SleepyUnicon/Overwatch/case/2_bezel_back.png

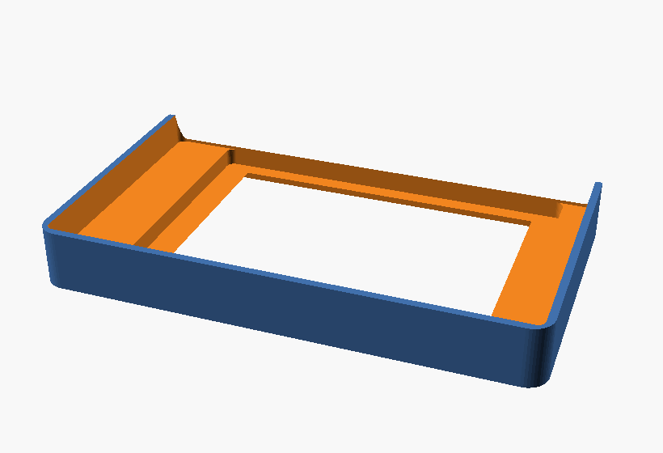
case/2_bezel_back.png
