SleepyUnicon/Overwatch/case/4_tray_vents.png

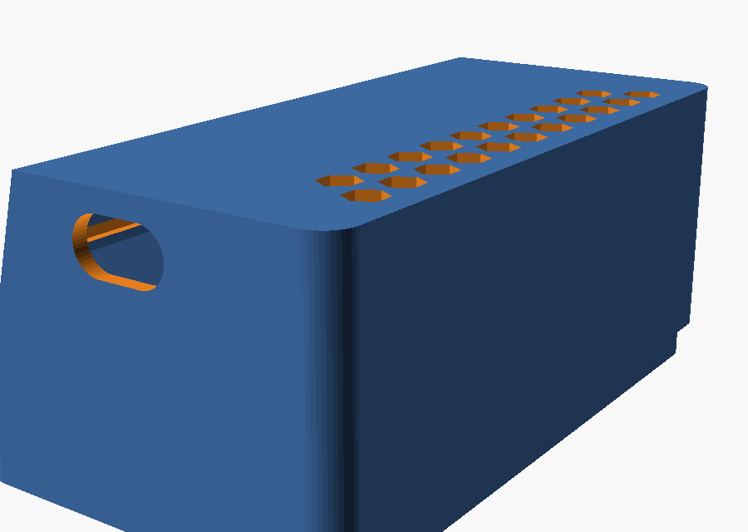
case/4_tray_vents.png
