SleepyUnicon/Overwatch/case/6_tray_right.png

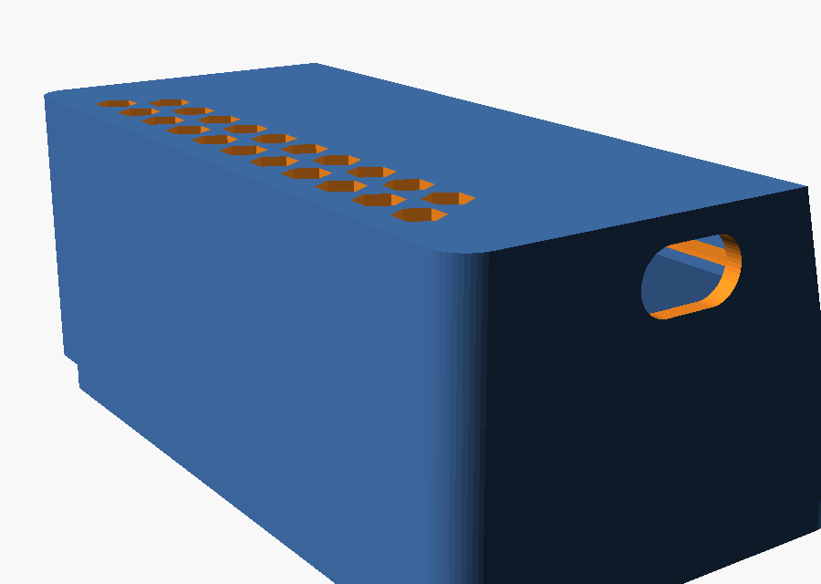
case/6_tray_right.png
