SleepyUnicon/Overwatch/case/7_tray_iso.png

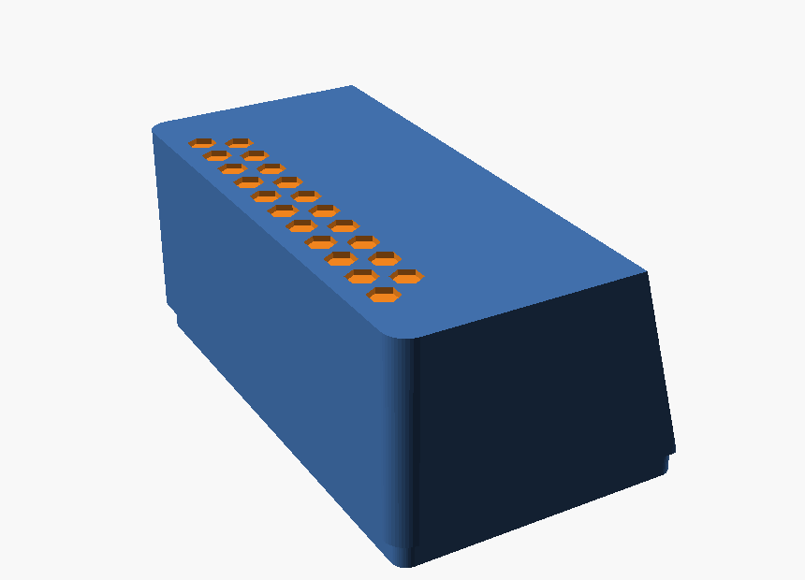
case/7_tray_iso.png
