SleepyUnicon/Overwatch/case/v2/1_face.png

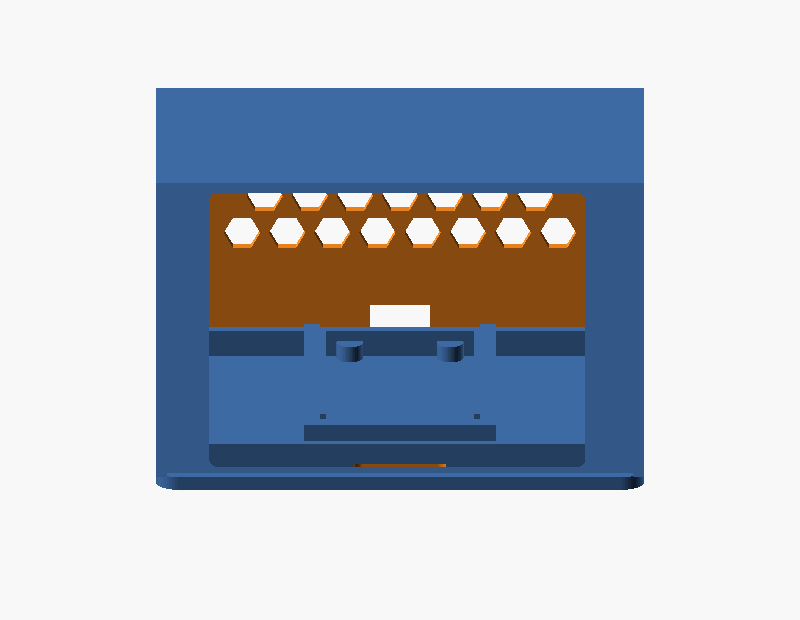
case/v2/1_face.png
