SleepyUnicon/Overwatch/case/v2/2_iso.png

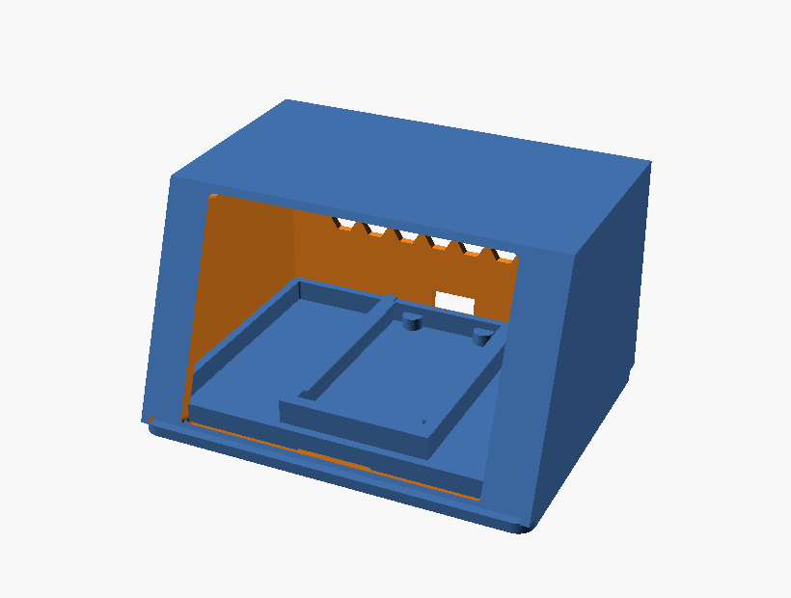
case/v2/2_iso.png
