SleepyUnicon/Overwatch/case/v2/3_back_vent.png

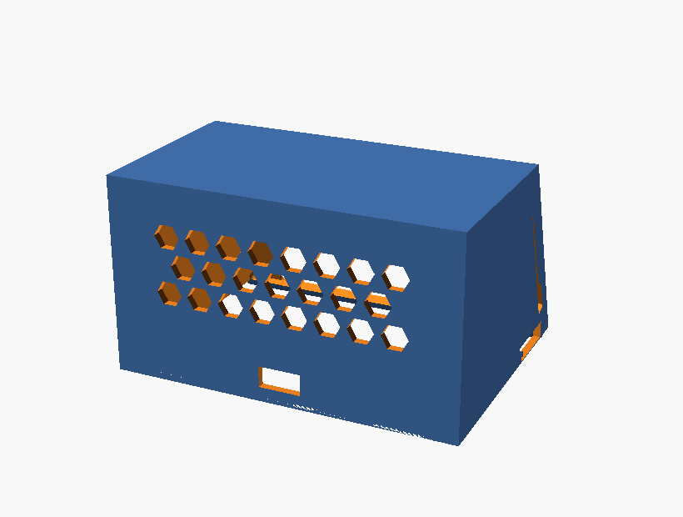
case/v2/3_back_vent.png
