SleepyUnicon/Overwatch/case/v2/4_side.png

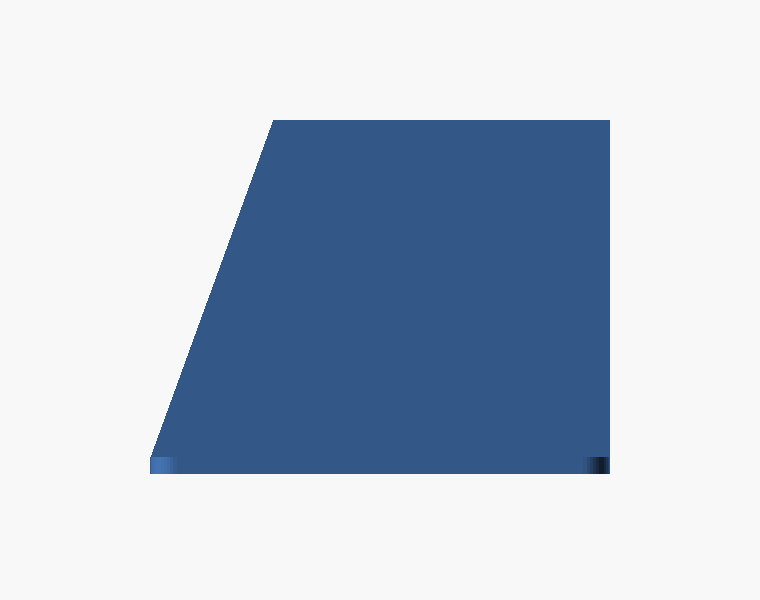
case/v2/4_side.png
