SleepyUnicon/Overwatch/case/v2/5_base.png

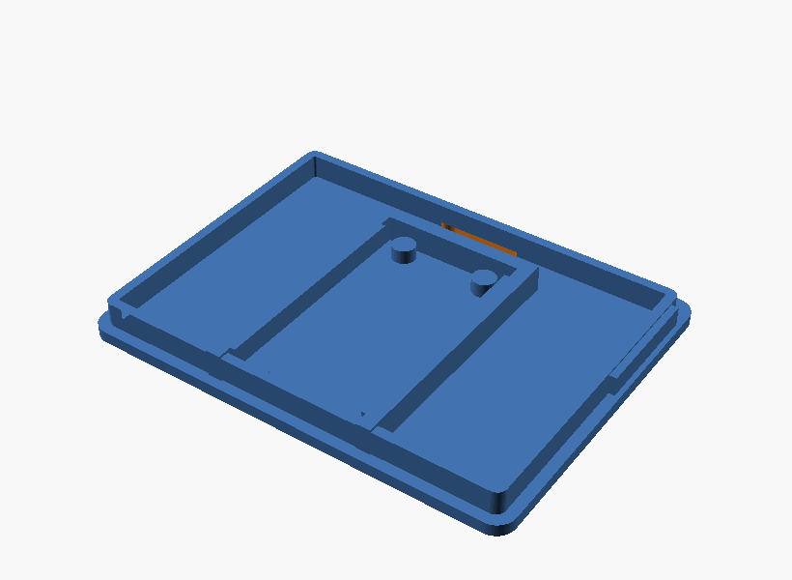
case/v2/5_base.png
