SleepyUnicon/Overwatch/case/v2/6_key.png

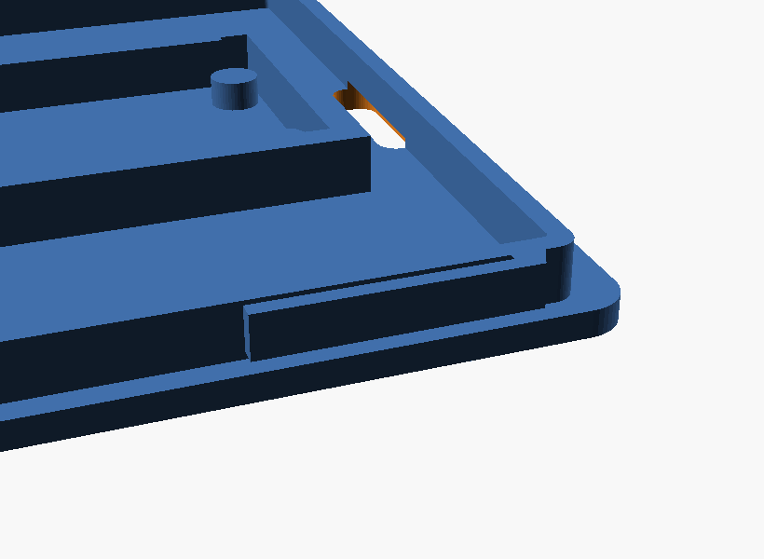
case/v2/6_key.png
