SleepyUnicon/Overwatch/design/car-dial/dial_actual_size.png

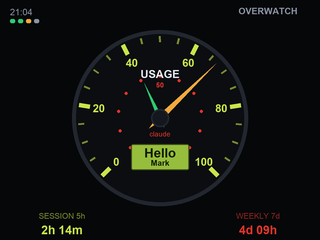
design/car-dial/dial_actual_size.png
