SleepyUnicon/Overwatch/reveal/page_gauges.png

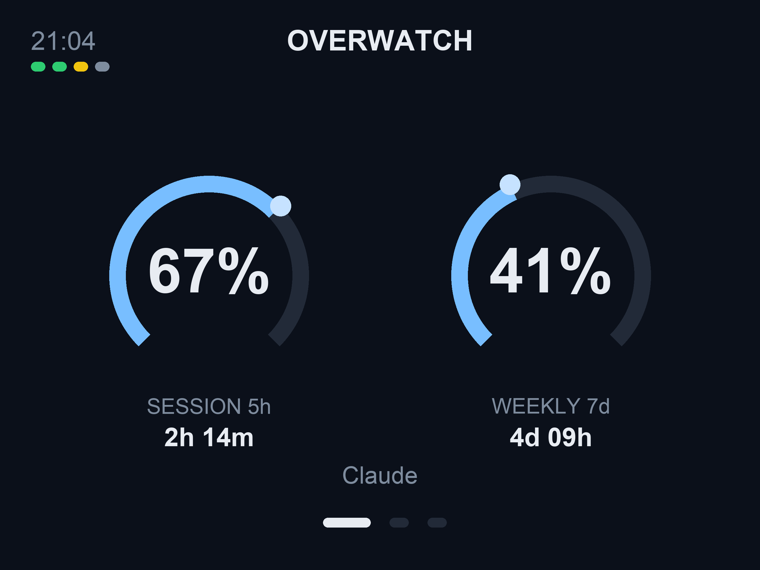
reveal/page_gauges.png
