SleepyUnicon/Overwatch/reveal/page_spotify.png

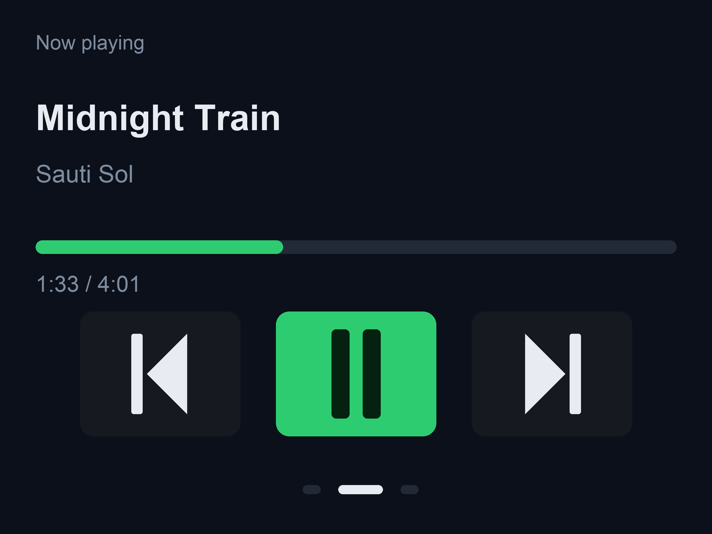
reveal/page_spotify.png
