SleepyUnicon/Overwatch/reveal/screen_strip.png

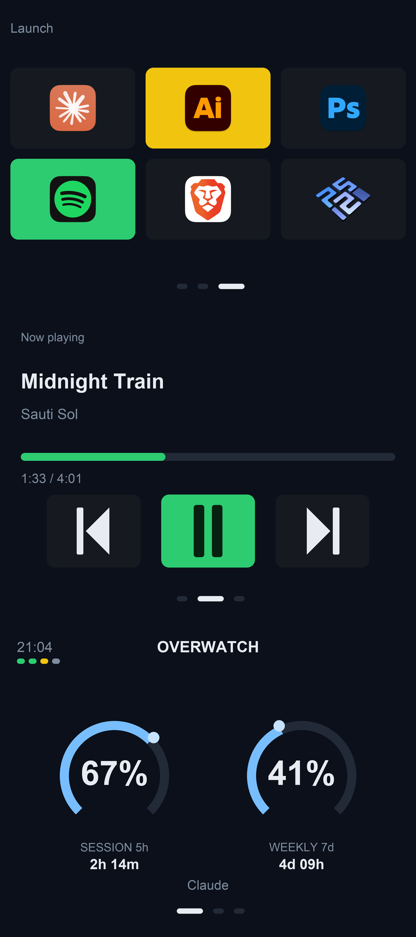
reveal/screen_strip.png
