SleepyUnicon/Overwatch/pc/cli.py

"""One binary: the setup, the status check, and the bridge itself.

A customer downloads a single file and runs it. There is no Python to install,
no virtualenv to build, no repository to clone, and nothing left behind that
they have to keep in place -- `overwatch install` copies the binary into
~/.overwatch/bin and points the login service at that copy, so the download is
disposable the moment it finishes.

This replaces install.sh. The shell version needed Python 3.9+ on the machine,
built a virtualenv, and pulled two packages from PyPI at install time -- three
things that could fail on a customer's machine for reasons they could do
nothing about, and one of them (an unpinned PyPI resolve) meant two people
installing a week apart could get different software.

The status line shim stays a shell script on purpose. It runs on EVERY status
line render, many times a minute, and a frozen binary takes 100-400 ms to start
because it unpacks itself first -- that delay would land in the customer's
prompt. A few lines of sh start in single-digit milliseconds.
"""
import argparse
import glob
import os
import shutil
import subprocess
import sys
import textwrap
import time

from pc import (install_codex_hooks, install_hooks, install_statusline,
                macperm, ota,
                protocol, statusline_source, update, win_driver)
# Eagerly, unlike the other providers, which are imported inside the functions
# that use them to keep the frozen binary's start-up cheap. This one costs
# nothing to import (os, and claude_state, which is json/os/sys/time) and it
# has to be a module attribute rather than a local: `overwatch status` reads it,
# and a test has to be able to replace it without a real slot directory in
# reach -- the scan behind it deletes files.
from pc.providers import codex_state
from pc.version import RELEASE_VERSION

# Resolved per call, not at import. These used to be module constants, which
# meant every path was fixed by whatever HOME happened to be when the module
# loaded -- untestable without a subprocess, and quietly wrong for any caller
# that changes HOME.
LABEL = "com.overwatch.bridge"


def _home():
    return os.path.expanduser("~")


def overwatch_home():
    return os.path.join(_home(), ".overwatch")


def bin_dir():
    return os.path.join(overwatch_home(), "bin")


def installed_bin():
    # .exe on Windows: without the extension the copy is not executable, and
    # the Scheduled Task would register a path Windows refuses to launch.
    name = "overwatch.exe" if sys.platform == "win32" else "overwatch"
    return os.path.join(bin_dir(), name)


def shim_path():
    return os.path.join(overwatch_home(), "overwatch-statusline.sh")


def hook_shim_path():
    return os.path.join(overwatch_home(), "overwatch-hook.sh")


def log_path():
    return os.path.join(overwatch_home(), "bridge.log")


def log_hint():
    """Where to actually READ the log on this platform.

    Not the same as log_path(), and the difference cost a person sixteen
    hours. launchd is told StandardOutPath and writes bridge.log; the systemd
    unit says nothing about output, so on Linux everything goes to the journal
    and bridge.log is never created. `install` printed the path anyway, so a
    Linux user following their own install output finds no such file, and
    concludes the daemon never ran -- while it is running, and has been
    logging the reason it cannot work, somewhere else.

    Windows keeps the file: the Scheduled Task runs the daemon through a shim
    that redirects into it.
    """
    if sys.platform.startswith("linux"):
        return "journalctl --user -u overwatch-bridge"
    return log_path()


def launcher_path():
    """The script the Scheduled Task runs, so the bridge starts with no window.

    A console program started by a Scheduled Task gets a console window, and
    on the first Windows machine it was installed on that window sat on the
    desktop for as long as the service ran (2026-08-29: "it should be some
    service in the background, not a UI app"). wscript.exe can start a
    program with its window hidden; this is the one-line script that asks
    it to. Written in ASCII with the profile taken from the environment,
    because a non-ASCII path inside a .vbs depends on the machine's code
    page, and the machine in question had a Hebrew user name.
    """
    return os.path.join(overwatch_home(), "overwatch-bridge.vbs")


LAUNCHER_VBS = "\n".join((
    "' Starts the OVERWATCH bridge with no window. Written by `overwatch install`;",
    "' the Scheduled Task \"Overwatch bridge\" runs it at every logon.",
    'Set sh = CreateObject("WScript.Shell")',
    'home = sh.ExpandEnvironmentStrings("%USERPROFILE%")',
    # VBScript doubles a quote to embed one: this runs
    #   "<home>\.overwatch\bin\overwatch.exe" run --log "<home>\.overwatch\bridge.log"
    # with window style 0 (hidden) and without waiting for it to finish.
    'sh.Run """" & home & "\\.overwatch\\bin\\overwatch.exe"" run --log """'
    ' & home & "\\.overwatch\\bridge.log""", 0, False',
    "",
))


def pid_path():
    """Where the running daemon records its pid: ~/.overwatch/bridge.pid.

    Derived from the program's own location (its directory's parent), not
    from ~. A login service runs in the user's environment rather than the
    one that registered it, so the two can disagree about what ~ is -- and
    when they do, the pid lands where nothing will look for it.

    Beside the program, not inside its directory: an update rotates
    ~/.overwatch/bin to bin.old with the old daemon still running from it, and a
    pid file that moved with the directory is one restart() can no longer
    find -- leaving the old daemon holding the serial port against the new.
    """
    return os.path.join(overwatch_home(), "bridge.pid")


def pid_paths():
    """Every place a daemon may have left its pid.

    The same set _kill_recorded_daemon sweeps, named once so that "is it
    running?" and "stop it" cannot drift apart -- and with the frozen
    build's own choice added. claude_usage_bridge writes beside its
    directory when frozen, which IS pid_path() once installed but lands in
    the build directory when the binary is run in place.
    """
    paths = [pid_path(),
             os.path.join(bin_dir(), "bridge.pid"),
             os.path.join(bin_dir() + ".old", "bridge.pid")]
    if _frozen():
        paths.append(os.path.join(
            os.path.dirname(os.path.dirname(_self_path())), "bridge.pid"))
    # And beside whatever binary we would START, which is not always one of
    # the above: a frozen build run in place out of dist/ writes its pid
    # there. Without this the page reported "Started (pid N)" and then, one
    # poll later, "Not running" -- both true, neither useful.
    cmd = daemon_start_command()[0]
    if len(cmd) == 2:                     # an overwatch binary, not `python -m`
        paths.append(os.path.join(
            os.path.dirname(os.path.dirname(cmd[0])), "bridge.pid"))
    seen, out = set(), []
    for q in paths:
        if q not in seen:
            seen.add(q)
            out.append(q)
    return tuple(out)


def daemon_holding_lock():
    """Whether a daemon holds ~/.overwatch/bridge.lock. None if it cannot be told.

    Better than the pid file wherever it works, for three reasons: the path
    is fixed however the binary was installed or run, the kernel drops the
    lock when the process dies however it dies, and a recycled pid cannot
    impersonate it. claude_usage_bridge takes this lock for the daemon's
    whole life so that two of them cannot interleave on one cable.

    None means "cannot tell from here" -- Windows has no flock (there the
    exclusive port is the lock), and neither has an unwritable home. The pid
    sweep answers those.

    Opened "a", never "w": the daemon's own open truncates, and a status
    check has no business doing that to a file another process is holding.
    """
    try:
        import fcntl
    except ImportError:
        return None
    path = os.path.join(overwatch_home(), "bridge.lock")
    if not os.path.exists(path):
        return False                  # no daemon has ever run here
    try:
        fh = open(path, "a", encoding="utf-8")
    except OSError:
        return None
    try:
        fcntl.flock(fh.fileno(), fcntl.LOCK_EX | fcntl.LOCK_NB)
    except OSError:
        return True                   # somebody holds it
    else:
        fcntl.flock(fh.fileno(), fcntl.LOCK_UN)
        return False
    finally:
        fh.close()


def daemon_running():
    """Is a bridge daemon running? The lock first, the pid file second.

    Two answers because neither is available everywhere. The lock is the
    better one and is what POSIX gets; Windows has no flock, so there the
    pid sweep -- with its image-name filter against recycled pids -- is the
    whole answer.
    """
    held = daemon_holding_lock()
    if held is not None:
        return held
    return daemon_alive() is not None


def daemon_alive(runner=None):
    """The pid of a running bridge daemon, or None.

    Signal 0 alone is not enough. A pid is recycled after a reboot, and the
    number the daemon wrote can belong to something else entirely by the
    time anyone asks -- which would report a stopped daemon as healthy. So
    the process's NAME is checked too, the same filter the Windows backend
    already applies to tasklist for the same reason.

    Nothing here raises: this answers a status question, and a status
    question that throws is worse than one that says "no".
    """
    run = runner or subprocess.run
    for path in pid_paths():
        try:
            with open(path, encoding="utf-8") as f:
                pid = int(f.read().strip())
        except (OSError, ValueError):
            continue
        if pid == os.getpid():
            continue
        try:
            if sys.platform == "win32":
                out = run(["tasklist", "/fi", "PID eq %d" % pid,
                           "/fi", "IMAGENAME eq "
                           + os.path.basename(installed_bin()),
                           "/nh", "/fo", "csv"],
                          capture_output=True, text=True,
                          **update.ota.NO_WINDOW)
                # tasklist exits ZERO with no match and prints a notice,
                # so the pid has to appear in the output to count.
                if str(pid) in (out.stdout or ""):
                    return pid
                continue
            out = run(["ps", "-p", str(pid), "-o", "comm="],
                      capture_output=True, text=True, timeout=5)
        except (OSError, subprocess.SubprocessError):
            continue
        name = os.path.basename((out.stdout or "").strip()).lower()
        if name and ("overwatch" in name or "python" in name):
            return pid
    return None


def daemon_start_command():
    """How to start the bridge on this machine, as (command, cwd).

    The installed binary first -- that is what the login service runs and
    what a kit user has. Then this program, when it is the frozen build
    being run in place. Only then the checkout, which needs pyserial in the
    interpreter running it: true for a developer, not for anybody else.

    The cwd travels WITH the command because it is not free to choose. A
    binary can be started from anywhere and ~/.overwatch is the tidiest place
    for it; `-m pc.cli` cannot, because Python resolves the package from
    the working directory and started anywhere else it exits on
    "No module named 'pc'".
    """
    inst = installed_bin()
    if os.path.exists(inst):
        return [inst, "run"], overwatch_home()
    if _frozen():
        return [_self_path(), "run"], overwatch_home()
    root = os.path.dirname(os.path.dirname(os.path.abspath(__file__)))
    return [sys.executable, "-m", "pc.cli", "run"], root


def settings_path():
    return os.path.join(_home(), ".claude", "settings.json")


def plist_path():
    return os.path.join(_home(), "Library", "LaunchAgents", LABEL + ".plist")


def unit_path():
    return os.path.join(_home(), ".config", "systemd", "user",
                        "overwatch-bridge.service")


# Windows has no launchd and no systemd. A Scheduled Task with an at-logon
# trigger is the equivalent that needs no admin rights and no service wrapper.
TASK_NAME = "Overwatch bridge"

# The oldest Claude Code that carries usage figures in its status line payload.
# 2.1.0 does not carry rate_limits at all; 2.1.100 does. Below this every step
# of the install succeeds and the panel stays blank forever.
MIN_CLAUDE = (2, 1, 100)

# Set by the tests to skip registering a real login service. The launchd label
# and the systemd unit name are constants while everything else is scoped to
# $HOME, so without this a test under a temporary HOME still boots out the
# real agent of whoever is logged in.
def _skip_service():
    return os.environ.get("OVERWATCH_SKIP_SERVICE") == "1"


def _frozen() -> bool:
    return getattr(sys, "frozen", False)


def _self_path() -> str:
    """The binary to copy into place. sys.executable is the frozen binary."""
    return sys.executable if _frozen() else os.path.abspath(sys.argv[0])


def _shim_source(name: str = "overwatch-statusline.sh") -> str:
    """A shim's text, from the bundle when frozen, the tree when not.

    One source of truth either way -- tools/ is what the build embeds, so the
    shipped shim and the one in the repository cannot drift apart. Any new
    shim added here must also be added to the --add-data list in
    tools/build_binary.sh, or it will work from a checkout and be missing
    from every shipped binary.
    """
    if _frozen():
        base = getattr(sys, "_MEIPASS", os.path.dirname(_self_path()))
        return open(os.path.join(base, name), encoding="utf-8").read()
    here = os.path.dirname(os.path.dirname(os.path.abspath(__file__)))
    return open(os.path.join(here, "tools", name), encoding="utf-8").read()


def _write_shim(path: str, name: str) -> None:
    # newline="\n", or Windows writes the shim with CRLF and Git Bash then
    # fails on `case ... in\r` on every status line render and every tool
    # call. The CI CRLF check only ever looked at the files in the repository,
    # never at the copy this function installs.
    # Temp file plus os.replace, NOT open(path, "w").
    #
    # Truncate-in-place has a window in which this file is empty or half
    # written, and Claude Code runs this exact script on EVERY tool call. A
    # hook that starts inside that window hands `sh` an empty file, or a
    # truncated trailing line -- which exits non-zero and gives the tool a
    # FAILING hook. The shim's own closing `exit 0` exists precisely so that
    # Overwatch having a bad day never becomes the user's bad day, and truncating
    # the script defeats it from outside.
    #
    # The window used to be one write during an explicit install, which is bad
    # but rare and observed. This branch made DriftWatchdog call it from the
    # daemon's poll loop, so the same window now opens on a timer, in the
    # background, on a machine whose owner is working. install_statusline._save
    # already writes this way for the user's settings, and the shim's own slot
    # write already uses a pid-named temp plus mv -f; this was the one write
    # that skipped the idiom, and it is the one that became recurring.
    #
    # The temp file is a sibling so os.replace is atomic, and the mode is set
    # BEFORE the rename so the file is never briefly present and non-executable.
    tmp = "%s.overwatch-tmp.%d" % (path, os.getpid())
    try:
        with open(tmp, "w", encoding="utf-8", newline="\n") as f:
            f.write(_shim_source(name))
        os.chmod(tmp, 0o755)
        os.replace(tmp, path)
    except OSError:
        try:
            os.unlink(tmp)
        except OSError:
            pass
        raise


def shim_is_current(path: str, name: str) -> bool:
    """Is the shim at `path` byte-identical to the one we would install?

    Byte-identical, not "close enough": the one difference that has actually
    bitten was line endings, and a comparison that normalised them would have
    called the broken file healthy. Read in binary and compare exactly.

    False on any failure to read. The caller's response to "stale" and to "I
    cannot tell" is the same -- write it again -- and this runs inside the
    daemon's poll loop, where raising is the one outcome worse than a shim
    that stays stale for another five minutes.
    """
    try:
        with open(path, "rb") as f:
            installed = f.read()
    except OSError:
        return False

    try:
        expected = _shim_source(name).encode("utf-8")
    except (OSError, UnicodeDecodeError):
        # The bundle itself is unreadable -- or, since _shim_source opens
        # with encoding="utf-8", readable but not valid UTF-8, which raises
        # UnicodeDecodeError (a ValueError, not an OSError, so it needs its
        # own arm here). Either way there is nothing to compare against.
        # Claiming the installed shim is stale would start a rewrite that
        # cannot succeed and would log the failure every tick; claiming it
        # is current changes nothing. Say current and let the louder failure
        # surface elsewhere.
        return True

    return installed == expected


# ---------------------------------------------------------------- Claude Code


def claude_version():
    """(text, tuple) for the Claude Code on PATH, or (None, None)."""
    exe = shutil.which("claude")
    if not exe:
        return None, None
    try:
        out = subprocess.run([exe, "--version"], capture_output=True, text=True,
                             timeout=30).stdout.strip()
    except Exception:
        return None, None
    head = out.split()[0] if out else ""
    pieces = head.split(".")[:3]
    # Every component has to be a number, or we did not parse a version.
    # Mapping the odd ones to 0 meant "claude version unknown" came back as
    # (0, 0, 0) -- below every floor, so a perfectly good install was reported
    # as TOO OLD, and callers testing `ver is None` never saw it coming.
    if not pieces or not all(x.isdigit() for x in pieces):
        return (out or None), None
    parts = [int(x) for x in pieces]
    while len(parts) < 3:
        parts.append(0)
    return (out or None), tuple(parts)


def desktop_app_present() -> bool:
    """Has Claude Desktop ever written its usage cache on this machine?

    The file, not the application bundle. An installed app that has never run
    has nothing for us to read, and a machine where the app was removed but
    the cache remains still has a (stale, and reported as stale) reading. The
    file is the thing this product actually depends on, so the file is what
    gets asked about.
    """
    from pc.providers import claude_desktop
    try:
        return os.path.exists(claude_desktop.cache_path())
    except Exception:
        return False


def desktop_staleness_note(age_s):
    """Why a Claude Desktop reading is old -- or nothing, when it is not.

    Claude Desktop does not write its usage cache on a clock. It writes after
    a usage fetch, and it only fetches while somebody is actually at the
    machine: step away, lock the screen or let the machine sleep and the file
    simply stops growing. The app is still running and still right, it is
    just not asking. A reading hours old is therefore the ordinary shape of
    "nobody was here", not a fault, and a panel showing one is not stuck.

    Measured from Claude.app 1.40609.0 on 2026-08-31, by reading its own
    bundle and then watching it run: the poll is 15 minutes by default and
    5 only for the half hour after the menubar panel has been opened, it
    skips the fetch entirely once the system has been idle ten minutes or
    the screen is locked, and it fetches at launch and again every time the
    menubar icon is opened. Opening that icon is the one action that
    refreshes on demand: focusing the app window fetches nothing, because
    the chat runs in a web view that never touches this file.

    None of those intervals is quoted below on purpose. They belong to an
    application we do not control, they have already changed twice (a flat
    5 minutes when pc/providers/claude_desktop.py was written, then the
    tray-gated 5/15 split around 2026-08-21 -- arriving without an app
    update, so the cadence is server-controlled and can move again), and a
    number that goes quietly wrong is worse here than no
    number: the reader needs the shape, which does not change, and the one
    action that works.
    """
    from pc.providers import claude_desktop
    if age_s is None or age_s < claude_desktop.STALE_AFTER_S:
        return []
    return [
        "Claude Desktop refreshes this only while you are at the machine,",
        "and stops once it has been idle a while -- so a reading this old",
        "usually means nobody was here, not that anything is broken.",
        "Click the Claude icon in your menu bar to refresh it now.",
    ]


def codex_present() -> bool:
    """Has Codex CLI written a rollout log on this machine?

    The logs, not the binary, for the reason desktop_app_present() gives: the
    file the daemon reads is the thing that matters.
    """
    from pc.providers import codex_cli
    try:
        return bool(codex_cli.recent_rollouts(limit=1))
    except Exception:
        return False


def _announce_codex_hooks() -> None:
    """Say what is about to happen in Codex, before it happens.

    Install is deliberately unattended, so disclosure is the only thing
    standing between us and configuring a SECOND vendor's tool without saying
    so -- and this one is not the tool the customer came here for. The trust
    prompt is the part that has to be said out loud: Codex asks once, in its
    own interface, minutes or days later, and an unexplained dialog from a
    tool the person did not think they were configuring is a support incident
    rather than a feature.

    Wrapped continuation lines start lower case on purpose. The house rule is
    that every sentence starts with a capital; a line that continues one is
    not a new sentence, and capitalising it would read as a stutter.
    """
    print("Overwatch is about to add a hook to Codex as well.")
    print()
    print(f"  File     {install_codex_hooks.hooks_file()}")
    print("  Why      Codex does not record permission prompts in its session")
    print("           log, so without this a Codex session waiting on you")
    print("           looks idle on the panel.")
    print("  Note     The first time the hook runs, Codex asks you once")
    print("           whether to trust it. That prompt is expected, and Overwatch")
    print("           cannot answer it for you. Say yes and the panel can show")
    print("           a Codex session waiting on you; say no and everything")
    print("           else still works.")
    print()


def _install_codex_hooks() -> str:
    """Register the shim with Codex, if there is a Codex here to register with.

    Detected rather than asked about, the same way the Claude Code steps are:
    the product is meant to be plug-and-play. Absent Codex, nothing is written
    at all -- creating a hooks file for a tool that is not installed would
    leave a stranger's configuration on the machine.

    No pointer is written into Codex's config.toml, and none is needed:
    hooks.json is discovered by location alone, verified by firing a real hook
    against a config that mentioned hooks nowhere
    (docs/research/codex-hook-contract.md, F3).
    """
    if not codex_present():
        return "no Codex on this machine, nothing to do"
    # Private to the user, for the same reason ~/.overwatch/state is: these files
    # name the projects someone has open, and the default umask would leave
    # them readable by every account on the machine. Created here rather than
    # left to the shim so the mode is right from the first hook onward.
    state_dir = os.path.join(overwatch_home(), "state-codex")
    os.makedirs(state_dir, exist_ok=True)
    try:
        os.chmod(state_dir, 0o700)
    except OSError:
        pass                 # Windows, where the mode does not apply
    try:
        return install_codex_hooks.install(install_codex_hooks.hooks_file(),
                                           hook_shim_path())
    except install_statusline.SettingsUnreadable as e:
        # Same judgement as the Claude hooks step: the status line is the
        # product and the activity light is a nicety. A hooks file we cannot
        # safely edit costs the user a pip, and is not worth failing an
        # install that has otherwise worked -- still less worth "repairing"
        # another vendor's config by writing our idea of it over theirs.
        return f"skipped ({e})"


def _note_if_no_claude_code():
    """Say what this machine will and will not show, when Claude Code is absent.

    Steps 2 and 3 of the install write a status line and a set of hooks into
    ~/.claude/settings.json. With no Claude Code on the machine nothing ever
    reads that file, so both steps report success and produce nothing -- and
    the customer is left with a device that half works and no way to find out
    why. That is the worst shape a first run can have, and it cost nothing to
    keep quiet about, which is why it stayed quiet.

    A note, not a refusal, and not a failed step. The edits are correct and
    stay correct: install Claude Code tomorrow and it all starts working with
    nothing to redo. Same reasoning as _warn_if_claude_too_old below.
    """
    text, _ = claude_version()
    if text is not None:
        return

    print()
    if codex_present() and not desktop_app_present():
        # A Codex machine. The daemon has known about Codex for a while; this
        # message did not, and told a Codex-edition customer that nothing on
        # the machine reports usage and to install Claude Code.
        print("  !  Claude Code is not installed, so the panel runs on Codex")
        print("     alone: both Codex limits and their countdowns, from the")
        print("     session log Codex already writes. The Claude page stays")
        print("     empty, and there is no activity light -- that needs")
        print("     Claude Code's hooks. The status line and hooks just")
        print("     installed start working by themselves if you add it later.")
        return
    if not desktop_app_present():
        # No source exists. This is not a reduced panel, it is an empty
        # one, and saying anything softer would be misleading.
        print("  !! Nothing on this machine reports usage yet.")
        print("     Overwatch reads figures that Claude Code, Claude Desktop or")
        print("     Codex have already worked out. With none of them installed")
        print("     the panel will connect and then sit blank.")
        print()
        print("       npm install -g @anthropic-ai/claude-code@latest")
        print()
        print("     Nothing here needs redoing afterwards -- it starts on its own.")
        return

    print("  !  Claude Code is not installed, so the panel runs on")
    print("     Claude Desktop alone. That works, with less on it:")
    print()
    print("       Shown    both usage percentages, and how fast the")
    print("                five-hour window is filling")
    print("       Missing  the reset countdowns, and the activity light")
    print()
    # Why, not just what. The countdowns are the part people ask about, and
    # "it is not implemented yet" would be the wrong answer -- there is
    # nothing to implement. Verified across every file, LevelDB store and
    # cache the desktop app writes, 2026-08-28.
    print("     Claude Desktop does not record when either window resets --")
    print("     anywhere, in any file -- so there is no countdown to show and")
    print("     the panel shows a rate instead. The activity light needs")
    print("     Claude Code's hooks.")
    print()
    print("     The status line and hooks just installed are correct and will")
    print("     start working by themselves if you add Claude Code later:")
    print()
    print("       npm install -g @anthropic-ai/claude-code@latest")


def _warn_if_claude_too_old():
    text, ver = claude_version()
    if ver is None or ver >= MIN_CLAUDE:
        return
    # A warning, not a refusal. Everything installed is correct and stays
    # correct, so the moment they update it starts working with nothing to
    # redo; refusing would make them run this again for no reason.
    m = ".".join(str(n) for n in MIN_CLAUDE)
    print()
    print(f"  !! Your Claude Code is {text}, and Overwatch needs {m} or newer.")
    print("     Older versions do not put the usage figures in the status line")
    print("     at all, so the panel will sit blank until you update:")
    print()
    print("       npm install -g @anthropic-ai/claude-code@latest")
    print()
    print("     Nothing else needs redoing -- it starts working on its own.")


# -------------------------------------------------------------------- service


_PLIST_TEMPLATE = """<?xml version="1.0" encoding="UTF-8"?>
<!DOCTYPE plist PUBLIC "-//Apple//DTD plist_path() 1.0//EN" "http://www.apple.com/DTDs/PropertyList-1.0.dtd">
<plist version="1.0">
<dict>
  <key>Label</key><string>{label}</string>
  <key>ProgramArguments</key>
  <array>
{args}  </array>
  <!-- Frozen Python buffers stdout when it is a file, so without this the
       log lags minutes behind the daemon and reads as a hang. -->
  <key>EnvironmentVariables</key>
  <dict><key>PYTHONUNBUFFERED</key><string>1</string></dict>
  <key>RunAtLoad</key><true/>
  <!-- The bridge waits for a board rather than exiting, so KeepAlive is a
       backstop for a crash, not the normal path. ThrottleInterval keeps a
       repeatable crash from becoming a spin. -->
  <key>KeepAlive</key><true/>
  <key>ThrottleInterval</key><integer>10</integer>
  <key>StandardOutPath</key><string>{log}</string>
  <key>StandardErrorPath</key><string>{log}</string>
</dict>
</plist>
"""

def _systemd_exec() -> str:
    """ExecStart, with every argument quoted.

    systemd splits ExecStart on whitespace, so a bare " ".join() broke on any
    space in the interpreter path, the checkout path or $HOME: with a spaced
    home the unit resolved the executable as the first fragment and failed
    with "Failed to locate executable", while `overwatch install` still printed
    "running (systemd)". The launchd and schtasks backends already quote
    per-argument; systemd was the only one that did not, and the CI scenario
    that uses a spaced home asserts only that the unit FILE exists.

    systemd's own quoting: double quotes, with \\ and \" escaped inside.
    """
    out = []
    for a in _service_command():
        out.append('"%s"' % a.replace("\\", "\\\\").replace('"', '\\"'))
    return " ".join(out)


_UNIT_TEMPLATE = """[Unit]
Description=Overwatch USB bridge

[Service]
ExecStart={command}
Environment=PYTHONUNBUFFERED=1
Restart=always
RestartSec=10

[Install]
WantedBy=default.target
"""


def _xml_escape(s: str) -> str:
    return s.replace("&", "&amp;").replace("<", "&lt;").replace(">", "&gt;")


def _service_command():
    """What the login service should run.

    Frozen, that is the copy in ~/.overwatch/bin. From a checkout it is this
    interpreter and the repo's entry SCRIPT -- not `-m pc.cli`.

    `-m` was wrong and silently so. A login service starts with no working
    directory of ours (launchd uses /), so `python -m pc.cli` could not import
    `pc` at all: the agent crash-looped on ModuleNotFoundError every
    ThrottleInterval, forever, writing the same line to bridge.log -- while
    `overwatch status` reported "registered with launchd", because registration
    is not health. Found on the author's own machine 2026-08-28, where it had
    been failing unnoticed.

    Running the script BY PATH fixes it without a WorkingDirectory or a
    PYTHONPATH: Python puts a script's own directory on sys.path, and
    overwatch_main.py sits at the repo root next to `pc/`.
    """
    if _frozen():
        return [installed_bin(), "run"]
    repo = os.path.dirname(os.path.dirname(os.path.abspath(__file__)))
    return [sys.executable, os.path.join(repo, "overwatch_main.py"), "run"]


# How long to keep asking a service manager before believing the answer.
#
# MEASURED, 2026-09-30, on the owner's Mac running `overwatch update` 2.3.0 ->
# 2.3.1. The kickstart went out at 10:21:57, this gave up at 10:22:02, and the
# new daemon's first log line is 10:22:08 -- so the service came up ELEVEN
# seconds after the bounce and the old five-second budget missed it by more
# than half. The message it printed ("launchd reports it is not running -- see
# the log") was true at the instant it was checked, useless six seconds later,
# and sent the reader to run `overwatch install` for nothing. It did that on
# two consecutive updates.
#
# Eleven seconds because `update` has just replaced a 12.8 MB PyInstaller
# bundle: macOS has to assess the signature of a freshly written binary and its
# fifty-one inner Mach-O files before it will exec any of them. A normal
# kickstart, with the binary already assessed, answers in 0.02 s -- measured
# three times running -- so a generous budget costs nothing whenever anything
# is working. It is only spent on the path that is already in trouble, and
# waiting there is better than being wrong quickly.
#
# Thirty, not eleven: that measurement is one machine, warm, with the page
# cache full of the bundle it had just written.
CONFIRM_BUDGET_S = 30.0


def _confirm_delays(budget_s=CONFIRM_BUDGET_S):
    """Escalating waits that add up to about `budget_s`.

    A LIST of sleeps rather than a wall-clock deadline, which is not a style
    choice: the tests for the failure path patch time.sleep to a no-op, and a
    deadline read off time.monotonic() would busy-spin against a clock that
    still moves -- thirty real seconds per test. Counting ticks keeps the loop
    bounded however sleep behaves.

    Short waits first so the ordinary case (0.02 s) still returns at once, then
    longer ones so a slow start is not paid for in a hundred probes.
    """
    delays, total, d = [], 0.0, 0.25
    while total < budget_s:
        delays.append(d)
        total += d
        d = min(d * 1.5, 3.0)
    return delays


def _confirm_running(probe, budget_s=CONFIRM_BUDGET_S) -> bool:
    """Keep asking a service manager whether something is REALLY running.

    All three backends had the same hole and only one of them had learned:
    they read the exit code of the command that started the service and
    called that health. An exit code says a request was accepted. Whether a
    process exists is a different question, and only the supervisor can
    answer it -- which is the lesson recorded above _service_command() and
    measured again on 2026-09-04, when five bootstraps out of five returned
    zero with nothing running.

    So this is the part that is the same everywhere -- ask, and if the answer
    is no, ask again for a few seconds -- and `probe` is the part that is not.
    It is a callable rather than an argv because the QUESTION differs per
    platform and, on Windows, so does its subject: the pid file has to be
    re-read on every attempt, because a daemon that has not started yet has
    not written one.

    See CONFIRM_BUDGET_S for how long, and for the measurement that set it.
    The old budget was five seconds and the thing it was watching took eleven.

    Returns False on anything it cannot recognise. That lean is deliberate
    and it is the whole point -- the one thing this must never do again is
    print a claim it cannot see. Which cuts both ways, and did: "I cannot see
    it" is only honest while it is still true, and saying it after five
    seconds of a start that takes eleven is its own kind of wrong answer.
    """
    said = False
    waited = 0.0
    for d in _confirm_delays(budget_s):
        if probe():
            return True
        # Something on the screen after a few seconds, or a wait this long
        # reads as a hang -- which is what the five-second budget was
        # protecting against, and worth keeping while fixing what it broke.
        if not said and waited >= 4.0:
            said = True
            print("    (still waiting for the service to come up)",
                  file=sys.stderr)
        time.sleep(d)
        waited += d
    # One last look: the final wait is the longest, and giving up without
    # spending it would make the budget shorter than it says it is.
    return bool(probe())


class _Backend:
    """One platform's answer to "start this at login, and keep it running".

    There used to be five sys.platform ladders: one each for install,
    restart, remove, the line the installer prints about what it creates,
    and status. Nothing held them together, so a case could be handled in
    four of them and forgotten in the fifth -- which is not hypothetical. A
    Linux box with no systemd got a considered answer from remove ("no
    systemd here; stop it yourself if you started it") and a shrug from
    status ("unknown on linux"), for the same machine in the same state.

    One object per platform now, chosen once by backend(). That also makes
    this code reachable from a unit test for the first time: a backend can
    be built on any machine and asked what it would run, where before the
    argv handed to launchctl, schtasks and systemctl could only be observed
    by installing for real on that platform. Three Windows defects in this
    file were found by CI rather than by a test for exactly that reason.

    The base class is not abstract -- it IS the behaviour for a platform
    with no supervisor we know how to drive, and every subclass overrides
    only the parts it can do better.
    """

    def creates(self):
        """What installing will put on disk, for the disclosure block.

        None when there is nothing to name.
        """
        return None

    def install(self) -> str:
        return (f"not supported on {sys.platform}; run it yourself: "
                f"{installed_bin()} run")

    def restart(self) -> str:
        return "not running under a supervisor; restart it yourself"

    def halt(self) -> None:
        """Stop the running daemon, leaving the service registered.

        Only Windows needs this, and only right before the update swap: it is
        the one platform that refuses to rename <bin> while the daemon holds
        bin\\overwatch.exe open. Elsewhere a rename does not care what is open, and
        stopping a daemon that launchd or systemd would restart a second later
        buys a gap on the board and nothing else. So: a no-op by default, on
        purpose.

        Not stop() below, which is deliberately a different thing: stop() is
        half of a pair a test run must be able to undo on every platform, and
        it reports what happened. This is best effort, silent, and only where
        an open file handle would otherwise fail a rename.
        """
        return None

    def stop(self, runner=None) -> str:
        """Stop the installed service, without uninstalling it.

        Restart() is what `overwatch update` needs; this pair is what a test run
        needs. The fleet suite drives the real daemon against a real board, so
        it has to take the serial port off the service that owns it and hand
        it back afterwards -- on a machine the user works on, where anything
        that touched the plist, the unit file or the Scheduled Task itself
        would rewrite their own installation on the way past. So: stop and
        start only, and a service that is not installed is an answer rather
        than an error, because start() is called from a finally block where
        an exception would replace the failure the run was there to find.

        runner is subprocess.run unless a caller substitutes one. Resolved at
        call time rather than bound as a default argument, so a test that
        stubs subprocess.run is still in charge of what this can execute.
        """
        return "not running under a supervisor; stop it yourself"

    def start(self, runner=None) -> str:
        """Start the installed service again. See stop() for the pair.

        Not a restart: this assumes stop() ran, and does not go looking for
        anything else to kill. A caller that wants both is asking for
        restart().
        """
        return "not running under a supervisor; start it yourself"

    def remove(self) -> str:
        return "nothing to remove"

    def status(self) -> str:
        return f"unknown on {sys.platform}"


# launchctl exits with an errno. ESRCH is what booting out a job launchd is
# not running gives back ("Boot-out failed: 3: No such process"), which is an
# answer rather than a failure -- see _LaunchdBackend.stop.
_ESRCH = 3


class _LaunchdBackend(_Backend):
    def creates(self):
        return plist_path()

    def install(self) -> str:
        os.makedirs(os.path.dirname(plist_path()), exist_ok=True)
        with open(plist_path(), "w", encoding="utf-8") as f:
            args = "".join(f"    <string>{_xml_escape(a)}</string>\n"
                           for a in _service_command())
            f.write(_PLIST_TEMPLATE.format(label=LABEL, args=args,
                                           log=_xml_escape(log_path())))
        uid = os.getuid()
        # bootout first so a rerun replaces the running agent rather than
        # failing with "service already loaded".
        subprocess.run(["launchctl", "bootout", f"gui/{uid}/{LABEL}"],
                       capture_output=True, **update.ota.NO_WINDOW)
        # ...and then retry, because bootout is asynchronous. The bootstrap
        # immediately after it can fail while launchd is still tearing the old
        # job down, which left a reinstall with no service running at all --
        # observed on the second install of the day, silently.
        #
        # That retry is still worth having, but it was only ever half of this
        # story: it guards a bootstrap that FAILS. A bootstrap that succeeds
        # also starts nothing. Measured on a live machine, with this very
        # plist (RunAtLoad is set in _PLIST_TEMPLATE):
        #
        #   launchctl bootout   gui/501/com.overwatch.bridge   -> rc 0
        #   launchctl bootstrap gui/501 <plist>            -> rc 0
        #   launchctl print     gui/501/com.overwatch.bridge   -> "not running",
        #                                                     runs = 0
        #                          (still not running six seconds later)
        #   launchctl kickstart gui/501/com.overwatch.bridge   -> running, runs = 1
        #
        # So bootstrap registers the job and kickstart is what runs it. Until
        # this line existed the customer was told "running (launchd)" about a
        # job that was registered and idle, and that would not have actually
        # started before their next login.
        for attempt in range(4):
            r = subprocess.run(["launchctl", "bootstrap", f"gui/{uid}", plist_path()],
                               capture_output=True, **update.ota.NO_WINDOW)
            if r.returncode == 0:
                break
            time.sleep(0.5 * (attempt + 1))
        if r.returncode != 0:
            return ("installed, but could not be started: "
                    f"launchctl bootstrap gui/{uid} {plist_path()}")

        # BOOTSTRAP REGISTERS; IT DOES NOT START. A successful bootstrap means
        # launchd has accepted the job, not that anything is running.
        #
        # And this is not a race that sometimes loses. Measured 2026-09-04 by
        # running the old sequence -- bootout, bootstrap, no kickstart -- five
        # times in a row against this very plist: `bootstrap` returned 0 every
        # time and launchd reported "not running" every time. FIVE OUT OF FIVE.
        # RunAtLoad is honoured at LOGIN, not on a bootstrap, so an install left
        # the daemon dead until the user next logged in -- while the installer
        # said it was running. That is why it stayed hidden: anyone who rebooted
        # between installing and looking saw a working service.
        #
        # The observation that started it, straight after an install that had
        # just printed "running (launchd)":
        #
        #     active count = 0
        #     state = not running
        #     last exit code = (never exited)
        #
        # The board went quiet and dozed while the installer said it was fine.
        # This is the same defect tools/burn.sh has in its restore path, and
        # the same lesson _service_command() already records one screen up:
        # registration is not health.
        subprocess.run(["launchctl", "kickstart", "-k", f"gui/{uid}/{LABEL}"],
                       capture_output=True, **update.ota.NO_WINDOW)

        # And then ASK, rather than assume. Everything above is a command that
        # returned zero; none of it is evidence that a process exists. launchd
        # is the only thing that knows, so the claim we print is its answer and
        # not our hope.
        if _confirm_running(lambda: self._is_running(uid)):
            return "running (launchd)"
        return ("registered with launchd, but it is not running -- "
                f"start it with: launchctl kickstart -k gui/{uid}/{LABEL}")

    def _is_running(self, uid) -> bool:
        """Does launchd say a process actually exists? Its answer, not ours.

        Asked by install() and restart() because they were making the same
        claim from different evidence, and only one of them had learned. An
        exit code says a command was accepted; `launchctl print` is the only
        thing that says a process is running, so both ask it.

        One ask. The retrying belongs to _confirm_running(), which the other
        two backends need for the same reason: a kickstart hands the job to
        launchd and returns, so the exec can still be in flight when the first
        print lands.

        Parsed the same defensive way status() is -- launchctl print is a
        human-readable dump, not a contract.
        """
        pr = subprocess.run(["launchctl", "print", f"gui/{uid}/{LABEL}"],
                            capture_output=True, text=True,
                            **update.ota.NO_WINDOW)
        return pr.returncode == 0 and "state = running" in (pr.stdout or "")

    def restart(self) -> str:
        """Bounce the agent, then check that it came back.

        The old body returned "restarted" whenever kickstart exited zero,
        which is the exact defect install() was measured making on 2026-09-04:
        five bootstraps out of five returned zero with nothing running. A
        kickstart is a request to launchd, and a request that was accepted is
        not a process that exists.

        It matters most on the path that calls this. `overwatch update` swaps the
        binary underneath the agent and then bounces it; if the new binary
        cannot start -- a bad download, a missing dylib -- kickstart still
        succeeds and launchd's respawns still fail. Saying "restarted" there
        would send the user away from the one file that explains it.
        """
        uid = os.getuid()
        r = subprocess.run(["launchctl", "kickstart", "-k",
                            f"gui/{uid}/{LABEL}"], capture_output=True, **update.ota.NO_WINDOW)
        if r.returncode != 0:
            return "could not restart it"
        if _confirm_running(lambda: self._is_running(uid)):
            return "restarted"
        # Not a command to paste this time: the command that would have been
        # printed is the one that just ran and left nothing running. What is
        # left to do is read why it died.
        return ("restarted, but launchd reports it is not running -- "
                f"see {log_path()}")

    def stop(self, runner=None) -> str:
        """bootout, not `launchctl stop`.

        The plist sets KeepAlive, so a stopped job is one launchd starts
        straight back up -- the process would be gone for about a second and
        the serial port would be held again before anything else could take
        it. bootout unloads the job; the plist stays exactly where it is, and
        start() below bootstraps that same file back in.

        A job that is not loaded is stopped, not a failure. launchctl exits
        with an errno, and booting out something launchd has never heard of
        gives ESRCH -- "Boot-out failed: 3: No such process". That is an
        ordinary state: a plist on disk whose agent was already booted out,
        by a previous run or by hand. Reported as a failure it aborts the
        fleet agent with "the serial port is probably still held", about a
        port that is in fact free.
        """
        if not os.path.exists(plist_path()):
            return "not installed"
        uid = os.getuid()
        r = (runner or subprocess.run)(
            ["launchctl", "bootout", f"gui/{uid}/{LABEL}"],
            capture_output=True, **update.ota.NO_WINDOW)
        if r.returncode == 0:
            return "stopped"
        if r.returncode == _ESRCH:
            return "stopped (it was not loaded)"
        return f"could not stop it: launchctl bootout gui/{uid}/{LABEL}"

    def start(self, runner=None) -> str:
        """bootstrap, and then kickstart, because bootstrap starts nothing.

        `launchctl bootstrap` registers the job with launchd and exits 0
        without running it, RunAtLoad in the plist notwithstanding. Measured
        on a live machine -- see the block in install(), which had the same
        gap -- a bootstrapped job sits at "not running / runs = 0" for as
        long as you care to watch it, and one kickstart turns it into
        "running / runs = 1" with a pid.

        This is the fleet suite's restore path, called from a finally block
        on a machine someone works at. Answering "started" for a registered
        but idle job is the worst answer available here: the run reports
        success, the daemon never retakes the serial port, and the desk goes
        dark with nothing pointing at the cause. So a kickstart that fails
        is a failed start, even though the job is registered -- what the
        caller asked for is a process holding the port again.
        """
        if not os.path.exists(plist_path()):
            return "not installed"
        uid = os.getuid()
        run = runner or subprocess.run
        r = run(["launchctl", "bootstrap", f"gui/{uid}", plist_path()],
                capture_output=True, **update.ota.NO_WINDOW)
        if r.returncode != 0:
            # No job to kick, and a second failing command would only bury the
            # one line the operator needs to paste.
            return f"could not start it: launchctl bootstrap gui/{uid} {plist_path()}"
        k = run(["launchctl", "kickstart", f"gui/{uid}/{LABEL}"],
                capture_output=True, **update.ota.NO_WINDOW)
        if k.returncode == 0:
            return "started"
        return f"could not start it: launchctl kickstart gui/{uid}/{LABEL}"

    def remove(self) -> str:
        subprocess.run(["launchctl", "bootout", f"gui/{os.getuid()}/{LABEL}"],
                       capture_output=True, **update.ota.NO_WINDOW)
        _rm(plist_path())
        return "removed"

    def status(self) -> str:
        """Registered is not the same as working, and the difference is the
        whole point of this line.

        This used to answer "registered with launchd" for a job that had
        crash-looped 59 times, which is how a dead daemon went unnoticed on
        the author's own machine while every other line of `overwatch status`
        looked healthy. launchctl already knows -- it reports the run count
        and the last exit code -- so ask it.

        Parsed defensively: launchctl print is a human-readable dump and not a
        contract, so anything unrecognised falls back to the old answer rather
        than claiming a fault that may not exist.
        """
        r = subprocess.run(["launchctl", "print", f"gui/{os.getuid()}/{LABEL}"],
                           capture_output=True, text=True, **update.ota.NO_WINDOW)
        if r.returncode != 0:
            # launchctl has never heard of this label, and that is TWO states
            # sharing one sentence. A plist on disk that is merely not loaded
            # is an install that exists and needs starting; no plist at all is
            # an install that never happened. Answering "not installed" to
            # both sends someone to reinstall a service that is already there.
            #
            # It also hides the ordinary aftermath of a burn or a fleet run.
            # Both boot the agent out and are expected to put it back, and if
            # one does not, this line is where a person looks first -- so the
            # state it must name most clearly is exactly the one it was
            # collapsing away.
            #
            # stop() and start() have always checked for the plist before
            # answering. status() did not, which is why status() is the one
            # that lied. Found 2026-09-09 by booting the agent out by hand,
            # burning a board, and then asking.
            if os.path.exists(plist_path()):
                return ("installed but not loaded -- run "
                        f"`{installed_bin()} install` to start it")
            return "not installed"

        fields = {}
        for line in (r.stdout or "").splitlines():
            if "=" not in line:
                continue
            k, _, v = line.partition("=")
            k, v = k.strip(), v.strip()
            if k in ("pid", "last exit code", "runs") and k not in fields:
                fields[k] = v

        if fields.get("pid", "").isdigit():
            return f"running (launchd, pid {fields['pid']})"

        exit_code = fields.get("last exit code")
        if exit_code and exit_code.isdigit() and int(exit_code) != 0:
            runs = fields.get("runs", "?")
            return (f"registered but FAILING -- exits with code {exit_code},"
                    f" {runs} attempts so far. See {log_path()}")
        return "registered with launchd"


# The autostart Windows never refuses: the user's own Run key.
#
# HKCU is the account's own hive, so writing here needs no administrator by
# definition. That is the whole reason it is the fallback -- see
# _SchtasksBackend._install_without_a_task for what it is a fallback FROM.
RUN_KEY = r"Software\Microsoft\Windows\CurrentVersion\Run"
RUN_VALUE = TASK_NAME


def _winreg():
    """The winreg module, or None where there is no registry.

    None rather than an ImportError because the backends are selected by
    platform at run time but exercised on every platform by the tests: a bare
    `import winreg` at the top of a Windows-only helper takes the whole suite
    down on macOS.
    """
    try:
        import winreg
        return winreg
    except ImportError:
        return None


def _autostart_command() -> str:
    """The same hidden-window launcher the Scheduled Task would have run."""
    return f'wscript.exe //B //Nologo "{launcher_path()}"'


def _autostart_set() -> str:
    """Start the bridge at logon from the user's Run key. "" when it worked."""
    winreg = _winreg()
    if winreg is None:
        return "no registry on this system"
    try:
        with winreg.CreateKeyEx(winreg.HKEY_CURRENT_USER, RUN_KEY, 0,
                                winreg.KEY_SET_VALUE) as key:
            winreg.SetValueEx(key, RUN_VALUE, 0, winreg.REG_SZ,
                              _autostart_command())
        return ""
    except OSError as e:
        return str(e)[:120]


def _autostart_clear() -> None:
    """Remove it. Absent is the ordinary case -- most installs use the task."""
    winreg = _winreg()
    if winreg is None:
        return
    try:
        with winreg.OpenKey(winreg.HKEY_CURRENT_USER, RUN_KEY, 0,
                            winreg.KEY_SET_VALUE) as key:
            winreg.DeleteValue(key, RUN_VALUE)
    except OSError:
        pass


def _autostart_present() -> bool:
    winreg = _winreg()
    if winreg is None:
        return False
    try:
        with winreg.OpenKey(winreg.HKEY_CURRENT_USER, RUN_KEY) as key:
            value, _ = winreg.QueryValueEx(key, RUN_VALUE)
        return bool(value)
    except OSError:
        return False


def _start_launcher() -> None:
    """Start the bridge now, with no Scheduled Task to trigger.

    Detached and window-less, the same way _schedule_windows_cleanup starts
    its own child: this must outlive the installer that spawned it, and it
    must not put a console window on the customer's desktop.
    """
    DETACHED_NO_WINDOW = 0x00000008 | 0x08000000
    try:
        subprocess.Popen(["wscript.exe", "//B", "//Nologo", launcher_path()],
                         creationflags=DETACHED_NO_WINDOW, close_fds=True)
    except OSError:
        pass


class _SchtasksBackend(_Backend):
    def creates(self):
        return (f'a Scheduled Task named "{TASK_NAME}", and {launcher_path()}\n'
                "             the one-line script it runs, so the bridge starts\n"
                "             with no window. If Windows will not register the\n"
                "             task without administrator, an entry named\n"
                f'             "{RUN_VALUE}" under your own account\'s Run key\n'
                "             is used instead, which starts it the same way")

    def install(self) -> str:
        # The task runs the launcher, not the program: see launcher_path().
        # The bridge's output goes to bridge.log by its own hand (--log),
        # since a hidden window is nowhere for it to go.
        try:
            os.makedirs(overwatch_home(), exist_ok=True)
            with open(launcher_path(), "w", encoding="ascii", newline="\r\n") as f:
                f.write(LAUNCHER_VBS)
        except OSError as e:
            return f"could not write {launcher_path()}: {e}"
        # /f overwrites a task from an earlier install rather than failing.
        #
        # This is tried FIRST because a Scheduled Task is the better of the
        # two: it can be ended and re-run by name, which is what `overwatch
        # update` restarts through. But it is not always allowed -- see
        # _install_without_a_task, which is where a refusal goes.
        r = subprocess.run(
            ["schtasks", "/create", "/f", "/tn", TASK_NAME, "/sc", "onlogon",
             "/tr", f'wscript.exe //B //Nologo "{launcher_path()}"'],
            capture_output=True, text=True, **update.ota.NO_WINDOW)
        if r.returncode != 0:
            return self._install_without_a_task(r)
        # A daemon from an earlier install is still running, holding the
        # serial port and the single-instance lock, and /create does nothing
        # to it: on the first reinstall over a live 1.0.2 the new task's
        # daemon started, found the lock held, and left -- the old one, with
        # its window, carried on (2026-08-29). Stop it the way restart() does.
        subprocess.run(["schtasks", "/end", "/tn", TASK_NAME], capture_output=True, **update.ota.NO_WINDOW)
        _kill_recorded_daemon()
        # /sc onlogon does not start it now, only at the next logon.
        subprocess.run(["schtasks", "/run", "/tn", TASK_NAME], capture_output=True, **update.ota.NO_WINDOW)
        # And then ASK Windows, rather than assume. /run returning zero means
        # the task was triggered, not that a daemon exists -- the same claim
        # from the same kind of evidence that left a Mac with no bridge and
        # an installer saying "running (launchd)" on 2026-09-04.
        #
        # Six tries, not four: this is the first run of a freshly copied .exe,
        # and Windows may hold it while a virus scanner reads all of it.
        if _confirm_running(self._is_running):
            return "running (Scheduled Task)"
        return ("registered as a Scheduled Task, but it is not running -- "
                f'start it with: schtasks /run /tn "{TASK_NAME}"')

    def _install_without_a_task(self, refused) -> str:
        """Windows would not register the task. Start at logon the other way.

        A logon TRIGGER needs administrator. Measured on the Windows 10
        release desk (19045), 2026-09-06, from a genuinely non-elevated
        process, on a machine with stock Task Scheduler ACLs
        (`Authenticated Users:(CI)(W,Rc)`) and no policy set:

            schtasks /create /sc once     ... SUCCESS
            schtasks /create /sc onlogon  ... ERROR: Access is denied.
            schtasks /create /sc onlogon /ru <user> ... Access is denied.

        The comment that used to sit above the /create call said "/sc onlogon
        needs no admin rights; a Windows service would". The first half was
        wrong, and believing it was expensive because the failure was silent
        and complete: install printed one line about a task it had not
        registered, `overwatch status` said "Bridge not installed", no daemon
        ever ran, and the panel sat on its standalone setup screen -- with
        the board plugged in, driver installed and working. A customer
        reported exactly that.

        HKCU\\...\\Run is the account's own key, so no administrator is
        involved, and it is what user-level programs have always started
        from. It is the poorer mechanism -- there is no name to /end or /run,
        so restart() has to start the launcher itself -- which is why it is
        second rather than first.
        """
        _autostart_clear()
        err = _autostart_set()
        if err:
            why = (refused.stderr or "").strip()[:60]
            return (f"could not register a Scheduled Task ({why}), and could"
                    f" not set it to start at logon either: {err}")
        # Same reasoning as the task path: a daemon from an earlier install
        # still holds the serial port and the single-instance lock, and
        # nothing above has stopped it.
        _kill_recorded_daemon()
        _start_launcher()
        if _confirm_running(self._is_running):
            return "running (starts when you log in)"
        return ("set to start when you log in, but it is not running yet -- "
                f"see {log_path()}")

    def _is_running(self) -> bool:
        """Is the bridge daemon alive? Asked of Windows, by pid.

        NOT `schtasks /query`. The task's status answers a different question:
        its action is wscript running LAUNCHER_VBS, which starts the bridge
        with `, 0, False` -- do not wait -- and exits at once. A perfectly
        healthy Overwatch therefore shows the task as Ready within a second of
        /run, so a check on the task's state would have called every working
        install dead. Registration is not health, and neither is the
        launcher's own exit.

        Nor could it be read from the word schtasks prints: that word is
        translated on a localised Windows, and the owner's PC is one.

        So the question is the one _kill_recorded_daemon already asks -- the
        pid the daemon wrote for itself -- with the image name as a filter so
        a recycled pid belonging to something else cannot answer for it. Only
        ~/.overwatch/bridge.pid is read, not the pre-1.1.0 copies that function
        also sweeps: a daemon still running out of bin.old is the thing an
        install was trying to replace, and counting it as health would report
        exactly the failure of 2026-08-29 as a success.
        """
        try:
            with open(pid_path(), encoding="utf-8") as f:
                pid = int(f.read().strip())
        except (OSError, ValueError):
            return False
        r = subprocess.run(
            ["tasklist", "/fi", f"PID eq {pid}",
             "/fi", "IMAGENAME eq " + os.path.basename(installed_bin()),
             "/nh", "/fo", "csv"],
            capture_output=True, text=True, **update.ota.NO_WINDOW)
        # tasklist exits ZERO whether or not anything matched; with no match
        # it prints "INFO: No tasks are running which match ...". The pid
        # appearing in a row it printed is the only answer that means
        # anything -- and that row is digits either way, in any language.
        return str(pid) in (r.stdout or "")

    def restart(self) -> str:
        subprocess.run(["schtasks", "/end", "/tn", TASK_NAME],
                       capture_output=True, **update.ota.NO_WINDOW)
        # /end only reaches the instance the TASK launched. A daemon that
        # replaced itself started its successor detached (see
        # update.restart_from_daemon), and that one is not the task's -- so
        # without this, /run below would add a second daemon competing for the
        # same serial port.
        _kill_recorded_daemon()
        r = subprocess.run(["schtasks", "/run", "/tn", TASK_NAME],
                           capture_output=True, **update.ota.NO_WINDOW)
        if r.returncode != 0:
            # No task to trigger. If this install starts from the Run key
            # instead, there is nothing wrong -- start the launcher directly,
            # which is what that key would have done at the next logon.
            # Without this, `overwatch update` on such an install replaces the
            # binary and then leaves nothing running.
            if not _autostart_present():
                return "could not restart it"
            _start_launcher()
        if _confirm_running(self._is_running):
            return "restarted"
        # This is the `overwatch update` path: the .exe under the task was just
        # replaced. If the new one cannot start, /run still succeeds and the
        # log is the only thing that says why -- and unlike install() there is
        # no command worth pasting, because the command that would be printed
        # is the one that just ran and left nothing running.
        return ("restarted, but it is not running -- "
                f"see {log_path()}")

    def halt(self) -> None:
        """Let go of bin\\overwatch.exe so the update swap can rename the directory.

        Windows is the one platform where halting is not the same as stopping
        a supervised service: it is the one that refuses to rename a directory
        while a process holds a file open inside it. stop() already frees
        exactly what needs freeing here -- /end for the instance the task
        launched, and the recorded pid for a daemon that started its own
        successor detached -- and leaves the task and the Run key alone, which
        is the property that matters: a halt that unregistered the service
        would turn a failed update into a machine that never starts Overwatch
        again.

        The answer is discarded on purpose. There is nothing a caller in the
        middle of an update can do with "not installed", and update._replace()
        waits for the handle regardless of whether this took.
        """
        self.stop()

    def _registered(self, runner=None) -> bool:
        r = (runner or subprocess.run)(["schtasks", "/query", "/tn", TASK_NAME],
                                       capture_output=True, **update.ota.NO_WINDOW)
        return r.returncode == 0

    def stop(self, runner=None) -> str:
        """/end, and then the daemon /end cannot reach.

        Same trap as restart(): /end stops the instance the TASK launched,
        while a daemon that replaced itself started its successor detached
        (see update.restart_from_daemon). That successor keeps the serial
        port, and a second process asking for the same COM port is refused
        with "Access is denied" -- which looks exactly like a board fault. So
        the kill happens even when there is no task registered at all: the
        port is the thing being freed here, not the task, and an unregistered
        task with a live detached daemon says so rather than reporting the
        bare "not installed" that would deny the port was ever held.
        """
        run = runner or subprocess.run
        registered = self._registered(run)
        r = None
        if registered:
            r = run(["schtasks", "/end", "/tn", TASK_NAME],
                    capture_output=True, **update.ota.NO_WINDOW)
        killed = _kill_recorded_daemon(runner=run)
        if not registered:
            return ("not installed; killed a detached daemon" if killed
                    else "not installed")
        if r.returncode == 0:
            return "stopped"
        return f'could not stop it: schtasks /end /tn "{TASK_NAME}"'

    def start(self, runner=None) -> str:
        run = runner or subprocess.run
        if not self._registered(run):
            return "not installed"
        r = run(["schtasks", "/run", "/tn", TASK_NAME],
                capture_output=True, **update.ota.NO_WINDOW)
        if r.returncode == 0:
            return "started"
        return f'could not start it: schtasks /run /tn "{TASK_NAME}"'

    def remove(self) -> str:
        subprocess.run(["schtasks", "/end", "/tn", TASK_NAME], capture_output=True, **update.ota.NO_WINDOW)
        subprocess.run(["schtasks", "/delete", "/f", "/tn", TASK_NAME],
                       capture_output=True, **update.ota.NO_WINDOW)
        # Unconditionally, and without asking first: an install may have used
        # either mechanism, uninstall does not know which, and a leftover Run
        # entry would try to start a program that is about to be deleted on
        # every logon for the rest of the machine's life.
        _autostart_clear()
        _kill_recorded_daemon()
        _kill_by_path()
        return "removed"

    def status(self) -> str:
        r = subprocess.run(["schtasks", "/query", "/tn", TASK_NAME],
                           capture_output=True, **update.ota.NO_WINDOW)
        if r.returncode == 0:
            return "registered as a Scheduled Task"
        # Not "not installed" until BOTH have been asked. Reporting the
        # absence of the task as the absence of the bridge is what made this
        # failure look like a missing install rather than a working one.
        if _autostart_present():
            return "registered to start when you log in"
        return "not installed"


class _SystemdBackend(_Backend):
    """Linux, where the supervisor may simply not be there.

    systemd is overwhelmingly the default but it is not guaranteed, and a
    machine without it is not a broken machine -- so every method below has
    a real answer for that case rather than an error.
    """

    @staticmethod
    def _has_systemctl() -> bool:
        return bool(shutil.which("systemctl"))

    def creates(self):
        return unit_path()

    def install(self) -> str:
        # The unit file is written either way. It costs nothing, and it means
        # a machine that gains systemd later already has the right file.
        os.makedirs(os.path.dirname(unit_path()), exist_ok=True)
        with open(unit_path(), "w", encoding="utf-8") as f:
            f.write(_UNIT_TEMPLATE.format(command=_systemd_exec()))
        if not self._has_systemctl():
            return f"no systemd here; run it yourself: {installed_bin()} run"
        subprocess.run(["systemctl", "--user", "daemon-reload"], capture_output=True, **update.ota.NO_WINDOW)
        r = subprocess.run(["systemctl", "--user", "enable", "--now",
                            "overwatch-bridge.service"], capture_output=True, **update.ota.NO_WINDOW)
        if r.returncode != 0:
            return "installed, but could not be started: systemctl --user enable --now overwatch-bridge"
        # `enable --now` RETURNED ZERO. That is systemctl accepting the
        # request; it is not a running unit, and this line has already been
        # wrong once in a way nobody caught: see _systemd_exec(), where an
        # unquoted ExecStart with a space in it failed to locate the
        # executable "while `overwatch install` still printed running (systemd)".
        # Ask systemd instead.
        if _confirm_running(self._is_running):
            return "running (systemd)"
        return ("enabled with systemd, but it is not running -- "
                "see: systemctl --user status overwatch-bridge.service")

    def _is_running(self) -> bool:
        """Does systemd say the unit is active? Its word, not an exit code.

        `is-active` WITHOUT --quiet prints the state -- active, activating,
        inactive, failed -- and that word is the answer. status() may use the
        exit code because there the command asked and the fact reported are
        the same thing; here the temptation is to reuse the exit code of
        `enable --now`, which is a different command reporting a different
        fact, and that is precisely the defect.

        Anything unrecognised reads as not running: an empty dump means we
        could not see it, and not-seen must never print as healthy.

        Worth the retry even though Restart=always makes systemd patient: a
        unit that has been asked to start reads "activating" until its exec
        is up, and answering the first ask would call that dead.
        """
        r = subprocess.run(["systemctl", "--user", "is-active",
                            "overwatch-bridge.service"],
                           capture_output=True, text=True,
                           **update.ota.NO_WINDOW)
        lines = (r.stdout or "").split()
        return bool(lines) and lines[0] == "active"

    def restart(self) -> str:
        if not self._has_systemctl():
            return super().restart()
        r = subprocess.run(["systemctl", "--user", "restart",
                            "overwatch-bridge.service"], capture_output=True, **update.ota.NO_WINDOW)
        if r.returncode != 0:
            return "could not restart it"
        if _confirm_running(self._is_running):
            return "restarted"
        return ("restarted, but systemd reports it is not running -- "
                "see: systemctl --user status overwatch-bridge.service")

    def stop(self, runner=None) -> str:
        if not self._has_systemctl():
            return super().stop(runner)
        if not os.path.exists(unit_path()):
            return "not installed"
        r = (runner or subprocess.run)(
            ["systemctl", "--user", "stop", "overwatch-bridge.service"],
            capture_output=True, **update.ota.NO_WINDOW)
        # An explicit stop is not undone by Restart=always, so unlike launchd
        # this needs nothing stronger than the obvious command.
        if r.returncode == 0:
            return "stopped"
        return "could not stop it: systemctl --user stop overwatch-bridge.service"

    def start(self, runner=None) -> str:
        if not self._has_systemctl():
            return super().start(runner)
        if not os.path.exists(unit_path()):
            return "not installed"
        r = (runner or subprocess.run)(
            ["systemctl", "--user", "start", "overwatch-bridge.service"],
            capture_output=True, **update.ota.NO_WINDOW)
        if r.returncode == 0:
            return "started"
        return "could not start it: systemctl --user start overwatch-bridge.service"

    def remove(self) -> str:
        if not self._has_systemctl():
            # Install said "no systemd here; run it yourself", so whatever is
            # running was started by hand and nothing here can stop it. Saying
            # "removed" would be followed a line later by "Nothing of Overwatch's
            # is left running", which would not be true.
            _rm(unit_path())
            return "no systemd here; stop it yourself if you started it"
        subprocess.run(["systemctl", "--user", "disable", "--now",
                        "overwatch-bridge.service"], capture_output=True, **update.ota.NO_WINDOW)
        _rm(unit_path())
        subprocess.run(["systemctl", "--user", "daemon-reload"],
                       capture_output=True, **update.ota.NO_WINDOW)
        return "removed"

    def status(self) -> str:
        if not self._has_systemctl():
            # Was "unknown on linux", which is the drift described on
            # _Backend: remove() knew exactly what this machine's situation
            # was and status() claimed not to.
            return "no systemd here; not something this can check"
        r = subprocess.run(["systemctl", "--user", "is-active", "--quiet",
                            "overwatch-bridge.service"], capture_output=True, **update.ota.NO_WINDOW)
        return "running" if r.returncode == 0 else "not running"


def backend() -> _Backend:
    """The login-service backend for this machine.

    Built fresh each call rather than cached at import: every path it uses is
    resolved from HOME at call time (see the note above overwatch_home), and the
    tests move HOME between calls.
    """
    if sys.platform == "darwin":
        return _LaunchdBackend()
    if sys.platform == "win32":
        return _SchtasksBackend()
    if sys.platform.startswith("linux"):
        return _SystemdBackend()
    return _Backend()


def _install_service() -> str:
    if _skip_service():
        return "skipped (OVERWATCH_SKIP_SERVICE=1)"
    return backend().install()


def restart_service() -> str:
    """Bounce the login service so it comes up on a freshly replaced binary.

    Not the same as exiting and letting the supervisor notice: this is called
    from `overwatch update`, which is a separate process from the daemon. The
    daemon's own path is simpler -- on macOS and Linux it exits and KeepAlive /
    Restart=always bring it back. Windows has neither: a Scheduled Task with an
    onlogon trigger does not restart anything, so it is told explicitly.
    """
    if _skip_service():
        return "skipped (OVERWATCH_SKIP_SERVICE=1)"
    return backend().restart()


# The exact word every backend returns when the service is back up, and
# nothing else. Compared with == and not with startswith(), which is not
# fussiness: three of the four backends report failure as "restarted, but
# launchd reports it is not running -- see ...", and a prefix test reads that
# as success. `4ba9c7d fix: Linux and Windows claimed a running service from
# an exit code` was this same mistake one layer down.
_RESTART_OK = "restarted"

# Nothing was attempted, so there is nothing here to call broken: a test
# harness with OVERWATCH_SKIP_SERVICE=1, and a platform with no supervisor to
# bounce (a developer running out of a checkout).
_RESTART_NOT_ATTEMPTED = ("skipped (", "not running under a supervisor")


def restart_left_it_down(detail: str) -> bool:
    """Did the bounce end with no daemon running?

    `overwatch update` printed the backend's answer and returned 0 regardless, so
    a service that did not come back was one line in the middle of a
    successful-looking update. The board then sits on "Link the PC daemon"
    forever with nothing on the computer saying why -- which is exactly what
    a customer hit upgrading 1.2.5 -> 1.3.2 on 2026-09-09. Their 1.2.5
    updater could not tell (every check in restart() landed in 1.3.0 and
    1.3.2, after the version doing the upgrading); this one can, and the
    point of saying so is that `overwatch install` fixes it in one command.
    """
    if detail == _RESTART_OK:
        return False
    return not detail.startswith(_RESTART_NOT_ATTEMPTED)


def _refresh_shims() -> None:
    """Put THIS version's shims on disk, as part of an update.

    `overwatch update` replaces the program and nothing else, and both shims ship
    inside it: after a swap, ~/.overwatch/overwatch-hook.sh is still the copy the
    previous release wrote out. The daemon's DriftWatchdog repairs that
    within five minutes -- but only while a daemon is running, and a daemon
    that did not come back is precisely the case this matters in. Two file
    writes here remove the dependency instead of relying on the half that may
    be down to fix the other half.

    Only shims that are ALREADY there are rewritten. A path that does not
    exist belongs to an install that never happened or was undone, and
    `update` is not the command that sets one up.

    Best effort: an update whose program swap has already succeeded must not
    report failure because a shim could not be rewritten. The watchdog still
    sits behind this.
    """
    for path, name in ((shim_path(), "overwatch-statusline.sh"),
                       (hook_shim_path(), "overwatch-hook.sh")):
        if not os.path.exists(path):
            continue
        try:
            _write_shim(path, name)
        except OSError as e:
            print(f"  could not refresh {os.path.basename(path)}: {e}")


def halt_service() -> None:
    """Stop the daemon before replacing the program underneath it.

    Best effort and silent: on the platforms where it does nothing this is
    correct, and on the one where it matters the retry in update._replace()
    still covers a stop that did not take. Nothing here is worth a line of
    output in the middle of an update.
    """
    if _skip_service():
        return
    try:
        backend().halt()
    except Exception:
        pass


def _say_bye():
    """Tell the board the app is leaving for good, so it shows \"connecting\"
    rather than dozing off (firmware 1.2.0 and later). Best effort: the port
    the daemon last used, opened plainly (no DTR/RTS preset -- that would
    reset the board), one line, gone. Any failure is silent; the board falls
    back to what it always did."""
    try:
        import json
        import serial
        from pc import protocol
        with open(os.path.join(overwatch_home(), "board.json"), encoding="utf-8") as f:
            port = json.load(f).get("port")
        if not port:
            return
        with serial.Serial(port, 115200, timeout=0.2, write_timeout=1) as s:
            s.write((json.dumps(protocol.bye(), separators=(",", ":")) + "\n").encode())
            s.flush()
    except Exception:
        pass


def _remove_service() -> str:
    if _skip_service():
        return "skipped (OVERWATCH_SKIP_SERVICE=1)"
    return backend().remove()


# One definition, in pc/update.py. This module already imports it.
_rm = update._rm


def _kill_recorded_daemon(runner=None) -> int:
    """Stop the bridge by the pid it wrote for itself, not by its name.

    Returns how many pids it signalled, which stop() reports: on a machine
    with no Scheduled Task registered, a daemon killed here is the difference
    between a freed serial port and one still held.

    Ending the Scheduled Task ends the process the task launched. PyInstaller's
    onefile bootloader re-executes the same .exe as a child, and that child
    keeps running the bridge loop and keeps overwatch.exe open, which is enough for
    Windows to refuse every attempt to delete it -- including the detached
    rmdir scheduled for after we exit.

    By pid, with the image name only as a FILTER: `taskkill /im overwatch.exe`
    matches the uninstaller too, and killing ourselves mid-uninstall is exactly
    what the previous attempt did. /t takes the bootloader's child with it.
    """
    if sys.platform != "win32":
        return 0
    killed = 0
    # Every place a daemon may have left its pid: ~/.overwatch since 1.1.0, and
    # beside the program before that -- which, after 1.1.0's install has
    # rotated the directory, means bin.old. The first 1.0.4 -> 1.1.0
    # install on a real PC left the old daemon running with the serial port
    # because only the new location was read (2026-08-29).
    for path in (pid_path(),
                 os.path.join(bin_dir(), "bridge.pid"),
                 os.path.join(bin_dir() + ".old", "bridge.pid")):
        try:
            with open(path, encoding="utf-8") as f:
                pid = int(f.read().strip())
        except (OSError, ValueError):
            continue
        if pid == os.getpid():
            continue              # somehow ours; nothing to stop
        # runner, so _Backend.stop() can be handed one and have every command
        # it causes go the same way. None is subprocess.run, resolved here
        # rather than as a default argument so the existing callers -- and the
        # tests that stub subprocess.run for them -- are unaffected.
        (runner or subprocess.run)(
            ["taskkill", "/f", "/t", "/pid", str(pid),
             "/fi", "IMAGENAME eq " + os.path.basename(installed_bin())],
            capture_output=True, **update.ota.NO_WINDOW)
        killed += 1
    return killed


def _kill_by_path():
    """Last resort: anything running the exact binary we are deleting.

    The pid file is the good path and this is what happens when it is missing
    -- an install from before it existed, a daemon killed before it could write
    one, a profile that moved. Matched on the full executable PATH and not on
    the image name, so the uninstaller (same name, different file, or the very
    same file) is never in scope, and our own pid is excluded outright.
    """
    if sys.platform != "win32":
        return
    target = installed_bin().replace("'", "''")     # PowerShell string escape
    script = (
        "Get-CimInstance Win32_Process | "
        f"Where-Object {{ $_.ExecutablePath -eq '{target}' "
        f"-and $_.ProcessId -ne {os.getpid()} }} | "
        "ForEach-Object { Stop-Process -Id $_.ProcessId -Force }"
    )
    subprocess.run(["powershell", "-NoProfile", "-NonInteractive",
                    "-Command", script], capture_output=True, **update.ota.NO_WINDOW)


def _remove_bin_dir(attempts=6):
    """Delete ~/.overwatch/bin. Returns (done, message).

    Straightforward everywhere but Windows, which will not delete a running
    executable -- and here the executable is usually this one. The undo hint we
    print says `~/.overwatch/bin/overwatch.exe uninstall`, so a customer following it
    is asking a program to delete the file it is running from. The daemon can
    be holding the same file too: `schtasks /end` returns before the process
    has actually exited.

    So: try, wait, try again, and if Windows still says no, hand the job to
    something that will outlive us.

    This used to end with `taskkill /f /im overwatch.exe`, which is worse than the
    problem it was for -- the uninstaller has that image name, so it killed
    itself, mid-uninstall, having already removed the Scheduled Task and the
    status line. Every Windows scenario in CI exited non-zero with no output at
    all, which is exactly what being terminated looks like.
    """
    for attempt in range(attempts):
        for d in (bin_dir(), bin_dir() + ".old", bin_dir() + ".new"):
            shutil.rmtree(d, ignore_errors=True)
        if not any(os.path.exists(d) for d in
                   (bin_dir(), bin_dir() + ".old", bin_dir() + ".new")):
            return True, "removed"
        time.sleep(0.4 * (attempt + 1))
    if sys.platform == "win32":
        return _schedule_windows_cleanup()
    return False, "could not be removed -- something is still running from it"


def _schedule_windows_cleanup():
    """Let Windows delete the directory once nothing is running inside it.

    A detached cmd that waits a few seconds and then removes the tree. By the
    time it fires, this process has exited and released its own hold, and the
    service stopped a moment ago has finished going away.

    `ping -n 4 127.0.0.1` rather than `timeout /t`, which wants a console and
    fails outright in a detached process that has no window.
    """
    script = "ping -n 4 127.0.0.1 >nul" + "".join(
        f' & rmdir /s /q "{d}"' for d in (bin_dir(), bin_dir() + ".old",
                                          bin_dir() + ".new"))
    DETACHED_NO_WINDOW = 0x00000008 | 0x08000000
    try:
        subprocess.Popen(["cmd", "/c", script],
                         creationflags=DETACHED_NO_WINDOW, close_fds=True)
    except Exception as e:
        return False, f"could not be removed ({e})"
    return True, "will be gone a moment after this window closes"


# -------------------------------------------------------------------- install


def _announce():
    """Say what is about to change, before changing it.

    Install is deliberately unattended -- it asks nothing, because plugging the
    board in is meant to be the whole setup. That makes disclosure the only
    thing standing between us and silently editing a file the customer owns,
    so it is not optional and it runs before the first write.
    """
    print("Overwatch setup. Here is everything it is about to do, before it does any of it.")
    print()
    print(f"  Creates    {installed_bin()}")
    print("             a copy of this program and its support files, so the")
    print("             folder you downloaded can be deleted when this finishes.")
    print(f"  Creates    {shim_path()}")
    print("             the small script Claude Code runs to hand over the")
    print("             usage figures. It keeps the last status line payload")
    print("             Claude Code sent, which also names the session, the")
    print("             working directory and the transcript file. Only the")
    print("             usage figures are read out of it, and nothing in it")
    print("             leaves this machine. It is readable by you alone.")
    print(f"  Creates    {hook_shim_path()}")
    print("             a second small script, run when Claude Code starts and")
    print("             finishes work, so the panel can show whether it is busy.")
    print("             It records the event name, the time, and the session and")
    print("             agent ids Claude Code generates -- used to tell concurrent")
    print("             sessions apart, and for nothing else. No prompt, no tool")
    print("             arguments, no file paths, no message text.")
    print(f"  Creates    {os.path.join(overwatch_home(), 'state')}")
    print("             one small file per open session, deleted when it ends.")
    print(f"  Changes    {settings_path()}")
    # This list has to stay exactly true. Install asks nothing, so the
    # disclosure is the only thing standing between us and silently editing a
    # file the customer owns -- and it said "statusLine.command, and nothing
    # else in the file" for one release after the hooks key started being
    # written too. A disclosure that is merely mostly right is worse than none,
    # because it is the thing people rely on instead of reading the diff.
    # Counted, not spelled. This said "six" while the code wrote ten: the
    # number drifted when StopFailure, SubagentStart and SubagentStop were
    # added, and nothing failed. The comment above says this list has to stay
    # exactly true because it is the thing people rely on instead of reading
    # the diff -- so it now reads itself off the list it describes, and a test
    # pins the two together.
    print("             two keys: statusLine.command, and an entry under hooks")
    print(f"             for each of {len(install_hooks.HOOK_EVENTS)} Claude Code"
          " events. Nothing else in")
    print("             the file is touched, and your own hooks are left in place.")
    prev_cmd = install_statusline._current_command(
        install_statusline._load(settings_path()))
    if prev_cmd:
        print(f"             Your current status line is kept and still runs:")
        print(f"               {prev_cmd}")
    created = backend().creates()
    if created:
        print(f"  Creates    {created}")
        print("             so the bridge starts when you log in.")
    print()
    print("  It reads no credential and no token, and sends nothing anywhere.")
    print("  The usage figures come from Claude Code, Claude Desktop's usage")
    print("  cache, or the Codex session log -- each of which has already")
    print("  worked them out. From the Codex log it keeps only the rate-limit")
    print("  line, never the conversation.")
    print()
    print(f"  To undo all of it:  {installed_bin()} uninstall")
    print()


def _install_steps() -> int:
    """How many numbered steps `overwatch install` prints on this platform.

    Five everywhere, plus one platform extra: Windows needs the USB driver,
    macOS needs the Automation grant. Both are 6 and they are NOT the same
    step, which is why callers ask sys.platform rather than comparing this
    number -- that shortcut worked only while Windows was the sole platform
    with an extra, and would have run the driver step on Macs.
    """
    return 5 + (1 if sys.platform in ("win32", "darwin") else 0)


def _stepper(total):
    """A closure that prints "[n/total] Label ... " and counts for you.

    The count used to be written into each string by hand, which was fine
    while every platform had the same five. It stopped being fine the moment
    Windows earned a sixth: five literals would each have needed a
    conditional, and the failure mode of getting one wrong is an installer
    that counts to 5 and then prints step 6 of 5.
    """
    state = {"n": 0}

    def step(label):
        state["n"] += 1
        print(f"[{state['n']}/{total}] {label} ... ", end="", flush=True)

    return step


def _install_driver_step() -> str:
    """The USB-driver line of `overwatch install`. Windows only.

    Staging the driver here, rather than waiting for a customer to plug the
    board in and hit the yellow triangle, is the whole point: `pnputil
    /add-driver /install` puts it in Windows' driver store, and a board
    plugged in afterwards binds to it silently. Plug and play, once.

    It is also the one step that can raise a Windows permission prompt, and
    it only does so when there is genuinely something to install -- see
    win_driver.ensure_driver. Under OVERWATCH_SKIP_SERVICE this is skipped
    entirely, for the same reason the login service is: the fleet test suite
    runs `install` for real on the Windows desk, and a modal permission
    prompt on a machine nobody is sitting at hangs the run until it times out.
    """
    if _skip_service():
        return "not checked (OVERWATCH_SKIP_SERVICE=1)"
    try:
        _, line = win_driver.ensure_driver()
        return line
    except Exception as e:
        # The board is the product, but a driver that would not install is
        # not a reason to abandon an install that has otherwise worked --
        # the customer can still run `overwatch driver` afterwards.
        return f"skipped ({e})"


def cmd_driver(_args) -> int:
    """`overwatch driver` -- install the USB driver, and say what happened.

    Exists as its own command for two audiences: a customer being walked
    through a support conversation ("run overwatch driver"), and anyone whose
    install ran before this version, or who declined the permission prompt
    the first time.
    """
    if sys.platform != "win32":
        print("The board's USB-serial chip needs no driver on this system --")
        print("macOS and Linux both carry one in the kernel.")
        return 0

    undriven = win_driver.undriven_boards()
    if undriven:
        print(win_driver.as_sentence(win_driver.summary(undriven)) + ".")
    print("USB driver ... ", end="", flush=True)
    # Forced only when a board is sitting there undriven. Being told "already
    # installed" is the correct answer on a healthy machine, and the wrong
    # one for somebody looking at a yellow triangle: whatever the store
    # holds, it is evidently not reaching their board, so install it again.
    status, line = win_driver.ensure_driver(force=bool(undriven))
    print(line)

    still = win_driver.undriven_boards()
    if not still:
        if undriven:
            print()
            print("The board is set up. Check it with:")
            print(f"  {installed_bin()} status")
        return 0

    # Installed, or claimed to be, and Windows still will not use the device.
    # Repeating "run overwatch driver" here would be a loop, so this is where the
    # advice stops being something this program can do for them.
    print()
    print(f"Windows still cannot use the board: {win_driver.summary(still)}.")
    if status in ("installed", "ok"):
        print("  Unplug the board, plug it back in, and run this again.")
        print("  If it stays, the machine may need a restart.")
    else:
        print(f"  Install the driver by hand from {win_driver.DRIVER_PAGE}")
    return 1


def cmd_install(_args) -> int:
    # Before anything is written, and before the disclosure: if the file we are
    # about to edit does not parse, the honest move is to change nothing at all
    # and say why. The alternative -- treating it as empty -- writes a fresh
    # settings.json over whatever the customer was halfway through editing.
    try:
        install_statusline._load(settings_path())
    except install_statusline.SettingsUnreadable as e:
        print(f"Overwatch setup stopped. {e}")
        print()
        print("Nothing was changed. Fix the file, or move it aside, and run")
        print("this again.")
        return 1

    _announce()

    # Windows gets one extra step -- the USB driver -- and the numbering has
    # to agree with it, so it is counted rather than written out. macOS and
    # Linux drive the CH340 out of the kernel and would only be reading a
    # line that said "not needed on this system".
    steps = _install_steps()
    step = _stepper(steps)

    step("Program")
    os.makedirs(bin_dir(), exist_ok=True)
    if _frozen():
        # The program is a directory -- the executable and its _internal/
        # support files -- so it is staged whole and rotated in with the
        # same swap the updater uses: <bin>.new is copied, self-tested, and
        # then renamed over <bin> while the previous one goes to <bin>.old.
        # That is what makes re-running the installer over a live install
        # work on every platform: a running program can be renamed but not
        # overwritten, and its directory likewise. Not when it IS the
        # installed copy: a re-run from ~/.overwatch/bin has nothing to copy.
        src = os.path.dirname(_self_path())
        if os.path.abspath(src) != os.path.abspath(bin_dir()):
            staged = bin_dir() + ".new"
            shutil.rmtree(staged, ignore_errors=True)
            shutil.copytree(src, staged, symlinks=True)
            # Re-running the installer over a live install hits the same
            # Windows rename refusal that `overwatch update` did; the service is
            # (re)installed and started further down either way.
            halt_service()
            ok, message = update.swap_in(staged, installed_bin(),
                                         RELEASE_VERSION)
            if not ok:
                print(message)
                print()
                print("Nothing else was changed.")
                return 1
        print(installed_bin())
    else:
        # From a checkout there is nothing to copy; the service points at this
        # interpreter instead. Customers never take this path.
        print("running from a checkout, nothing to copy")

    step("Status line")
    os.makedirs(overwatch_home(), exist_ok=True)
    # Private to the user. The shims write the status line payload -- which
    # names the working directory and the session -- and the per-session
    # state files in here. Both shims create with umask 077, but a directory
    # from an earlier install was made at the default umask, so this
    # tightens it once rather than leaving it to the next mkdir.
    for d in (overwatch_home(), os.path.join(overwatch_home(), "state")):
        try:
            os.chmod(d, 0o700)
        except OSError:
            pass          # absent (state/ appears on the first hook), or Windows
    _write_shim(shim_path(), "overwatch-statusline.sh")
    install_statusline._announce(settings_path(), shim_path(),
                                 undo_hint=f"{installed_bin()} uninstall")
    print("      " + install_statusline.install(settings_path(), shim_path()))

    step("Activity hooks")
    _write_shim(hook_shim_path(), "overwatch-hook.sh")
    try:
        print(install_hooks.install(settings_path(), hook_shim_path()))
    except install_statusline.SettingsUnreadable as e:
        # The status line is the product; the activity light is a nicety. A
        # hooks section we cannot safely edit costs the user a pulsing dot,
        # and is not worth failing an install that has otherwise worked.
        print(f"skipped ({e})")

    # The disclosure for this step is here rather than up in _announce(),
    # because it is the only step that is conditional on what is already on
    # the machine: on a Codex-free machine there is nothing to disclose, and a
    # paragraph about another vendor's config file would be noise at best and
    # alarming at worst.
    step("Codex hooks")
    if codex_present():
        print()
        _announce_codex_hooks()
        print("      " + _install_codex_hooks())
    else:
        print(_install_codex_hooks())

    if sys.platform == "win32":
        step("USB driver")
        print(_install_driver_step())

    if sys.platform == "darwin":
        # Before the service, deliberately. From here on the daemon runs at
        # login with nobody watching, and macOS shows the Automation prompt
        # once to whoever is there. Asking now is the difference between one
        # click and a launcher that is quietly half-broken forever.
        step("Automation")
        print()
        macperm.preflight()

    step("Background service")
    print(_install_service())

    print()
    print("Done. Plug the board in over USB -- it picks it up on its own.")
    print()
    # The page FIRST, and by URL rather than by subcommand.
    #
    # This block used to offer three terminal commands and nothing else, to a
    # person whose next move is to plug in a board and set up six launcher
    # tiles. Somebody who was handed a kit has no reason to want a fourth
    # terminal command; they want a window. The page is served for as long as
    # the daemon runs -- see the note at its start in claude_usage_bridge --
    # so this link works from here on, board or no board.
    from pc import webconfig
    print(f"  Set it up:  {webconfig.URL}")
    print("              the launcher's tiles, and whether the board is seen")
    print()
    print(f"  Log:     {log_hint()}")
    print(f"  Check:   {installed_bin()} status")
    print(f"  Undo:    {installed_bin()} uninstall")
    print()
    print("  You can delete the folder you downloaded.")
    # Absent first: it is a bigger fact than out-of-date, and the two are
    # mutually exclusive (claude_version() gives no version for an absent
    # install, which is exactly what _warn_if_claude_too_old returns on).
    _note_if_no_claude_code()
    _warn_if_claude_too_old()
    return 0


def cmd_uninstall(_args) -> int:
    print("Overwatch uninstall.")
    print()
    print("[1/5] Background service ... ", end="", flush=True)
    print(_remove_service())
    _say_bye()

    print("[2/5] Claude Code setting:")
    try:
        print("      " + install_statusline.uninstall(settings_path(), shim_path()))
    except install_statusline.SettingsUnreadable as e:
        # Keep going. The login service is already gone by this point, so
        # stopping here would leave the machine half-undone -- and the one
        # thing we must not do is "repair" the file by writing a fresh one
        # over whatever the customer was in the middle of editing.
        print(f"      Left alone: {e}")
        print("      Remove the statusLine.command line by hand once it parses.")

    print("[3/5] Activity hooks:")
    try:
        print("      " + install_hooks.uninstall(settings_path(),
                                                 hook_shim_path()))
    except install_statusline.SettingsUnreadable as e:
        # Same reasoning as the step above: keep going, and never "repair" a
        # file we cannot parse by writing a fresh one over it.
        print(f"      Left alone: {e}")

    print("[4/5] Codex hooks:")
    _uninstall_codex_hooks()

    print("[5/5] Files ... ", end="", flush=True)
    # Only what install created. NOT ~/.overwatch itself: it also holds the two
    # signing keys, which cannot be regenerated -- every board flashed with the
    # first one's public half, and every app carrying the second one's, would
    # stop accepting updates.
    for p in (shim_path(), hook_shim_path(), launcher_path(),
              os.path.join(overwatch_home(), "statusline.json"),
              os.path.join(overwatch_home(), "statusline.json.tmp"),
              # Pid-scoped temp names, from a render interrupted mid-write.
              *glob.glob(os.path.join(overwatch_home(), "statusline.json.*.tmp")),
              os.path.join(overwatch_home(), "state.json"),
              os.path.join(overwatch_home(), "state.json.tmp"),
              os.path.join(overwatch_home(), "pending_fw.json")):
        _rm(p)
    # The per-session state directory, and everything under it. state.json
    # above is the single-slot file this replaced; it is still on the list so
    # an install that predates the directory leaves nothing behind.
    _rm_state_dir()
    done, message = _remove_bin_dir()
    print(message)
    print()
    if done:
        print("Done. Nothing of Overwatch's is left running.")
        return 0
    print("Everything else is undone, but that file is still there. Log out and")
    print("back in, then delete it by hand:")
    print(f"  {bin_dir()}")
    return 1


def _uninstall_codex_hooks() -> None:
    """Take the Codex registration back out, and say what is deliberately kept.

    Prints rather than returning, because it has two things to say, and never
    stops on a bad file: the caller has already removed the login service by
    the time this runs, so stopping here would leave the machine half-undone.
    The one thing we must not do is "repair" a file we cannot parse by writing
    a fresh one over it.

    The trust record in Codex's own config.toml is left alone, and the second
    half of this function exists to say so out loud. Removing it is the
    tidier-looking choice and it is the wrong one: under `codex exec` a
    distrusted hook is skipped silently, with no prompt and no output, so a
    reinstall on a headless machine would produce a hook that is installed,
    correct, registered and permanently invisible. Working software that
    cannot be seen to be broken is the worst failure shape this product has.
    The full argument is in docs/research/codex-hook-contract.md under "RULING:
    uninstall leaves the trust record alone"; silence about it here would be
    the same defect one level up -- a decision the user cannot see.
    """
    # No try around this, unlike the status line and activity hook steps of
    # cmd_install (numbered there, so not named by number here at all --
    # Windows has a sixth step and the numbering moves). install_codex_hooks
    # .uninstall() catches its own SettingsUnreadable at all three points that
    # can raise one -- the read, the shape check, and now the write -- and
    # returns a "left it alone" sentence with the marker kept, so every failure
    # already arrives here as a line of report rather than an exception. A
    # handler for an exception that cannot arrive is a guard nobody can
    # falsify, and this file has been carrying several.
    print("      " + install_codex_hooks.uninstall(
        install_codex_hooks.hooks_file(), hook_shim_path()))

    config = os.path.join(install_codex_hooks.codex_home(), "config.toml")
    # Only when the file is really there. On the many machines with no Codex
    # at all, a paragraph about a config file that does not exist is noise
    # about a record that was never written.
    if os.path.exists(config):
        print(f"      Left in place: your Codex trust records in {config}.")
        print("      If you approved this hook in Codex, that approval stays")
        print("      on file, so installing Overwatch again works without asking")
        print("      you a second time. Remove its [hooks.state] entry by hand")
        print("      if you would rather Codex asked you afresh.")


def _live_sessions() -> int:
    """How many sessions the hooks are currently tracking.

    The most useful support answer after "are the hooks installed": whether
    they are actually firing. A count of zero on a machine where Claude Code
    is open says the hooks are configured and not running, which is a
    different problem from not being configured at all.
    """
    from pc.providers import claude_state
    try:
        counts, _, _ = claude_state.ClaudeStateProvider(
            path=os.path.join(overwatch_home(), "state"), sweep=False
        ).scan(time.time())
    except Exception:
        return 0
    return sum(counts.values())


def _rm_tree(root):
    """Remove a flat directory of per-session files."""
    try:
        for name in os.listdir(root):
            _rm(os.path.join(root, name))
        os.rmdir(root)
    except OSError:
        pass


def _rm_state_dir():
    """Remove ~/.overwatch/state and ~/.overwatch/state-codex, and their subdirectories.

    Both directories, because the Codex slots deliberately live apart from the
    Claude ones (pc/providers/codex_state explains why) -- and a slot
    directory left behind by an uninstall is not litter, it is a lie: the
    daemon would go on counting sessions of a tool it no longer hooks.

    Two levels deep and no deeper, by construction: the shim only ever creates
    <session>.state files and <session>/<agent> files, in whichever of the two
    directories its second argument chose. Walking rather than shutil.rmtree
    because this runs against a path under the customer's home and a bounded
    loop cannot be talked into deleting more than it was told.
    """
    for sub in ("state", "state-codex"):
        root = os.path.join(overwatch_home(), sub)
        try:
            names = os.listdir(root)
        except OSError:
            # Absent, which is the normal case for state-codex on a machine
            # that never ran Codex. `continue`, not `return`: the old single
            # directory could give up here, but giving up on the first of two
            # would leave the second untouched on exactly those machines.
            continue
        for name in names:
            p = os.path.join(root, name)
            if os.path.isdir(p):
                for inner in (os.listdir(p) if os.path.isdir(p) else []):
                    _rm(os.path.join(p, inner))
                try:
                    os.rmdir(p)
                except OSError:
                    pass
            else:
                _rm(p)
        try:
            os.rmdir(root)
        except OSError:
            pass


def hook_shim_status_note():
    """A one-line warning when the installed hook shim cannot do its job.

    `overwatch status` reports the activity hooks by comparing settings.json's
    command strings against the shim path. That check passed throughout the
    period when the feature was dead: the path existed, the hook ran, and the
    file it ran was simply older than the daemon reading its output. The
    daemon can repair this within five minutes of starting -- whether it
    actually will is a separate question the caller answers with
    `_shim_repair_is_live`, because this function only knows the file is
    wrong, not whether anything is left to fix it.

    Two faults, two sentences, because a reader does two different things
    about them. A shim that is ABSENT is not a shim that is stale: the hooks
    in settings.json are still wired to that path, so Claude Code runs a file
    that is not there, silently, on every event -- the pip never lights at
    all, where a stale shim lights it with the wrong field. Saying "out of
    date" about a missing file sends someone looking for a version mismatch
    in a file they will not find.

    This asks about existence FIRST because shim_is_current answers False for
    a file it cannot open, which is how the two faults came to share a
    sentence: absent and stale are the same value to it, and only one of them
    is what it means.
    """
    if not os.path.exists(hook_shim_path()):
        return "the activity hook shim is missing, so the hooks run nothing"
    if shim_is_current(hook_shim_path(), "overwatch-hook.sh"):
        return None
    return "the activity hook shim is out of date"


def statusline_shim_status_note():
    """The same check as `hook_shim_status_note`, for the other shim.

    `overwatch status` has reported "Status line installed at ..." from the
    file's mere presence since before DriftWatchdog existed -- the identical
    blind spot the Activity row had until shim_content_check was added to
    repair this shim too. Silent when the shim was never installed: a
    missing file already prints "not installed" two lines up, and asking
    whether a nonexistent file's contents are current is not a question
    worth another line.
    """
    if not os.path.exists(shim_path()):
        return None
    if shim_is_current(shim_path(), "overwatch-statusline.sh"):
        return None
    return "the status line shim is out of date"


def _shim_repair_is_live(bridge_running: bool) -> bool:
    """Will DriftWatchdog's next tick actually rewrite a stale shim?

    Three ways "the daemon replaces it within five minutes" can be false even
    though the shim really is stale: OVERWATCH_NO_WATCHDOG turns self-healing off
    entirely (install_statusline.drift_check and shim_content_check both
    check it first); shim_content_check no-ops with no install marker, the
    same "never installed, or deliberately uninstalled" rule drift_check
    documents; and with no bridge running there is no poll loop to tick at
    all -- `cmd_status` already knows that from the Bridge row two lines
    above and passes it in here rather than this function re-deriving it.
    Printing the promise when none of these hold is the same species of
    confidently-wrong copy this whole fix exists to end.
    """
    if os.environ.get(install_statusline.WATCHDOG_DISABLE_ENV):
        return False
    if not install_statusline._read_marker():
        return False
    return bridge_running


def _shim_repair_line(note: str, bridge_running: bool) -> str:
    """Format a stale-shim note, promising repair only when it will happen."""
    if _shim_repair_is_live(bridge_running):
        return f"{note} -- the daemon replaces it within five minutes of starting"
    return f"{note} -- run `{installed_bin()} install` to fix it"
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
