SleepyUnicon/Overwatch/firmware/src/usage_layout.h

#ifndef USAGE_LAYOUT_H
#define USAGE_LAYOUT_H

/*
 * Every coordinate on the gauge screen, in one place.
 *
 * These were inline magic numbers until a third row of widgets went in below
 * the gauges and the clearances stopped being obvious by eye. Two of them are
 * 2 px and 0 px, which is fine and also exactly the kind of thing that breaks
 * silently: bump the default font one size and the context readout lands on
 * top of the hint line. tests/usage_layout/host_test.c asserts the whole
 * arrangement from THIS header, so the check cannot drift from the code.
 *
 * Coordinates follow LVGL's alignment convention: X is an offset from the
 * named anchor (TOP_MID unless stated), Y is an offset from the top edge.
 */

/*
 * Every Y below sits on a 4 px rhythm, and the gaps between rows are 4 or 8.
 *
 * They were arbitrary -- 34, 84, 112, 170, 190 -- chosen one at a time to make
 * whatever had just been added fit. Individually reasonable, collectively the
 * reason a screen reads as assembled rather than designed: nothing lines up
 * with anything, and the eye notices even when it cannot say why.
 */

/* The CYD panel, landscape. */
#define SCR_W			320
#define SCR_H			240
#define SCR_MID_X		(SCR_W / 2)

/*
 * Line height of LV_FONT_DEFAULT. Pinned to CONFIG_LV_FONT_DEFAULT_MONTSERRAT_14
 * -- lv_font_montserrat_14.c declares .line_height = 16. Every unlabelled
 * label on this screen is this tall, and the clearances below are only true
 * for this value.
 */
#define FONT_LINE_H		16

/*
 * Line height of lv_font_montserrat_20, the percentage label's own font --
 * NOT FONT_LINE_H, which is the DEFAULT font's height and belongs to every
 * other label on this screen. lv_font_montserrat_20.c declares
 * .line_height = 22. Needed to centre GAUGE_PCT_Y inside the ring rather than
 * offsetting it from a moving edge.
 */
#define GAUGE_PCT_FONT_H	22

/* Header: brand to the RIGHT, quiet data left, the settings gear dead centre.
 * The brand had the middle until a top affordance needed it. */
#define TITLE_Y			6
#define HDR_ROW_Y		8
#define DOT_SZ			12
#define BRAND_TEXT		"OVERWATCH"
/*
 * How wide BRAND_TEXT actually draws, because the pip row shares its rows and
 * is positioned against it -- a guess is not good enough.
 *
 * 110 is measured off a render, not summed from the font's advance table.
 * "OVERWATCH" is nine glyphs and the hand arithmetic that used to live here
 * added up the five of "BLINK" (44 px plus letter_space), which stopped being
 * true at the rebrand and was not noticed because nothing derived from it
 * failed. Conservative on purpose: too wide only makes the layout test
 * stricter about the pip row's clearance.
 */
#define BRAND_W			110
/*
 * How far in from the right bezel the wordmark sits.
 *
 * A constant rather than the bare -30 usage_view.c used to pass to
 * lv_obj_align, because the pip row's clearance is measured against it and the
 * layout test has to see the same number the screen is built from. While it was
 * a literal in one file and "centred on SCR_MID_X" in the comment beside
 * BRAND_W, the test modelled a CENTRED wordmark: it computed a left edge of
 * 105, compared it against a hardcoded 134 left over from "BLINK", and failed
 * on both counts while the screen itself was correct (2026-09-26).
 *
 * 30 rather than 12: the status dot sits 12 px in and is 12 wide, so this
 * clears it by 6. usage_view.c drops the label's letter_space from 2 to 1 to
 * buy that back and keep the word clear of PIP_WALL_X.
 */
#define BRAND_RIGHT_OFF		30

/*
 * The clock sits under the brand, and it does NOT own a row of its own.
 *
 * It shares STATUS_Y with the hint line, and one of them is visible at a
 * time: the clock by default, a sentence only while something wants a person
 * -- see usage_activity_needs_row(). That is what pays for the arrangement.
 * An earlier version gave the clock its own row, and the whole cost came out
 * of the rings (120 down to 100) because everything below the arcs is pinned;
 * sharing costs nothing, because "Working" was only ever repeating what a
 * green pip already said.
 */

/*
 * The pip row: one mark per live session, from the left bezel to the brand.
 *
 * The clock used to sit in this corner and the row had to start clear of it,
 * at x=56, with 75 px to work in. The clock moved under the brand, so the row
 * begins at the bezel inset instead and has 120 px -- which is what lets
 * counts mode hold FOUR groups, and is why `finished` is no longer dropped on
 * an ordinary desk.
 *
 * Only the right bound is still a measurement, and BRAND_W above carries it
 * with its derivation. The left bound is just the bezel.
 *
 * PIP_MAX is geometry, not policy: eleven fit. The display switches to counts
 * at SIX, which is a claim about reading and not about width -- six pips were
 * checked against a rendered panel and read as six; nobody has checked eight.
 * The extra room went to making counts mode roomier rather than to cramming
 * more pips into a row nobody can count.
 *
 * Headroom that is really allocated, and that is the point. fmt_pips() never
 * returns more than six, so usage_view.c builds five pips and numerals that
 * can never be shown -- LVGL objects kept deliberately, because every bound in
 * that file derives from THIS constant and an array sized to the six that are
 * reachable would be a second number free to drift away from the geometry it
 * is supposed to match. The unused pairs are the cheaper of the two prices.
 */
#define PIP_SZ			8
#define PIP_PITCH		11
#define PIP_X0			10
#define PIP_WALL_X		130
#define PIP_MAX			11

/*
 * An 8 px pip on the 12 px health dot's centre line, written as the
 * difference rather than as the 2 it evaluates to: the header carries marks of
 * two sizes, and what makes it read as ONE row is that their centres agree.
 * Spelling it this way means it still agrees if either size changes.
 */
#define PIP_Y			(HDR_ROW_Y + (DOT_SZ - PIP_SZ) / 2)

/*
 * The tally's LINE BOX, centred on that same line -- not pinned to the row's
 * top like every other header label.
 *
 * A label is FONT_LINE_H tall whatever is written in it, so pinning it to
 * HDR_ROW_Y ran it 8..24 and put its bottom edge exactly on STATUS_Y, with
 * nothing between the numeral and the hint line. Aligning it to PIP_Y instead
 * -- to match its own pip -- is worse, not better: 10..26 overlaps the hint by
 * 2 px. What the numeral has to agree with is the pip's CENTRE, not its top,
 * so it is the box that gets centred: 14 - 16/2 = 6, running 6..22 and
 * clearing STATUS_Y by 2.
 *
 * That it lands on TITLE_Y is not a coincidence worth relying on, but it is
 * worth knowing: the numerals and the wordmark share a cap-line.
 */
#define PIP_NUM_Y		(PIP_Y + PIP_SZ / 2 - FONT_LINE_H / 2)

/*
 * Counts mode's metrics: pip, gap, numeral, then the gap to the next group.
 *
 * PIP_NUM_ADV is a MEASUREMENT of the widest digit, like the two bounds above
 * is a measurement of the brand. lv_font_montserrat_14 -- the
 * font this build links, pinned by CONFIG_LV_FONT_DEFAULT_MONTSERRAT_14 --
 * gives '4' an adv_w of 150 in 1/16 px, which is 9.375 px, in a 10 px ink box.
 * 9 truncates both, and a two-digit tally drawn 9 px per digit creeps right
 * with every digit until it reaches the brand. 10 covers every digit with the
 * ink box to spare.
 *
 * The pixel comes back out of PIP_GROUP_GAP, so the BUDGET for one group is
 * 26 px: FOUR of them from PIP_X0 would start at x = 10 / 36 / 62 / 88 and end
 * at 108, well inside PIP_WALL_X. That is how the wall was checked, and it is
 * what the layout test asserts. It is not where the pips land -- a row of
 * "1"-shaped tallies really starts nearer 10 / 31 / 52, because '1' is not as
 * wide as the budget assumes.
 *
 * PIP_NUM_ADV is that budget, not what the drawing uses. refresh_dots() measures
 * the string it actually wrote (lv_text_get_size) and stops at the wall,
 * because billing every digit the widest one's advance drops groups that had
 * room -- '1' advances 5.2 px, not 10. What this constant is for is choosing
 * the constants around it, and asserting in the layout test that the
 * single-digit case those constants promise still fits.
 */
#define PIP_NUM_GAP		2
#define PIP_NUM_ADV		10
#define PIP_GROUP_GAP		6

/*
 * Whose numbers these are, directly under the brand.
 *
 * ONE label for the whole screen, not a name beside each countdown. With one
 * provider per page there is exactly one answer, and writing it twice under
 * two gauges spent a line each time to repeat the same word -- which is also
 * what pushed those countdowns to a width that had to carry "claude  6d 22h"
 * instead of just a duration.
 *
 * It belongs under OVERWATCH because that is the header's job: what you are
 * looking at. The gauges then say only how much and how long.
 *
 * BOUNDED, not auto-sized. A label left to size itself grows with its text,
 * and the daemon's tag cap is 11 characters; fixing the width means an
 * unexpected tag ellipsizes instead of reaching into the corners where the
 * clock and the status dot live.
 */
/*
 * The line under the brand carries the STATUS now, not the provider's name.
 *
 * The name moved to the bottom, where it became the control that changes it
 * (see the pill in usage_view and mk_page_zone in ui_settings). Having it
 * here as well was the same fact twice on one screen -- the header said
 * "Codex" while the pill said "Claude", which is two names and one page and
 * the reader has to work out which is which.
 *
 * The status took the freed line rather than the layout keeping a hole. It is
 * the better home for it: a warning belongs where the eye lands first, and it
 * had been sharing the bottom line with whatever else wanted it. Full width
 * here, because "Reading is old - showing last known" is 35 characters, and
 * full width is safe because the row above carries only the clock and the
 * dot, each confined to its own corner.
 */
#define STATUS_Y		24
#define STATUS_MAX_W		300


/*
 * An execution-state indicator is BACK, and this is not a revert of the
 * decision that removed it.
 *
 * Commit 6540287 ("colour meant three different things, and two dots said
 * the same one") pulled a top-left activity pip and a top-right status dot
 * into one indicator, for two reasons: the top-left corner was occupied by
 * the clock, and two unlabelled circles in the same green/amber/red
 * vocabulary said unrelated things with no way to tell which.
 *
 * Both reasons are answered now, not ignored. What came back is a ROW, at
 * PIP_X0 above, and the corner IS part of the answer this time -- the clock
 * left it for the row under the brand, which it shares with the hint. And that
 * hint names whichever condition fired, so the marks up there are no longer
 * unlabelled: colour gets you "something is wrong", the sentence gets you
 * which. That is the arrangement commit 6540287 could not have had, because
 * the label did not exist yet.
 *
 * The sentence is not always there, and that is the trade. It appears only
 * while something wants a person -- see usage_activity_needs_row() -- because
 * a line reading "Working" over a row of working pips was the panel spending
 * its only sentence to repeat itself. The rest of the time the clock has it,
 * and the colour is on its own again. That is acceptable HERE and was not in
 * 6540287: back then colour was the only channel and there were two circles
 * competing in it; now there is one row, and a sentence that arrives exactly
 * when colour alone would not be enough.
 *
 * The row also answers something that commit did not raise and the single pip
 * it removed could not have fixed: one mark cannot speak for several
 * sessions. One per session can.
 *
 * See refresh_dots() in usage_view.c -- with the s, one call refreshing both
 * the health dot and the row.
 */

/* The two arcs. */
/*
 * Pulled in from 80 so the side arrows have room to exist.
 *
 * At 80 with a 120 px arc the two dials spanned x=20..140 and 180..300, which
 * left 20 px of margin either side -- and the left and right hit strips are
 * 44 wide (ui_settings.c mk_edge_zone). The arrows were drawn ON the dials.
 * 64 with a 100 px arc spans 46..146 and 174..274, so each edge keeps 46 px
 * clear: the strip fits with 2 px to spare.
 */
/*
 * The bottom edge's face cue: two eyes and a mouth in a box.
 *
 * Here rather than as literals in build_face_cue() because the gauges are
 * positioned against its top edge. While the size lived only in that function
 * and "210" lived only in a comment, the cue was redrawn from 40x26 to 28x18
 * and the comment kept claiming 210 -- so the one number the ring's placement
 * depended on was prose that had been wrong for a release.
 */
#define FACE_CUE_W		28
#define FACE_CUE_H		18
#define FACE_CUE_BOTTOM_OFF	2
#define FACE_CUE_TOP_Y		(SCR_H - FACE_CUE_BOTTOM_OFF - FACE_CUE_H)

/* Where the header stops and the gauges' band begins: STATUS_Y plus its line. */
#define HDR_BOTTOM_Y		(STATUS_Y + FONT_LINE_H)

#define GAUGE_CX		64
/*
 * Centred in the band that is actually free, not in the screen.
 *
 * At 44 the arcs ran 44..144 and left 66 px of nothing between them and the
 * face cue -- the dials read as pinned to the top, which is what was
 * reported. The header ends at HDR_BOTTOM_Y (40) and the face cue begins at
 * FACE_CUE_TOP_Y, so the arc is centred in the band between them.
 *
 * 75 was worked out when the cue was 40x26 and began at 212; it has since been
 * drawn at 28x18 and begins at 220, which leaves 35 px above the ring and 45
 * below rather than the same gap top and bottom. Ten pixels on a 240 px panel
 * is well under what anyone reads as lopsided, so the ring has not been moved
 * for it -- but the two numbers are constants now and the layout test bounds
 * the asymmetry, so the next change to either end cannot quietly widen it.
 *
 * It also lands the arc's middle within 5 px of the side cues, which sit at
 * LV_ALIGN_*_MID and so at y=120. Those read as a row with the dials now
 * rather than floating below them.
 */
#define GAUGE_ARC_Y		75
#define GAUGE_ARC_SZ		100
/*
 * Centred on the ring, not offset from its top.
 *
 * The ring has changed size and position several times. An earlier version of
 * this preserved "46 px from the arc's top", which preserved an offset from an
 * edge that had moved rather than where the number actually sits inside the
 * ring, and a reader saw a percentage sitting low in its ring by about 20 px.
 * Centring on the ring is the invariant a reader can actually see, and writing
 * it as an expression in GAUGE_ARC_Y and GAUGE_ARC_SZ means the pair follows
 * automatically the next time the ring moves.
 *
 * What is centred is the PAIR -- the unit line and the percentage under it --
 * not the percentage alone. The block below does that arithmetic.
 */
/*
 * Unit over percentage, both INSIDE the ring.
 *
 * The caption used to sit below the arc ("SESSION 5h") with the countdown
 * under that, which spent two lines of screen on saying what the ring already
 * implied and left the ring itself empty apart from a number with no unit.
 * Stacking them puts the whole fact in one place: 5h, then 2%.
 *
 * The arc runs GAUGE_ARC_Y..+GAUGE_ARC_SZ, so 75..175 and its middle is 125.
 * The unit is a 16 px line at 107 and the percentage a 22 px one at 123, so
 * the pair occupies 107..145 and centres on 126 -- one pixel low, which is
 * the right way to miss: the ring's gap is at the bottom.
 */
#define GAUGE_UNIT_Y		(GAUGE_ARC_Y + 32)
#define GAUGE_PCT_Y		(GAUGE_ARC_Y + 48)
/*
 * The ring's own hollow (GAUGE_ARC_SZ minus the stroke on both sides), not a
 * guess -- this used to just equal that by coincidence (96 = 120 - 2*12
 * before the ring shrank) until the ring did and the width didn't follow. A
 * label wider than the hollow paints over the coloured track it sits on.
 */
#define GAUGE_PCT_MAX_W		(GAUGE_ARC_SZ - 2 * GAUGE_ARC_W)

/*
 * The countdown moved INSIDE the ring, under the percentage.
 *
 * An arc's hollow centre was carrying one number and about sixty percent
 * nothing, while the row below the gauges was trying to fit a caption, a
 * countdown, a context meter and a hint into the last thirty pixels of the
 * panel. Putting the countdown where its own percentage already is costs no
 * new space, pairs the two numbers that belong together -- how much is gone,
 * how long until it comes back -- and frees a whole row underneath.
 */
/*
 * There is no caption row under the gauge any more, so there is no
 * GAUGE_NAME_Y. The caption is a line INSIDE the ring at GAUGE_UNIT_Y, above
 * the percentage -- see the block above those two.
 *
 * It was still defined as 168 long after nothing read it, which is how the
 * layout test came to assert that the ring's bottom (175) sat above a caption
 * that was not there, and to fail for it.
 */
/*
 * The countdowns STACK, one per provider, rather than sitting side by side.
 *
 * Side by side, each got 72 px and could hold a duration and nothing else --
 * so which provider a countdown belonged to had to be inferred from its
 * colour, and the provider names ended up exiled to a line at the bottom of
 * the panel that said "inner ring: codex" and helped nobody.
 *
 * Stacked, each line has the full width of its gauge, which is enough to write
 * the provider's name next to its own number. The label is the thing that was
 * missing; the stack is what made room for it.
 */
#define GAUGE_CD_Y		186	/* first line: the primary provider */
#define GAUGE_CD_MAX_W		96	/* "00m 00s" -- named once, up top */

/* The ring itself. */
#define GAUGE_ARC_W		12

#define GAUGE_BALL_PAD		2
/* A ring of panel ground around each ball, so it separates from the arc it
 * rides regardless of that arc's colour. */
#define GAUGE_BALL_RING		2

/* Context row, in the band between the countdowns and the hint. */
/*
 * No context row.
 *
 * It showed one context window, and with several agents running there are
 * several -- at different levels, refilling at different times, belonging to
 * conversations the panel cannot name. "88% of 4" was an attempt to qualify
 * one number into honesty and it did not earn its line: knowing that the
 * fullest of four contexts is at 88% does not tell you which one, and there is
 * nothing to do about it from across the room.
 *
 * The two things a desk gauge can answer -- how much quota is left, and how
 * long until it refills -- get the space instead.
 */

/* Session and agent counts, in the bottom line the hint also uses. */
#define SESS_BOTTOM_OFF		20
#define SESS_MAX_W		200	/* "9 sessions  9 agents" */

/*
 * The provider pill, bottom-centred above the rail: whose numbers these are,
 * and the control that changes it.
 *
 * State and control as one object, which is the idiom the settings panel's
 * old "Main source" row used before one provider per page replaced it. It
 * always shows, because it is the only thing on the screen that names the
 * page -- unlike the hint it used to share this line with, which is why the
 * hint moved up to STATUS_Y.
 */
/*
 * 16 px up, and the height is 20: the line plus 2 px of padding each side.
 *
 * The band it has to live in is exactly 24 px -- the countdowns end at 202
 * (GAUGE_CD_Y + FONT_LINE_H) and the rail begins at 226 -- so the padding is
 * what it can afford rather than what would look most generous. It lands at
 * 204..224, clear of both by 2. The first attempt used 3 px of padding and a
 * 20 px offset, which put it through the countdowns; the layout test caught
 * it before the board did.
 */
#define PILL_BOTTOM_OFF		16
#define PILL_PAD_V		2
#define PILL_H			(FONT_LINE_H + 2 * PILL_PAD_V)
#define PILL_MAX_W		140

/*
 * Clearances the layout must keep. Named so a failure says which rule broke
 * rather than printing two numbers.
 */
/*
 * The page rail: one mark per provider, along the bottom edge.
 *
 * BOTTOM rather than a side edge because both sides are already spoken for --
 * the chevrons there mean settings and the boot clip, and a dot column beside
 * them would be a third meaning on an edge that already carries one.
 *
 * Each mark is coloured by ITS OWN page's severity, which is what buys back
 * the only thing splitting the providers costs: with both on one gauge you
 * could see the second one going red without looking for it. Now the rail
 * says that instead, and says it from whichever page you happen to be on.
 *
 * Position is carried by WIDTH, never by colour, so the two channels never
 * compete for the same pixels.
 */
#define RAIL_PAGES_MAX		2
#define RAIL_H			6
#define RAIL_DOT_W		6
#define RAIL_ACT_W		16
#define RAIL_PITCH		14
#define RAIL_BOTTOM_OFF		8

#define SCR_RIGHT_MARGIN_MIN	4	/* nothing flush against the bezel */

/*
 * The status-change popup: one sentence, five seconds, over the bottom band.
 *
 * The owner asked for it as a popup -- "session x is finished, session y is
 * waiting for you" -- and the panel has no free space, so a popup here is
 * always a card ON TOP of something. What it may cover is therefore the whole
 * design question, and the answer is: not the two things a glance is for.
 *
 * NOT THE PIP ROW and NOT THE PERCENTAGE. Those are what someone crossing the
 * room reads without stopping, and a card over either of them makes the panel
 * worse for five seconds in exchange for a sentence they did not ask to read
 * right then. The band below the arcs is the opposite kind of information --
 * a countdown, a caption, the provider's name -- none of it changing in five
 * seconds and none of it what the eye goes to first.
 *
 * So the card takes the strip from just above the countdowns to just above
 * the page rail: 184..224 on a 240 px panel, clearing the arcs (which end at
 * 164) by twenty pixels and the rail by two. The rail stays visible on
 * purpose -- it is the only thing that says which page you are on, and a
 * popup that hid it would leave the reader unsure whose session the sentence
 * is even about.
 *
 * Written as expressions against the constants it has to clear, so it follows
 * if the rail moves or the countdowns do; tests/usage_layout asserts every one
 * of those clearances.
 */
#define TOAST_TOP_Y		(GAUGE_CD_Y - 2)
#define TOAST_BOTTOM_OFF	(RAIL_BOTTOM_OFF + RAIL_H + 2)
#define TOAST_H			(SCR_H - TOAST_BOTTOM_OFF - TOAST_TOP_Y)
#define TOAST_PAD_V		((TOAST_H - FONT_LINE_H) / 2)
/*
 * 288 px: "A session is waiting for you" whole, with both bezels clear.
 *
 * It is a budget for the sentences that carry no project name, because those
 * are the ones that MUST fit -- there is no shorter thing for them to fall
 * back to. A named one ("LiveClaudeUi is waiting for you") also fits, and a
 * pathological 27-character label does not and ellipsizes, which is the same
 * bargain the hint line already makes.
 */
#define TOAST_MAX_W		288

/*
 * Five seconds, from the owner, and counted in whole seconds off the same
 * usage_view_tick_1s() the countdowns use rather than an LVGL timer -- one
 * clock for everything on this screen that expires, and the peek card's
 * auto-hide already works this way.
 */
#define TOAST_TTL_S		5

#endif /* USAGE_LAYOUT_H */
