SleepyUnicon/Overwatch/firmware/src/usage_view.c

/*
 * The gauge screen: Session (5h) and Weekly (7d) as arcs, with live countdowns.
 *
 * This is the one sink both data sources feed -- the USB bridge today, direct
 * WiFi fetching later -- so both modes render through identical code.
 */
#include <zephyr/kernel.h>
#include <lvgl.h>
#include <stdio.h>
#include <string.h>

#include "usage_view.h"
#include "usage_layout.h"
#include "fmt.h"
#include "usage_state.h"
#include "cfg_store.h"
#include "ui_theme.h"

/* Severity colours: green under 60%, amber approaching, red near the limit. */
#define COL_BG	lv_color_hex(ui_theme()->bg)	/* plain white ground */
#define COL_PANEL	lv_color_hex(ui_theme()->panel)	/* cards, barely off the ground */
#define COL_TRACK	lv_color_hex(ui_theme()->track)	/* the unfilled arc */
#define COL_TEXT	lv_color_hex(ui_theme()->text)	/* near-black ink, 18.5:1 on white */
#define COL_DIM	lv_color_hex(ui_theme()->dim)	/* secondary ink, 5.98:1 */
/*
 * The severity ramp: green, amber, red -- and all three sit inside a 1.16x
 * luminance band on purpose.
 *
 * They used to span 2.30x, INVERTED: amber at 11.39:1 was the brightest thing
 * on the panel and red at 4.95:1 was the dimmest, so the merely-getting-close
 * colour shouted over the critical one. Brightness is attention on a dark
 * panel, so that was the hierarchy the eye actually applied, whatever the code
 * intended.
 *
 * The fix is not a brighter red -- a red bright enough to outshine a yellow is
 * a pale salmon and stops reading as red at all; that is the physics of
 * luminance, not a palette choice. So luminance is held flat and urgency is
 * carried by hue and by the arc's own area. A 95% arc is a nearly-complete
 * ring; it does not need to shout as well.
 *
 * WHAT CHANGED, 2026-08-27, and it is the part worth reading. Holding
 * luminance flat was right; paying for it with SATURATION was not. The first
 * version of this ramp ran 0.58 -> 0.66 -> 0.72 and called that gradient the
 * urgency signal. On the actual panel the user's verdict was "the green looks
 * like gray", and they were right twice over:
 *
 *   - 0.58 saturation is 42% of the way to grey before the panel touches it,
 *     and the old green sat at hue 150 with MORE BLUE THAN RED (#4AB07D:
 *     R=74, B=125). That is a sea green, and a sea green on a cheap ILI9341
 *     is a grey.
 *   - a saturation ramp of 0.58 -> 0.72 is not a signal anyone can read at
 *     60 cm. Hue is what carries green/amber/red, instantly, for everyone who
 *     can resolve it; the arc's area carries it for everyone else. The ramp
 *     was spending real colour to encode something nothing else needed.
 *
 * So saturation is now near the top of the range at every step (0.92, 0.96,
 * 1.00) and the flat band is unchanged. All three were re-derived against the
 * background AND re-checked after quantisation to RGB565, which is what the
 * panel actually shows -- see tests/usage_contrast, where computing contrast
 * for a colour the hardware cannot display was the gap that let this ship.
 */
#define COL_GREEN	lv_color_hex(ui_theme()->green)	/* 5.46:1 - white gives the severity ramp room the orange never could */
#define COL_GREEN_INK	lv_color_hex(ui_theme()->green_ink)
#define COL_AMBER	lv_color_hex(ui_theme()->amber)	/* 5.93:1 */
#define COL_RED	lv_color_hex(ui_theme()->red)	/* 6.15:1 */
/* 3.91:1 against the background. Was #555B63 at 2.76:1, which is under the
 * 3:1 minimum for a graphic element -- and these are the swipe chevrons, which
 * exist only because nobody discovered the gestures without them. An
 * affordance too dim to notice is not an affordance. */
#define COL_GREY	lv_color_hex(ui_theme()->grey)	/* 3.99:1 */

/*
 * Provider identity colours.
 *
 * Colour now says WHICH TOOL a ring belongs to, which means it is no longer
 * saying how close that tool is to its limit. Severity moved to the numerals
 * instead -- the percentage in the middle of each gauge still runs
 * green/amber/red -- so the warning is still there, just carried by the text
 * rather than the ring. Worth knowing when reading this file: the ring tells
 * you whose, the number tells you how bad.
 */
/*
 * Identity colours, and they sit BELOW the severity ramp deliberately.
 *
 * The teal used to measure 10.16:1 -- brighter than every severity colour, so
 * a codex ball at 5% pulled more attention than a Claude arc at 95%. Identity
 * outranking urgency is exactly backwards. Both now sit inside the severity
 * band, still 1.56:1 apart from each other so the pair survives for anyone who
 * cannot resolve the hue difference.
 */
#define COL_OTHER	lv_color_hex(ui_theme()->other)	/* anything else: a cool blue */

struct gauge {
	lv_obj_t *arc;
	lv_obj_t *pct;
	lv_obj_t *name;
	lv_obj_t *countdown;	/* primary provider's time left */
	int32_t resets_in_s;	/* -1 = unknown; ticked down locally */
	int32_t resets2_in_s;	/* ...and the second provider's */
	/*
	 * How fast this window is filling, %/hour, or 0 for "no answer".
	 *
	 * Drawn in the countdown's place, and ONLY when there is no countdown.
	 * The daemon guarantees the two are mutually exclusive (pc/normalizer
	 * drops the rate the moment any source supplies a reset time), so this
	 * never has to arbitrate between them -- it just prefers the real
	 * countdown and falls back.
	 */
	double burn;
};

static struct gauge session, weekly;
/*
 * Two attention indicators -- but not the two 6540287 removed.
 *
 * There was a status dot top-right (is the data trustworthy) and an activity
 * pip top-left (what is Claude Code doing). 6540287 collapsed them into one
 * dot coloured by the WORSE of the two, and gave two reasons: two unlabelled
 * circles in the two most prominent corners, in the same green/amber/red
 * vocabulary, saying unrelated things -- a red dot could mean "you are rate
 * limited", "a tool is wedged" or "the cable fell out", and the panel gave no
 * way to tell -- and the top-left corner belonged to the clock anyway.
 *
 * Both reasons are answered now, and neither by taking the corner back. The
 * execution axis is not a circle in a corner at all: it is a ROW across the
 * empty gap between the clock and the brand, so the clock keeps the corner it
 * always had. And the hint line below NAMES whichever condition fired, so
 * neither indicator is unlabelled any more. What "worse wins" cost was real:
 * a stale reading painted over a failed session and the panel showed only the
 * milder of the two facts. So each axis gets its own place -- data health in
 * the right corner, execution state across the header -- and neither hides
 * the other.
 *
 * ONE MARK PER SESSION, which is the fact a single dot could never carry. Four
 * sessions with one of them holding a permission prompt drew exactly the same
 * amber circle as one session doing the same thing, so the indicator answered
 * "something wants you" and never "how much of this is waiting". fmt_pips()
 * owns what the row says -- mode, order, overflow -- and everything here only
 * positions and colours its answer.
 */
static lv_obj_t *dot;		/* data health, top-right */
static lv_obj_t *pip[PIP_MAX];		/* execution state, one per session */
static lv_obj_t *pip_num[PIP_MAX];	/* its tally, in counts mode only */
/*
 * The last counts the daemon sent, kept because refresh_dots() is reached from
 * several causes that carry no counts of their own -- a status change, a page
 * change -- and each of those must redraw the same row rather than blank it.
 */
static int pip_n_sess, pip_n_run, pip_n_wait, pip_n_stuck;
static enum usage_status data_health = USAGE_STATUS_DISCONNECTED;
static lv_obj_t *hint;
static lv_obj_t *age_lbl;
static lv_obj_t *clock_lbl;
static enum usage_activity activity = USAGE_ACTIVITY_NONE;
/*
 * The status-change popup: a card over the bottom band, five seconds, gone.
 *
 * WHAT IS HERE IS ONLY POSITION AND TIMING. Whether a change is worth
 * announcing is usage_toast_change(); what the sentence says is fmt_toast().
 * Both of those are decisions and this file has no automated coverage -- it
 * needs LVGL and Zephyr and cannot be compiled on a laptop -- so a decision
 * left in here is a decision nothing checks. That is why usage_state.c and
 * fmt.c exist at all.
 *
 * `toast_prev` is the counts the next message will be compared against, and
 * it is updated on EVERY message, including the ones whose popup is
 * suppressed. A suppressed change is consumed, not queued: a board waking
 * from a night's sleep should show what is true now, not replay eight hours
 * of transitions at somebody standing over it.
 */
static lv_obj_t *toast;
static lv_obj_t *toast_lbl;
static int toast_ttl;			/* seconds left; 0 = not showing */
static struct usage_counts toast_prev;
static bool toast_have_prev;
static bool sleeping;
/* Filled by usage_view_set_session() from the daemon; see proto.c. */
static char session_label[28] = "";
static char provider1_tag[12];	/* whichever provider the daemon made primary */
static lv_obj_t *provider_lbl;	/* the tag, spelled out under the brand */
static char provider2_tag[12];	/* "" when there is only one provider */

/*
 * PAGES. One provider per screen, reached by swiping vertically.
 *
 * There is only ONE set of gauge widgets. The pages are identical in shape --
 * a session arc, a weekly arc, two countdowns -- so a second tree would be the
 * same objects twice over on a board with 96 KB of DRAM to spare. What changes
 * between pages is which provider's numbers are pushed into them, so the page
 * is a data selection, not a screen.
 *
 * Both pages' countdowns tick regardless of which one is showing: a window
 * does not stop closing because you are not looking at it, and a page that
 * caught up only when you arrived would show a stale figure for the moment
 * that matters most.
 */
struct page_data {
	/*
	 * This page's own age. See usage_view_set_provider2 -- the panel used
	 * to carry one flag for both providers, and showed it whichever page
	 * was in front of you.
	 */
	bool stale;
	double s_pct, w_pct;
	int32_t s_in_s, w_in_s;
	/* Per page, like everything else here: the rate describes THIS
	 * provider's session window, and page 1 has its own reset times and so
	 * never carries one. */
	double burn;
	/*
	 * How old THIS page's reading is, in seconds, or -1 when the daemon
	 * did not say. Per page for the same reason `stale` is: the two
	 * readings come from different files, refreshed at different times,
	 * and only one page is in front of you.
	 */
	int32_t age;
	bool have;
};
static struct page_data pg[RAIL_PAGES_MAX];
static int cur_page;
static lv_obj_t *rail_dot[RAIL_PAGES_MAX];

static const char *page_tag(int i)
{
	return i == 0 ? provider1_tag : provider2_tag;
}

/*
 * A provider tag as a NAME: "codex" -> "Codex".
 *
 * The tags arrive lowercase from the daemon, which is right for a wire
 * protocol and wrong for a panel -- OVERWATCH is the only all-caps thing in the
 * header, and everything beneath it is sentence case. Two places need this
 * now, the name under the brand and the line that says where the other page
 * is, and they were drifting apart the moment there were two of them.
 */
static void tag_cased(char *dst, size_t n, const char *tag)
{
	snprintf(dst, n, "%s", tag);
	if (dst[0] >= 'a' && dst[0] <= 'z') {
		dst[0] = (char)(dst[0] - 'a' + 'A');
	}
}

static int page_count(void)
{
	return provider2_tag[0] ? 2 : 1;
}
/* Defined below; set_provider2 has to call it, because whether a second
 * provider exists is what decides if the FIRST one is coloured at all. */
static void refresh_provider1(void);
static void refresh_rail(void);
static void render_gauges(void);
static lv_obj_t *overlay;	/* full-screen "no data" takeover */
static lv_obj_t *wait_big;	/* the takeover's CONNECTING title */
static bool built;
static bool have_data;		/* distinguishes "no host yet" from "host lost" */
static int32_t age_s = -1;	/* seconds since the last usage message */
static double last_s_pct = -1;	/* latest numbers, for the near-limit hint */
static double last_w_pct = -1;
static enum usage_status last_status = USAGE_STATUS_DISCONNECTED;

/*
 * Per-model weekly windows -- and the long-press card that picks between
 * them -- exist only in standalone WiFi mode. That mode reads Claude's usage
 * endpoint directly and gets a per-model breakdown with it. The USB path
 * gets its numbers from Claude Code's status line, and that payload carries
 * the two overall windows and nothing else; pc/statusline_source.py sends an
 * empty models list because there is nothing to put in one.
 *
 * So on a USB unit the card offered a choice between a real number and a
 * permanent "--%" -- and because the choice is kept in NVS, choosing the
 * empty one stuck across reboots, leaving a gauge reading "--%" for good
 * with no route back that anyone would find. Compiled out rather than
 * disabled: a control that cannot do anything is worse than no control.
 */
#if IS_ENABLED(CONFIG_OVERWATCH_WIFI_MODE)
#define HAVE_PER_MODEL 1

/* Long-press peek: a card of per-model weekly numbers that STAYS up -- tap
 * a row to point the weekly gauge at that model, tap anywhere else (or wait
 * out the timer) to dismiss. v1 hid it on finger-up, which on this jittery
 * panel meant it vanished before it could be read, let alone used
 * (hardware 2026-07-17). */
#define PEEK_ROWS 2			/* Claude's windows today: all + fable */
static lv_obj_t *peek;
static lv_obj_t *peek_row[PEEK_ROWS];
static lv_obj_t *peek_row_lbl[PEEK_ROWS];
static int weekly_sel;			/* 0 all models, 1 fable */
static int peek_ttl;			/* auto-hide countdown, 0 = idle */
static int64_t peek_shown_ms;
static double model_fable = -1;
#else
#define HAVE_PER_MODEL 0
#endif

static void render_weekly(void);
static void render_age(void);
/* Defined beside pip_colour(), which it borrows; called from the 1 s tick,
 * which runs earlier in this file. */
static void toast_hide(void);
#if HAVE_PER_MODEL
static void peek_fill(void);
#endif

void usage_view_set_models(double fable_pct)
{
#if !HAVE_PER_MODEL
	/* Nothing on this build produces a per-model number: the daemon sends
	 * no such key and proto.c passes its -1 default straight through.
	 * Kept as a symbol so both data paths still share one header. */
	ARG_UNUSED(fable_pct);
}
#else
	/* Per-model windows reset with the overall weekly, so a zero weekly
	 * means the fable number is stale too. Derive that from the weekly
	 * state itself (last_w_pct) rather than a flag set by an earlier call,
	 * so BOTH ways the weekly can empty are covered: an update reporting
	 * the reset, AND the local countdown ticking to zero via
	 * expire_weekly(). fable is a component of the weekly, so weekly 0%
	 * always implies fable 0%. */
	if (last_w_pct == 0 && fable_pct >= 0) {
		fable_pct = 0;
	}
	model_fable = fable_pct;
	if (built) {
		render_weekly();
		if (peek && !lv_obj_has_flag(peek, LV_OBJ_FLAG_HIDDEN)) {
			peek_fill();
		}
		/* The near-limit hint is computed in set_status from model_fable,
		 * but the models event usually lands right AFTER the usage update
		 * that ran it -- so re-run it here or the Fable warning lags a
		 * whole poll and is missing on the first frames after a reboot
		 * (user-reported 2026-07-20). */
		if (last_status == USAGE_STATUS_OK) {
			usage_view_set_status(USAGE_STATUS_OK);
		}
	}
}
#endif /* HAVE_PER_MODEL */

/* One CONNECTING screen for every boot, USB and standalone alike: a segmented
 * bar that fills green as the worker gets through it, current step named
 * below (option D of the mockups, user-picked 2026-07-15; unified across
 * modes per user request 2026-07-16). The mode passes its own step list to
 * usage_view_boot_begin(). */
#define BOOT_STEPS_MAX 3
static lv_obj_t *boot_seg[BOOT_STEPS_MAX];
static lv_obj_t *boot_cnt;	/* "1 / 3" over the bar */
static lv_obj_t *boot_step;	/* current step name under the bar */
static int boot_active = -1;	/* segment currently pulsing, -1 = none */
static lv_obj_t *boot_hint;	/* the cable hint, after a while on step 1 */
static int boot_hint_s;		/* seconds spent on the current step */
#define BOOT_HINT_AFTER_S 20
static const char *const *boot_txt;
static int boot_n;

/*
 * Bound before the cast, never after. usage_view_update has a second caller
 * besides the serial path: main.c's on-device OAuth client, whose figures come
 * from a bare strtod in usage_parse.c with no range check at all, so nan, inf
 * and 1e300 all arrive here. Converting an out-of-range double to int32_t is
 * undefined behaviour -- the very defect proto.c's num() exists to avoid --
 * and `pct < 0` does not catch nan, because nothing compares true to nan.
 */
#define PCT_DISPLAY_MAX 1000

/*
 * Extra usage puts a real reading above 100, and the ring has nowhere left to
 * go -- so it saturates while the label keeps the true figure. Letting LVGL
 * clamp it internally would look the same today and is not a promise it
 * makes, and "at the limit" and "past it" must not draw identically.
 */
static int32_t pct_int(double pct)
{
	if (!(pct > 0.0)) {	/* nan fails this too, and lands on 0 */
		return 0;
	}
	if (pct > (double)PCT_DISPLAY_MAX) {
		return PCT_DISPLAY_MAX;
	}
	return (int32_t)(pct + 0.5);
}

static int32_t arc_value(double pct)
{
	int32_t v = pct_int(pct);

	return v > 100 ? 100 : v;
}

static lv_color_t severity(double pct)
{
	if (pct >= 90.0) {
		return COL_RED;
	}
	if (pct >= 60.0) {
		return COL_AMBER;
	}
	return COL_GREEN;
}

static void build_gauge(struct gauge *g, lv_obj_t *parent, lv_coord_t cx,
			const char *title)
{
	g->resets_in_s = -1;

	g->arc = lv_arc_create(parent);
	lv_obj_set_size(g->arc, GAUGE_ARC_SZ, GAUGE_ARC_SZ);
	lv_obj_align(g->arc, LV_ALIGN_TOP_MID, cx, GAUGE_ARC_Y);
	lv_arc_set_rotation(g->arc, 135);
	lv_arc_set_bg_angles(g->arc, 0, 270);
	lv_arc_set_range(g->arc, 0, 100);
	lv_arc_set_value(g->arc, 0);
	/* The knob is kept, not deleted: it is the only part that tracks the
	 * end of the indicator, and that is where the provider ball goes. The
	 * arc stays unclickable -- this is still a readout. */
	lv_obj_clear_flag(g->arc, LV_OBJ_FLAG_CLICKABLE);
	lv_obj_set_style_pad_all(g->arc, GAUGE_BALL_PAD, LV_PART_KNOB);
	lv_obj_set_style_bg_color(g->arc, COL_TEXT, LV_PART_KNOB);
	lv_obj_set_style_bg_opa(g->arc, LV_OPA_COVER, LV_PART_KNOB);
	/*
	 * A ring of the panel's own ground, so the ball separates from the arc
	 * it sits on whatever colour that arc happens to be. Without it the
	 * ball measured 1.24:1 against a red arc and 1.07:1 against a green one
	 * -- it vanished into the track at exactly the moments the track was
	 * saying something.
	 */
	lv_obj_set_style_border_color(g->arc, COL_BG, LV_PART_KNOB);
	lv_obj_set_style_border_width(g->arc, GAUGE_BALL_RING, LV_PART_KNOB);
	lv_obj_set_style_border_opa(g->arc, LV_OPA_COVER, LV_PART_KNOB);
	lv_obj_set_style_arc_width(g->arc, GAUGE_ARC_W, LV_PART_MAIN);
	lv_obj_set_style_arc_width(g->arc, GAUGE_ARC_W, LV_PART_INDICATOR);
	lv_obj_set_style_arc_color(g->arc, COL_TRACK, LV_PART_MAIN);
	lv_obj_set_style_arc_color(g->arc, COL_GREEN, LV_PART_INDICATOR);

	/* The second provider's ring, hidden until one exists. Created before
	 * the labels so the text draws over it, not under. */
	/*
	 * Fixed width, centred text.
	 *
	 * Montserrat's digits are PROPORTIONAL -- measured from the font data,
	 * '1' is 5.19 px at size 14 against 9.38 px for '4', and 7.38 vs 13.38
	 * at size 20. An auto-sized label therefore changes width as the digits
	 * change, and a countdown ticking once a second re-lays-out its whole
	 * row. Pinning the box stops that reaching anything else on the panel.
	 * The text still re-centres inside it, which is what a clock does.
	 */
	g->pct = lv_label_create(parent);
	lv_label_set_text(g->pct, "--%");
	lv_obj_set_style_text_color(g->pct, COL_TEXT, 0);
	lv_obj_set_style_text_font(g->pct, &lv_font_montserrat_20, 0);
	lv_obj_set_width(g->pct, GAUGE_PCT_MAX_W);
	lv_obj_set_style_text_align(g->pct, LV_TEXT_ALIGN_CENTER, 0);
	lv_obj_align(g->pct, LV_ALIGN_TOP_MID, cx, GAUGE_PCT_Y);

	g->name = lv_label_create(parent);
	lv_label_set_text(g->name, title);
	lv_obj_set_style_text_color(g->name, COL_DIM, 0);
	lv_obj_set_width(g->name, GAUGE_PCT_MAX_W);
	lv_obj_set_style_text_align(g->name, LV_TEXT_ALIGN_CENTER, 0);
	lv_obj_align(g->name, LV_ALIGN_TOP_MID, cx, GAUGE_UNIT_Y);

	/* The inner ring's own figure, small and dim under the countdown. The
	 * primary provider keeps the big number; this one is there to be
	 * noticed, not read first. */

	/* Both countdowns sit under the caption, stacked, each naming its own
	 * provider. Centred on the gauge whether there is one or two -- the
	 * second simply appears on the line below. */
	g->resets2_in_s = -1;
	g->countdown = lv_label_create(parent);
	lv_label_set_text(g->countdown, "--");
	lv_obj_set_style_text_color(g->countdown, COL_DIM, 0);
	lv_obj_set_width(g->countdown, GAUGE_CD_MAX_W);
	lv_obj_set_style_text_align(g->countdown, LV_TEXT_ALIGN_CENTER, 0);
	lv_obj_align(g->countdown, LV_ALIGN_TOP_MID, cx, GAUGE_CD_Y);
	/*
	 * Hidden, not deleted. render_countdown() and the usage setters go on
	 * writing to it every second from several places; deleting it would
	 * mean a NULL check at each one, and the object costs less than the
	 * chance of missing one. What it showed -- "--" until a reset time
	 * arrives -- was the row under the caption that was asked to go.
	 */
	lv_obj_add_flag(g->countdown, LV_OBJ_FLAG_HIDDEN);

}

static void render_countdown(struct gauge *g)
{
	char buf[FMT_COUNTDOWN_MAX];

	/*
	 * The real countdown always wins. The rate is what goes here when the
	 * source cannot say when the window rolls -- Claude Desktop with no
	 * Claude Code -- and it is a different KIND of statement, so it is
	 * never mixed with one: either a time or a rate, never both, never one
	 * standing in for the other while the other exists.
	 */
	if (g->resets_in_s < 0 && g->burn > 0) {
		fmt_burn(g->burn, buf, sizeof(buf));
		if (buf[0] != '\0') {
			lv_label_set_text(g->countdown, buf);
			return;
		}
	}
	fmt_countdown(g->resets_in_s, buf, sizeof(buf));
	/*
	 * A duration, and nothing else. The name used to ride with the number
	 * because the panel showed two providers at once and a bare figure had
	 * to be matched to one of them. One provider per page removes the
	 * question, so the answer stops being worth a line under both gauges.
	 */
	lv_label_set_text(g->countdown, buf);

}

#if HAVE_PER_MODEL
static const char *const sel_name[PEEK_ROWS] = {
	"7d", "FABLE",
};
static const char *const sel_label[PEEK_ROWS] = { "All models", "Fable" };

static double sel_pct(int sel)
{
	return sel == 1 ? model_fable : last_w_pct;
}
#endif

/* The weekly arc shows whichever source the peek card selected. The
 * countdown stays the overall weekly reset -- the per-model windows reset
 * with it. */
static void render_weekly(void)
{
#if HAVE_PER_MODEL
	double pct = sel_pct(weekly_sel);

	lv_label_set_text(weekly.name, sel_name[weekly_sel]);
#else
	/* One window, so the gauge never needs to say which one it is showing
	 * -- but it still says it, because "WEEKLY 7d" is the honest name for
	 * the number under it. */
	double pct = last_w_pct;

	lv_label_set_text(weekly.name, "7d");
#endif
	if (pct < 0) {
		lv_label_set_text(weekly.pct, "--%");
		lv_arc_set_value(weekly.arc, 0);
		return;
	}

	char buf[8];

	snprintf(buf, sizeof(buf), "%d%%", (int)pct_int(pct));
	lv_label_set_text(weekly.pct, buf);
	lv_arc_set_value(weekly.arc, arc_value(pct));
	lv_obj_set_style_arc_color(weekly.arc, severity(pct), LV_PART_INDICATOR);
}

#if HAVE_PER_MODEL
static void peek_fill(void)
{
	for (int i = 0; i < PEEK_ROWS; i++) {
		double pct = sel_pct(i);
		char val[8] = "--";
		char buf[24];

		if (pct >= 0) {
			snprintf(val, sizeof(val), "%d%%", (int)pct_int(pct));
		}
		snprintf(buf, sizeof(buf), "%s  %s", sel_label[i], val);
		lv_label_set_text(peek_row_lbl[i], buf);
		/* The selected row wears green, like a done checklist step. */
		lv_obj_set_style_bg_color(peek_row[i],
			i == weekly_sel ? COL_GREEN : COL_TRACK, 0);
		lv_obj_set_style_text_color(peek_row_lbl[i],
			i == weekly_sel ? COL_GREEN_INK : COL_TEXT, 0);
	}
}

static void peek_hide(void)
{
	peek_ttl = 0;
	lv_obj_add_flag(peek, LV_OBJ_FLAG_HIDDEN);
}

static void peek_row_cb(lv_event_t *e)
{
	weekly_sel = (int)(intptr_t)lv_event_get_user_data(e);
	cfg_set_weekly_sel((uint8_t)weekly_sel);	/* survives reboots */
	render_weekly();
	peek_hide();
}

/* LONG_PRESSED on the screen. */
static void peek_open_cb(lv_event_t *e)
{
	ARG_UNUSED(e);
	peek_fill();
	lv_obj_clear_flag(peek, LV_OBJ_FLAG_HIDDEN);
	peek_ttl = 8;
	peek_shown_ms = k_uptime_get();
}

/* CLICKED on the screen: dismiss -- but the release of the opening
 * long-press itself arrives as a click, so only later taps count. */
static void peek_scrim_cb(lv_event_t *e)
{
	ARG_UNUSED(e);
	if (peek && !lv_obj_has_flag(peek, LV_OBJ_FLAG_HIDDEN) &&
	    k_uptime_get() - peek_shown_ms > 600) {
		peek_hide();
	}
}
#endif /* HAVE_PER_MODEL */


/*
 * The bottom edge's cue: a face, drawn rather than written.
 *
 * It said "FACE" in words, which was honest and looked like a label for the
 * countdown above it rather than a control. There is no face glyph in the
 * Montserrat build LVGL ships, so this is three primitives -- two eyes and a
 * mouth -- in a 40x26 container that keeps them positioned relative to each
 * other instead of to the screen.
 *
 * The mouth is an arc with its lower half swept (30..150 degrees, where 0 is
 * east and angles run clockwise), which reads as a smile at this size where a
 * straight bar reads as a dash. Everything is COL_GREY, the same weight as
 * the other three cues: these point at somewhere to go, and none of them is
 * more important than the gauges they sit around.
 */
static void build_face_cue(lv_obj_t *scr)
{
	lv_obj_t *box = lv_obj_create(scr);

	lv_obj_set_size(box, FACE_CUE_W, FACE_CUE_H);
	lv_obj_align(box, LV_ALIGN_BOTTOM_MID, 0, -FACE_CUE_BOTTOM_OFF);
	lv_obj_set_style_bg_opa(box, LV_OPA_TRANSP, 0);
	lv_obj_set_style_border_width(box, 0, 0);
	lv_obj_set_style_pad_all(box, 0, 0);
	lv_obj_clear_flag(box, LV_OBJ_FLAG_SCROLLABLE);
	/* Not clickable, like the other cues: the invisible 200x40 strip
	 * ui_settings.c puts here is the control, and it is far larger. */
	lv_obj_clear_flag(box, LV_OBJ_FLAG_CLICKABLE);

	for (int i = 0; i < 2; i++) {
		lv_obj_t *eye = lv_obj_create(box);

		lv_obj_set_size(eye, 3, 3);
		lv_obj_set_style_radius(eye, LV_RADIUS_CIRCLE, 0);
		lv_obj_set_style_bg_color(eye, COL_GREY, 0);
		lv_obj_set_style_bg_opa(eye, LV_OPA_COVER, 0);
		lv_obj_set_style_border_width(eye, 0, 0);
		lv_obj_clear_flag(eye, LV_OBJ_FLAG_SCROLLABLE);
		lv_obj_align(eye, LV_ALIGN_TOP_MID, i == 0 ? -5 : 5, 2);
	}

	lv_obj_t *mouth = lv_arc_create(box);

	lv_obj_set_size(mouth, 15, 15);
	lv_obj_align(mouth, LV_ALIGN_TOP_MID, 0, 1);
	lv_arc_set_bg_angles(mouth, 30, 150);
	lv_arc_set_angles(mouth, 30, 150);
	lv_obj_set_style_arc_color(mouth, COL_GREY, LV_PART_MAIN);
	lv_obj_set_style_arc_width(mouth, 2, LV_PART_MAIN);
	lv_obj_set_style_arc_opa(mouth, LV_OPA_TRANSP, LV_PART_INDICATOR);
	lv_obj_remove_style(mouth, NULL, LV_PART_KNOB);
	lv_obj_clear_flag(mouth, LV_OBJ_FLAG_CLICKABLE);
}

static lv_obj_t *gauge_scr;

void usage_view_deinit(void)
{
	/* Free the gauge screen so it never coexists with the setup screen --
	 * with no PSRAM the LVGL heap cannot hold both. */
	built = false;
	boot_n = 0;
	boot_active = -1;
	/* These hang off gauge_scr and die with it. Nulling them matters
	 * because the setters below are called from the protocol thread and
	 * would otherwise write through a freed pointer between the delete and
	 * the next init. */
	provider_lbl = NULL;
	for (int i = 0; i < RAIL_PAGES_MAX; i++) {
		rail_dot[i] = NULL;
	}
	/*
	 * Both header indicators the same way, and for the same reason:
	 * usage_view_set_counts() and usage_view_set_status() both arrive on
	 * the protocol thread and both call refresh_dots(), whose `if (dot)`
	 * and `if (!pip[0])` guards are only guards if the pointers they test
	 * are nulled here. `dot` was missed when this list was written -- it
	 * hangs off gauge_scr like everything else above and dies with it.
	 *
	 * The counts themselves survive: they are the last thing the daemon
	 * said, not a widget. Nothing repaints the row at init -- it comes
	 * back on the next refresh_dots(), which is the next set_counts or
	 * set_status, the same way the health dot does.
	 */
	dot = NULL;
	for (int i = 0; i < PIP_MAX; i++) {
		pip[i] = NULL;
		pip_num[i] = NULL;
	}
	cur_page = 0;
	activity = USAGE_ACTIVITY_NONE;
	toast = NULL;
	toast_lbl = NULL;
	toast_ttl = 0;
	/*
	 * The comparison baseline goes too. The screen being torn down means
	 * the setup screen is coming up, and whatever the counts are when the
	 * gauges return, they are a first reading again -- not a change from
	 * whatever was true before the user went into settings.
	 */
	toast_have_prev = false;
#if HAVE_PER_MODEL
	peek = NULL;
	peek_ttl = 0;
#endif
	if (gauge_scr) {
		lv_obj_del(gauge_scr);
		gauge_scr = NULL;
	}
}

void usage_view_init(void)
{
	gauge_scr = lv_obj_create(NULL);
	lv_obj_t *scr = gauge_scr;

	lv_obj_clear_flag(scr, LV_OBJ_FLAG_SCROLLABLE);
	lv_obj_set_style_pad_all(scr, 0, 0);
	lv_obj_set_style_border_width(scr, 0, 0);
	lv_obj_set_style_bg_color(scr, COL_BG, 0);
	lv_obj_set_style_bg_opa(scr, LV_OPA_COVER, 0);
	lv_scr_load(scr);

	/*
	 * Header: brand to the RIGHT, quiet data left, the settings gear dead
	 * centre. The brand had the middle and the middle is now the only
	 * place a top affordance can go -- an arrow at TOP_MID landed on top
	 * of the word, which is the overlap that was reported.
	 *
	 * BRAND_RIGHT_OFF rather than -12: the status dot already sits 12 px in
	 * and is 12 wide, so this clears it by 6. Letter spacing drops 2 -> 1 to
	 * buy that back, keeping the word clear of the pip wall at PIP_WALL_X.
	 * The offset is a constant in usage_layout.h because the layout test
	 * measures the pip row's clearance against it -- while it was a literal
	 * here, that test was still modelling a centred wordmark.
	 */
	lv_obj_t *title = lv_label_create(scr);

	lv_label_set_text(title, BRAND_TEXT);
	lv_obj_set_style_text_color(title, COL_DIM, 0);
	lv_obj_set_style_text_letter_space(title, 1, 0);
	lv_obj_align(title, LV_ALIGN_TOP_RIGHT, -BRAND_RIGHT_OFF, TITLE_Y);

	dot = lv_obj_create(scr);
	lv_obj_set_size(dot, DOT_SZ, DOT_SZ);
	lv_obj_set_style_radius(dot, LV_RADIUS_CIRCLE, 0);
	lv_obj_set_style_border_width(dot, 0, 0);
	lv_obj_set_style_bg_color(dot, COL_GREY, 0);
	lv_obj_align(dot, LV_ALIGN_TOP_RIGHT, -12, HDR_ROW_Y);
	/* A swipe starting on this dot must still reach the screen below it,
	 * or the settings gesture goes dead whenever the touch lands here. */
	lv_obj_add_flag(dot, LV_OBJ_FLAG_GESTURE_BUBBLE);

	/*
	 * The execution-state row, in the gap between the clock and the brand.
	 *
	 * 6540287 removed a pip from the top-left corner and gave two reasons.
	 * One was that the corner was occupied by the clock -- it still is, and
	 * this row never asks for it: the 75 px between the clock and OVERWATCH was
	 * empty the whole time. The other was two unlabelled circles in one
	 * colour vocabulary, and the hint line below now names whichever
	 * condition fired. This is not that pip coming back, and it is not one
	 * pip: it is one per session.
	 *
	 * All PIP_MAX pairs are built once, here, and hidden. Showing and
	 * hiding is cheaper and steadier than creating and deleting objects on
	 * every poll, and it means every pointer below stays valid for the life
	 * of the screen -- refresh_dots() runs from the protocol thread and
	 * must never race a widget being built.
	 *
	 * Built like the health dot above, down to the gesture flag: marks that
	 * mean different things must still LOOK like one family, and a swipe
	 * starting on any of them must reach the screen below. They give up
	 * CLICKABLE, which the lone health dot never had to: lv_obj_create()
	 * sets it by default and LVGL's hit test walks children back to front,
	 * so a 74 px strip of clickable header would swallow the long-press
	 * that opens the card and the tap that dismisses it -- a dead band
	 * across the top of the screen. See rail_dot below, which learned this
	 * as a bug.
	 *
	 * Y is PIP_Y so an 8 px pip shares the 12 px health dot's centre line:
	 * the header's marks sit on one line even though they are two sizes.
	 */
	for (int i = 0; i < PIP_MAX; i++) {
		pip[i] = lv_obj_create(scr);
		lv_obj_set_size(pip[i], PIP_SZ, PIP_SZ);
		lv_obj_set_style_radius(pip[i], LV_RADIUS_CIRCLE, 0);
		lv_obj_set_style_border_width(pip[i], 0, 0);
		lv_obj_set_style_bg_color(pip[i], COL_GREY, 0);
		lv_obj_set_style_bg_opa(pip[i], LV_OPA_COVER, 0);
		lv_obj_align(pip[i], LV_ALIGN_TOP_LEFT,
			     PIP_X0 + i * PIP_PITCH, PIP_Y);
		lv_obj_add_flag(pip[i], LV_OBJ_FLAG_GESTURE_BUBBLE);
		lv_obj_clear_flag(pip[i], LV_OBJ_FLAG_CLICKABLE);
		lv_obj_add_flag(pip[i], LV_OBJ_FLAG_HIDDEN);

		/* Its tally, drawn only in counts mode. A label is not
		 * clickable in LVGL, so it needs no flag of its own. */
		pip_num[i] = lv_label_create(scr);
		lv_label_set_text(pip_num[i], "");
		lv_obj_set_style_text_color(pip_num[i], COL_GREY, 0);
		lv_obj_align(pip_num[i], LV_ALIGN_TOP_LEFT,
			     PIP_X0 + i * PIP_PITCH + PIP_SZ + PIP_NUM_GAP,
			     PIP_NUM_Y);
		lv_obj_add_flag(pip_num[i], LV_OBJ_FLAG_HIDDEN);
	}

	/* Carries the amber/red explanation. Empty when all is well: the gauges
	 * still hold real (if stale) numbers in those states, so they stay visible
	 * rather than being covered up.
	 */
	hint = lv_label_create(scr);
	lv_label_set_text(hint, "");
	/*
	 * Ellipsize rather than wrap. Every string this label held used to be
	 * a fixed literal that fit, so wrapping was unreachable; a project
	 * name removes that guarantee, and STATUS_Y (24) plus FONT_LINE_H
	 * (16) puts a second line at y=40. That used to land on the arcs at
	 * GAUGE_ARC_Y 44; they sit at 75 now, so this has 35 px of slack
	 * rather than none -- kept anyway, because the slack is a side
	 * effect of a layout choice and not a promise. Same call as
	 * provider_lbl.
	 */
	lv_label_set_long_mode(hint, LV_LABEL_LONG_DOT);
	/*
	 * The height is load-bearing, not redundant with the long mode above.
	 * LVGL only inserts the dots when the NEW text is taller than the
	 * label's CURRENT height (lv_label.c), and a LV_SIZE_CONTENT label
	 * (the class default, and what this was without this call) grows to
	 * fit the first over-long string it draws. The very next two-line
	 * string then measures against that already-grown height, the
	 * inequality flips, and it wraps down toward the arcs instead
	 * of ellipsizing -- the exact failure this label exists to prevent.
	 * Pinning the height keeps the comparison honest on every redraw, not
	 * just the first one.
	 */
	lv_obj_set_height(hint, FONT_LINE_H);
	lv_obj_set_style_text_color(hint, COL_DIM, 0);
	lv_obj_set_width(hint, STATUS_MAX_W);
	lv_obj_set_style_text_align(hint, LV_TEXT_ALIGN_CENTER, 0);
	lv_obj_align(hint, LV_ALIGN_TOP_MID, 0, STATUS_Y);



	/* Data age. The countdowns tick locally and keep moving even when the
	 * host is dead, so they look alive regardless; this is the only figure
	 * on screen that reveals whether the numbers are actually fresh.
	 */
	age_lbl = lv_label_create(scr);
	lv_label_set_text(age_lbl, "");
	lv_obj_set_style_text_color(age_lbl, COL_DIM, 0);
	/* Under the brand, not beside it. This and BRAND_TEXT were both at
	 * TOP_RIGHT -30 and drew straight through each other. */
	lv_obj_align(age_lbl, LV_ALIGN_TOP_RIGHT, -12, TITLE_Y + 18);

	/* Wall clock. Blank until a time source and timezone are known -- an
	 * empty label beats a confidently wrong one. */
	clock_lbl = lv_label_create(scr);
	lv_label_set_text(clock_lbl, "");
	lv_obj_set_style_text_color(clock_lbl, COL_DIM, 0);
	/*
	 * Under the brand, on the same row as the hint -- they share it and only
	 * one is ever visible. The clock holds it by default; a sentence takes it
	 * only while something wants a person. See usage_activity_needs_row().
	 */
	lv_obj_align(clock_lbl, LV_ALIGN_TOP_MID, 0, STATUS_Y);

	/* Whose numbers these are, directly under the brand. Blank until the
	 * daemon says -- an empty line reads as "nothing to report", where a
	 * placeholder would read as a provider actually named that. */
	for (int i = 0; i < RAIL_PAGES_MAX; i++) {
		rail_dot[i] = lv_obj_create(scr);
		lv_obj_set_size(rail_dot[i], RAIL_DOT_W, RAIL_H);
		lv_obj_set_style_radius(rail_dot[i], LV_RADIUS_CIRCLE, 0);
		lv_obj_set_style_border_width(rail_dot[i], 0, 0);
		lv_obj_set_style_bg_color(rail_dot[i], COL_GREY, 0);
		lv_obj_add_flag(rail_dot[i], LV_OBJ_FLAG_HIDDEN);
		/* A swipe that starts on a mark must still reach the screen,
		 * or the gesture dies exactly where its own affordance is. */
		lv_obj_add_flag(rail_dot[i], LV_OBJ_FLAG_GESTURE_BUBBLE);
		/*
		 * ...and neither may a TAP die there. lv_obj_create() sets
		 * CLICKABLE by default, and LVGL's hit test walks children
		 * back to front, so a dot -- created here, after the page
		 * zone was moved to the background -- won the hit and swallowed
		 * the tap. The dots carry no click handler, so nothing
		 * happened at all: a dead spot sitting exactly on the marks
		 * that advertise the page change. The arc (:325) and the peek
		 * card (:678) were cleared for the same reason; these were
		 * missed.
		 */
		lv_obj_clear_flag(rail_dot[i], LV_OBJ_FLAG_CLICKABLE);
	}

	/*
	 * Whose numbers these are -- and, with two providers, the control that
	 * changes it.
	 *
	 * It used to sit under the brand while the bottom of the screen
	 * carried a second line naming the OTHER provider: two names on one
	 * screen for one page, the header saying "Codex" while the pill said
	 * "Claude", and the reader left to work out which was which. One name
	 * is enough and the one worth keeping is the page you are on.
	 *
	 * Down here it is the same object as the control -- mk_page_zone puts
	 * the hit area over this band -- which is the idiom the settings
	 * panel's old "Main source" row used: the value IS the button.
	 */
	provider_lbl = lv_label_create(scr);
	lv_label_set_text(provider_lbl, "");
	lv_obj_set_style_text_color(provider_lbl, COL_TEXT, 0);
	lv_obj_set_style_bg_color(provider_lbl, COL_PANEL, 0);
	lv_obj_set_style_radius(provider_lbl, LV_RADIUS_CIRCLE, 0);
	lv_obj_set_style_pad_hor(provider_lbl, 10, 0);
	lv_obj_set_style_pad_ver(provider_lbl, PILL_PAD_V, 0);
	lv_label_set_long_mode(provider_lbl, LV_LABEL_LONG_DOT);
	lv_obj_set_style_text_align(provider_lbl, LV_TEXT_ALIGN_CENTER, 0);
	lv_obj_align(provider_lbl, LV_ALIGN_BOTTOM_MID, 0, -PILL_BOTTOM_OFF);
	/*
	 * Hidden by request. docs/multi-provider.md 4b makes this pill the tap
	 * path to the other provider - "the value IS the control" - so hiding
	 * it would normally strand the Codex page behind a swipe that lands
	 * half the time. It does not here: ui_settings.c's mk_page_zone is a
	 * second, invisible tap target doing the same job, and it stays.
	 */
	lv_obj_add_flag(provider_lbl, LV_OBJ_FLAG_HIDDEN);

	build_gauge(&session, scr, -GAUGE_CX, "5h");
	build_gauge(&weekly, scr, GAUGE_CX, "7d");


	/*
	 * Edge affordances: without them nobody discovers the swipes (user
	 * feedback 2026-07-16, and again 2026-09-23 -- "the user doesnt know
	 * how to use the thing"). Labels don't catch input, so swipes starting
	 * on them still reach the screen; the hit areas are the invisible
	 * strips ui_settings.c puts behind them.
	 *
	 * NAMED, not just pointed. Two bare chevrons said "there is something
	 * that way" and left which way to guess, which is survivable with two
	 * destinations and is not with four. The side edges are 44 px wide so
	 * they get an icon; the top and bottom have the room for a word and
	 * take it, because "SETTINGS" needs no learning and a gear does.
	 */
	static const struct {
		lv_align_t align;
		int dx, dy;
		const char *text;
	} edge[] = {
		{ LV_ALIGN_LEFT_MID,   6,  0, LV_SYMBOL_AUDIO },
		{ LV_ALIGN_RIGHT_MID, -6,  0, LV_SYMBOL_LIST },
		{ LV_ALIGN_TOP_MID,    0,  TITLE_Y, LV_SYMBOL_SETTINGS },
	};

	for (unsigned int i = 0; i < ARRAY_SIZE(edge); i++) {
		lv_obj_t *chev = lv_label_create(scr);

		lv_label_set_text(chev, edge[i].text);
		lv_obj_set_style_text_color(chev, COL_GREY, 0);
		lv_obj_align(chev, edge[i].align, edge[i].dx, edge[i].dy);
	}

	build_face_cue(scr);

#if HAVE_PER_MODEL
	/* The peek card, hidden until a long press. Created before the
	 * takeover overlay, which therefore keeps it unreachable while there
	 * is no data to peek at. */
	peek = lv_obj_create(scr);
	lv_obj_set_size(peek, 240, 152);
	lv_obj_set_style_radius(peek, 12, 0);
	lv_obj_set_style_bg_color(peek, COL_PANEL, 0);
	lv_obj_set_style_bg_opa(peek, LV_OPA_COVER, 0);
	lv_obj_set_style_border_color(peek, COL_TRACK, 0);
	lv_obj_set_style_border_width(peek, 1, 0);
	lv_obj_set_style_pad_all(peek, 0, 0);
	lv_obj_clear_flag(peek, LV_OBJ_FLAG_SCROLLABLE);
	lv_obj_clear_flag(peek, LV_OBJ_FLAG_CLICKABLE);
	lv_obj_center(peek);
	lv_obj_add_flag(peek, LV_OBJ_FLAG_HIDDEN);

	lv_obj_t *pt = lv_label_create(peek);

	lv_label_set_text(pt, "WEEKLY GAUGE SHOWS");
	lv_obj_set_style_text_color(pt, COL_DIM, 0);
	lv_obj_set_style_text_letter_space(pt, 1, 0);
	lv_obj_align(pt, LV_ALIGN_TOP_MID, 0, 12);

	/* 46 px rows, nearly card-wide: the 30 px originals were a miss-tap
	 * lottery on this panel (user feedback 2026-07-17). */
	for (int i = 0; i < PEEK_ROWS; i++) {
		peek_row[i] = lv_btn_create(peek);
		lv_obj_set_size(peek_row[i], 208, 46);
		lv_obj_set_style_shadow_width(peek_row[i], 0, 0);
		lv_obj_align(peek_row[i], LV_ALIGN_TOP_MID, 0, 40 + i * 54);
		lv_obj_add_event_cb(peek_row[i], peek_row_cb,
				    LV_EVENT_CLICKED, (void *)(intptr_t)i);

		peek_row_lbl[i] = lv_label_create(peek_row[i]);
		lv_label_set_text(peek_row_lbl[i], "");
		lv_obj_center(peek_row_lbl[i]);
	}

	lv_obj_add_event_cb(scr, peek_open_cb, LV_EVENT_LONG_PRESSED, NULL);
	lv_obj_add_event_cb(scr, peek_scrim_cb, LV_EVENT_CLICKED, NULL);

	/* The peek-card choice from last boot; render so the gauge's name
	 * says which window it shows from the very first frame. */
	weekly_sel = cfg_get_weekly_sel();
	if (weekly_sel >= PEEK_ROWS) {
		weekly_sel = 0;		/* stale NVS from an older layout */
	}
#endif /* HAVE_PER_MODEL */
	render_weekly();

	/*
	 * The status-change popup, built once and hidden, like every other
	 * transient on this screen. Created BEFORE the takeover below, which
	 * means the takeover covers it: a board that has never had data has
	 * nothing to announce, and a card floating over "CONNECTING" would be
	 * the panel talking about sessions it cannot see.
	 *
	 * No CLICKABLE and no event handler. It cannot be dismissed by hand
	 * and does not want to be -- five seconds is shorter than the reach --
	 * and a 288 px clickable strip across the bottom would swallow the tap
	 * that dismisses the peek card and the swipe that opens settings, the
	 * same way the pip row would have. It keeps its gestures bubbling for
	 * exactly that reason.
	 */
	toast = lv_obj_create(scr);
	lv_obj_set_size(toast, TOAST_MAX_W, TOAST_H);
	lv_obj_set_style_radius(toast, 10, 0);
	lv_obj_set_style_bg_color(toast, COL_PANEL, 0);
	lv_obj_set_style_bg_opa(toast, LV_OPA_COVER, 0);
	lv_obj_set_style_border_color(toast, COL_TRACK, 0);
	lv_obj_set_style_border_width(toast, 1, 0);
	lv_obj_set_style_pad_all(toast, TOAST_PAD_V, 0);
	lv_obj_clear_flag(toast, LV_OBJ_FLAG_SCROLLABLE);
	lv_obj_clear_flag(toast, LV_OBJ_FLAG_CLICKABLE);
	lv_obj_add_flag(toast, LV_OBJ_FLAG_GESTURE_BUBBLE);
	lv_obj_align(toast, LV_ALIGN_BOTTOM_MID, 0, -TOAST_BOTTOM_OFF);
	lv_obj_add_flag(toast, LV_OBJ_FLAG_HIDDEN);

	toast_lbl = lv_label_create(toast);
	lv_label_set_text(toast_lbl, "");
	/* One line, ellipsized. TOAST_H has room for exactly one, and a label
	 * left to wrap would push its second line out through the card. */
	lv_label_set_long_mode(toast_lbl, LV_LABEL_LONG_DOT);
	lv_obj_set_width(toast_lbl, TOAST_MAX_W - 2 * TOAST_PAD_V);
	lv_obj_set_height(toast_lbl, FONT_LINE_H);
	lv_obj_set_style_text_align(toast_lbl, LV_TEXT_ALIGN_CENTER, 0);
	lv_obj_center(toast_lbl);

	/* With no host there is genuinely nothing to show, so take over the whole
	 * screen. A board sitting quietly at "--%" reads as broken; this says what
	 * it is actually waiting for. Created last, so it sits above the gauges.
	 */
	overlay = lv_obj_create(scr);
	lv_obj_set_size(overlay, LV_PCT(100), LV_PCT(100));
	lv_obj_set_style_bg_color(overlay, COL_BG, 0);
	lv_obj_set_style_bg_opa(overlay, LV_OPA_COVER, 0);
	lv_obj_set_style_border_width(overlay, 0, 0);
	lv_obj_set_style_radius(overlay, 0, 0);
	lv_obj_clear_flag(overlay, LV_OBJ_FLAG_SCROLLABLE);
	/* Full-screen: without this a swipe starting here never reaches the
	 * screen, so the settings gesture is dead the whole time we're
	 * waiting for a host. */
	lv_obj_add_flag(overlay, LV_OBJ_FLAG_GESTURE_BUBBLE);
	lv_obj_center(overlay);

	/* The takeover has exactly one form: the CONNECTING bar. USB mode used
	 * to get its own "waiting for host" prose here; two different waiting
	 * screens for the same moment read as two different products (user
	 * feedback 2026-07-16). */
	wait_big = lv_label_create(overlay);

	lv_label_set_text(wait_big, "CONNECTING");
	lv_obj_set_style_text_color(wait_big, COL_TEXT, 0);
	lv_obj_set_style_text_font(wait_big, &lv_font_montserrat_20, 0);
	lv_obj_align(wait_big, LV_ALIGN_TOP_MID, 0, 44);

	boot_cnt = lv_label_create(overlay);
	lv_label_set_text(boot_cnt, "");
	lv_obj_set_style_text_color(boot_cnt, COL_DIM, 0);
	lv_obj_set_style_text_letter_space(boot_cnt, 2, 0);
	lv_obj_align(boot_cnt, LV_ALIGN_TOP_MID, 0, 88);

	for (int i = 0; i < BOOT_STEPS_MAX; i++) {
		boot_seg[i] = lv_obj_create(overlay);
		lv_obj_set_size(boot_seg[i], 76, 8);
		lv_obj_set_style_radius(boot_seg[i], 4, 0);
		lv_obj_set_style_border_width(boot_seg[i], 0, 0);
		lv_obj_set_style_bg_color(boot_seg[i], COL_TRACK, 0);
		lv_obj_set_style_bg_opa(boot_seg[i], LV_OPA_COVER, 0);
		lv_obj_clear_flag(boot_seg[i], LV_OBJ_FLAG_SCROLLABLE);
		lv_obj_add_flag(boot_seg[i], LV_OBJ_FLAG_HIDDEN);
	}

	boot_step = lv_label_create(overlay);
	lv_label_set_text(boot_step, "");
	lv_obj_set_style_text_color(boot_step, COL_DIM, 0);
	lv_obj_align(boot_step, LV_ALIGN_TOP_MID, 0, 146);

	/* Twenty seconds on the first step and the likeliest cause is the
	 * cable: a charge-only lead powers the board and carries no data --
	 * seen on the first Apple Silicon install (2026-08-30), where the
	 * Mac never enumerated the board at all. Blank until then. */
	boot_hint = lv_label_create(overlay);
	lv_label_set_text(boot_hint, "");
	lv_obj_set_width(boot_hint, 296);
	lv_label_set_long_mode(boot_hint, LV_LABEL_LONG_WRAP);
	lv_obj_set_style_text_align(boot_hint, LV_TEXT_ALIGN_CENTER, 0);
	lv_obj_set_style_text_color(boot_hint, COL_DIM, 0);
	lv_obj_align(boot_hint, LV_ALIGN_TOP_MID, 0, 178);

	built = true;
}

void usage_view_boot_begin(const char *const *steps, int nsteps)
{
	if (!built) {
		return;
	}
	boot_txt = steps;
	boot_n = MIN(nsteps, BOOT_STEPS_MAX);
	boot_active = -1;

	/* Center the row for this mode's segment count. */
	for (int i = 0; i < BOOT_STEPS_MAX; i++) {
		if (i < boot_n) {
			lv_obj_align(boot_seg[i], LV_ALIGN_TOP_MID,
				     i * 82 - (boot_n - 1) * 41, 118);
			lv_obj_clear_flag(boot_seg[i], LV_OBJ_FLAG_HIDDEN);
		} else {
			lv_obj_add_flag(boot_seg[i], LV_OBJ_FLAG_HIDDEN);
		}
	}
	usage_view_boot_stage(0);
}

bool usage_view_have_data(void)
{
	return have_data;
}

/* Push the current page's numbers into the one set of gauge widgets. */
static void render_gauges(void)
{
	struct page_data *p = &pg[cur_page];
	char buf[8];

	if (!built) {
		return;
	}

	/* A negative percentage means "the daemon does not have this number" --
	 * pc/statusline_source.py sends -1.0 when the window is absent from
	 * Claude Code's payload entirely. render_weekly() has always honoured
	 * that; this side did not, so an absent five_hour window rendered as a
	 * confident green 0%, which is the frozen-meter reading the sentinel
	 * exists to prevent. */
	if (p->s_pct < 0) {
		lv_label_set_text(session.pct, "--%");
		lv_arc_set_value(session.arc, 0);
	} else {
		snprintf(buf, sizeof(buf), "%d%%", (int)pct_int(p->s_pct));
		lv_label_set_text(session.pct, buf);
		lv_arc_set_value(session.arc, arc_value(p->s_pct));
		lv_obj_set_style_arc_color(session.arc, severity(p->s_pct),
					   LV_PART_INDICATOR);
	}
	session.resets_in_s = p->s_in_s;
	session.burn = p->burn;
	render_countdown(&session);

	/* No rate on the weekly gauge. A seven-day slope measured over half an
	 * hour is noise, and the daemon does not send one. */
	weekly.resets_in_s = p->w_in_s;
	render_countdown(&weekly);

	last_s_pct = p->s_pct;
	last_w_pct = p->w_pct;
	render_weekly();
	refresh_provider1();	/* the name under the brand follows the page */
}

/*
 * Whether "the reading is old" is true of the page being SHOWN.
 *
 * The status arrives as one flag describing the FIRST provider, and with two
 * providers that is a statement about one of two pages. A machine running
 * Claude Code all day with Codex touched once that morning has a stale codex
 * reading and a live claude one -- and the claude page was announcing
 * "Reading is old" over numbers that were updating in front of the user
 * (reported 2026-08-28). Freshness belongs to a reading, not to the panel.
 *
 * With one provider there is nothing to distinguish and the flag is the whole
 * truth, so it is taken as-is: pg[0].stale is only written by the daemon that
 * also sets the status, and a board talking to an older daemon never receives
 * p2_stale at all. Falling back to the status keeps that case behaving exactly
 * as it did.
 */
static bool stale_here(void)
{
	if (page_count() < 2) {
		return true;
	}
	return pg[cur_page].stale;
}

/*
 * The worse of a page's two windows.
 *
 * A rail mark has one colour and two windows to speak for, so it speaks for
 * whichever is closer to the wall. Averaging them would let a fresh weekly
 * quota talk a spent session down into amber, which is the reading that
 * matters getting hidden by the one that does not.
 */
static double page_worst(int i)
{
	double a = pg[i].s_pct, b = pg[i].w_pct;

	return a > b ? a : b;
}

/*
 * A page change, at whatever point through it the rail currently is.
 *
 * ONE description covers the whole thing: `rail_a` is the mark being left,
 * `rail_b` is the mark being reached, and `rail_pct` is how far the handover
 * has got. Settled is simply rail_a = -1 and rail_pct = 100.
 *
 * That unification is the fix for "the tail of the swipe is not showing". The
 * first version drove this only from the finger, and the finger does not
 * supply enough of it: the panel emits 2 to 5 reports for a whole stroke,
 * sometimes jumping 149 px between two of them, so the window between the drag
 * line and the threshold usually contains NO sample at all. The rail went from
 * idle to settled with nothing drawn in between -- correct, and invisible.
 *
 * So the finger starts the handover and an animation FINISHES it. Once the
 * swipe fires, the rail keeps travelling to the new page under its own power
 * over RAIL_SETTLE_MS instead of snapping. That part is drawn rather than
 * sampled, so it does not care how few reports the panel gave -- and it is
 * what is actually visible on a fast flick, where the whole stroke is over in
 * 70 ms.
 *
 * The rail is the right place for this and the only cheap one: it is already
 * the answer to "which page am I on", it is six pixels tall so redrawing it
 * costs nothing, and moving the weight from one mark to the other says which
 * page AND how far through in the same picture.
 */
#define RAIL_SETTLE_MS		200

/*
 * Both marks are named explicitly rather than one of them being "cur_page".
 *
 * They are not the same page at the two ends of this. DURING a stroke cur_page
 * is still the page being LEFT -- nothing has changed yet. After the swipe
 * fires cur_page has already advanced, so it is the page being REACHED. Keying
 * the drawing off it would mean the rail ran backwards across that instant,
 * which is the one moment it most needs to be continuous.
 */
static int rail_a = -1;		/* the mark being left, -1 when settled */
static int rail_b;		/* the mark being reached */
static int rail_pct = 100;	/* how far the handover has got */

/* Linear, in whole pixels: these are 6 and 16 px wide, so there is nothing an
 * easing curve could express that the panel could show. */
static int lerp_px(int a, int b, int pct)
{
	return a + (b - a) * pct / 100;
}

static void refresh_rail(void)
{
	int n = page_count();
	int span = n * RAIL_PITCH - (RAIL_PITCH - RAIL_DOT_W);
	int x = (SCR_W - span) / 2;
	bool handing_over;

	if (!rail_dot[0]) {
		return;
	}
	/*
	 * Settled means rail_b IS the current page, whatever moved cur_page.
	 * Most of this file's callers change the page without going through a
	 * swipe at all -- provider 2 arriving or disappearing falls back to
	 * page 0 on its own -- and without this the rail would keep drawing
	 * the page that was current when the last stroke ended.
	 */
	if (rail_a < 0) {
		rail_b = cur_page;
		rail_pct = 100;
	}
	handing_over = rail_a >= 0 && rail_a < n && rail_a != rail_b;
	for (int i = 0; i < RAIL_PAGES_MAX; i++) {
		int w = RAIL_DOT_W;
		lv_opa_t opa = LV_OPA_50;

		/* One page: nowhere to go, so there is no indicator to decode
		 * and no gesture to discover. The single-provider desk keeps
		 * exactly the screen it had. */
		if (i >= n || n < 2) {
			lv_obj_add_flag(rail_dot[i], LV_OBJ_FLAG_HIDDEN);
			continue;
		}
		/*
		 * The two marks trade places continuously: the one being left
		 * gives up exactly what the one being reached takes on. Half
		 * way through they are the same size, which is the honest
		 * picture of a page change that is under way and not finished
		 * -- true both of a stroke still being made and of one that has
		 * fired and is still landing.
		 */
		if (i == rail_b) {
			w = lerp_px(handing_over ? RAIL_DOT_W : RAIL_ACT_W,
				    RAIL_ACT_W, rail_pct);
			opa = (lv_opa_t)lerp_px(handing_over ? LV_OPA_50
							     : LV_OPA_COVER,
						LV_OPA_COVER, rail_pct);
		} else if (handing_over && i == rail_a) {
			w = lerp_px(RAIL_ACT_W, RAIL_DOT_W, rail_pct);
			opa = (lv_opa_t)lerp_px(LV_OPA_COVER, LV_OPA_50,
						rail_pct);
		}
		lv_obj_clear_flag(rail_dot[i], LV_OBJ_FLAG_HIDDEN);
		lv_obj_set_size(rail_dot[i], w, RAIL_H);
		/* Centred on its own slot whatever width it currently has, so
		 * it grows from the middle rather than off to one side. */
		lv_obj_set_pos(rail_dot[i],
			       x + i * RAIL_PITCH - (w - RAIL_DOT_W) / 2,
			       SCR_H - RAIL_BOTTOM_OFF - RAIL_H);
		lv_obj_set_style_bg_color(rail_dot[i],
					  pg[i].have ? severity(page_worst(i))
						     : COL_GREY, 0);
		lv_obj_set_style_bg_opa(rail_dot[i], opa, 0);
	}
	/* The pill names the page, so it follows the rail: both answer "which
	 * one am I on", and neither may be left behind by a change to the
	 * other. */
	refresh_provider1();
}

/*
 * Move one page, and say whether there is one to move to.
 *
 * This used to run straight from the gesture callback as a CUT -- retext the
 * labels, re-value the arcs, done in one repaint -- on the reasoning that a
 * vertical transition had no hardware path: the panel's scroll register moves
 * the screen sideways only, so up/down would mean a full LVGL redraw per
 * frame, and two or three stepping frames read as broken.
 *
 * That reasoning was about the SLIDE. The shipped transition is a WIPE
 * (ui_slide.c, UI_SLIDE_WIPE), which never touches the scroll register: it
 * paints the incoming screen one strip at a time, straight into the columns or
 * rows where it will be seen. That costs one full render for the whole
 * transition however finely it is chopped, and it does not care which axis it
 * chops along -- so the vertical direction was available the entire time and
 * the cut was paying a price the design had already stopped charging.
 *
 * The user's verdict on the cut, looking at the board: "the swipe up/down is
 * not showing like a swipe".
 *
 * So the page change is a transition now, which moves it out of the gesture
 * callback: ui_slide_run() drives lv_refr_now() itself and must not be
 * re-entered from inside lv_timer_handler(). The gesture flags the direction
 * and ui_settings_service() runs it from the mode loop, the same way opening
 * settings and the boot clip already do. can_page() is what lets the gesture
 * decline to arm a 650 ms blocking transition that would change nothing.
 */
bool usage_view_can_page(int delta)
{
	int n = page_count();
	int next = cur_page + delta;

	return built && n >= 2 && next >= 0 && next < n;
}

/*
 * The page change, as the gauges re-reading rather than the screen changing.
 *
 * Three transitions were tried on this axis before this one. A CUT was
 * reported as not looking like a swipe. A WIPE reads as a repaint, because
 * the two pages are the same layout and the boundary between them has nothing
 * to be made of. A wipe with a bright leading edge gave that boundary
 * something to see, and it still "doesn't feel natural" -- which it is not: a
 * bar sweeping the panel is an object that exists nowhere else on this device
 * and means nothing when it arrives.
 *
 * What was wrong with all three is that they were transitions between two
 * PICTURES. This is an instrument, and the honest motion for one is the needle
 * moving: the ring travels from the percentage it was showing to the one the
 * other provider is at, and the number under it counts along. Nothing is
 * covered, nothing slides, nothing is revealed. The screen does not change --
 * the reading does.
 *
 * It is also the only motion this hardware can render smoothly. A full-screen
 * transition costs a whole repaint however it is chopped up; the arcs and
 * their labels are a fraction of the panel, and LVGL invalidates only what
 * actually moved.
 */
#define PAGE_MORPH_MS		380
#define MORPH_STEPS		256
#define MORPH_MID		(MORPH_STEPS / 2)

static struct {
	double s_from, w_from;	/* what the rings were showing */
	double s_to, w_to;	/* what the page being moved to says */
	bool jump;		/* one side has no number: cut, do not travel */
	bool swapped;		/* the midpoint text swap has happened */
} morph;

/*
 * The words do not interpolate, so they cross the middle instead.
 *
 * A provider's NAME has no midpoint between "Claude" and "Codex", and neither
 * does a countdown -- rolling "6d 22h" towards "4d 15h" would be inventing a
 * duration that is true of nothing. They fade out, change while they cannot be
 * read, and fade back: the standard answer, and it costs only the label boxes.
 *
 * The numbers do NOT do this. They travel, because a percentage between two
 * percentages is a real percentage and watching it cross is the whole point.
 */
static void morph_text_opa(int32_t t)
{
	int d = t < MORPH_MID ? MORPH_MID - t : t - MORPH_MID;
	lv_opa_t o = (lv_opa_t)(d * LV_OPA_COVER / MORPH_MID);

	lv_obj_set_style_text_opa(provider_lbl, o, 0);
	lv_obj_set_style_text_opa(session.countdown, o, 0);
	lv_obj_set_style_text_opa(weekly.countdown, o, 0);
}

/* One ring: where it is now, on the way from one reading to the other. */
static void morph_arc(struct gauge *g, double pct)
{
	char buf[8];

	if (pct < 0) {
		lv_label_set_text(g->pct, "--%");
		lv_arc_set_value(g->arc, 0);
		return;
	}
	snprintf(buf, sizeof(buf), "%d%%", (int)pct_int(pct));
	lv_label_set_text(g->pct, buf);
	lv_arc_set_value(g->arc, arc_value(pct));
	/*
	 * Severity follows the value it is describing, so the ring changes
	 * colour where it crosses the threshold rather than at either end.
	 * Interpolating the colours themselves would put the ring through hues
	 * that mean nothing -- olive between green and amber -- and this
	 * palette's whole job is that a colour means one thing.
	 */
	lv_obj_set_style_arc_color(g->arc, severity(pct), LV_PART_INDICATOR);
}

static void morph_exec(void *unused, int32_t t)
{
	ARG_UNUSED(unused);

	if (!built) {
		return;
	}
	if (t >= MORPH_MID && !morph.swapped) {
		/*
		 * Halfway, with the words invisible: everything that cannot be
		 * interpolated changes here, in one go, behind the fade.
		 */
		morph.swapped = true;
		refresh_provider1();
		session.resets_in_s = pg[cur_page].s_in_s;
		session.burn = pg[cur_page].burn;
		weekly.resets_in_s = pg[cur_page].w_in_s;
		render_countdown(&session);
		render_countdown(&weekly);
	}
	morph_text_opa(t);

	if (morph.jump) {
		/*
		 * "--%" is not a number and there is no path between it and
		 * one. A ring travelling out of a blank reading would be
		 * animating a value the device does not have, so this side
		 * changes at the midpoint with the words.
		 */
		if (morph.swapped) {
			morph_arc(&session, morph.s_to);
			morph_arc(&weekly, morph.w_to);
		}
		return;
	}

	double k = (double)t / MORPH_STEPS;

	morph_arc(&session, morph.s_from + (morph.s_to - morph.s_from) * k);
	morph_arc(&weekly, morph.w_from + (morph.w_to - morph.w_from) * k);
}

static void morph_done(lv_anim_t *a)
{
	ARG_UNUSED(a);

	/*
	 * Land on the real values rather than on the last interpolated frame.
	 *
	 * The animation ends at t = MORPH_STEPS, so k is exactly 1 and the
	 * arithmetic already agrees -- but only in exact arithmetic. Calling
	 * the normal render path is what guarantees the screen is showing the
	 * page's own numbers afterwards, and it also restores anything the
	 * morph did not touch. The text opacity has to be put back by hand:
	 * it is a style, not a value, and nothing else in this file sets it.
	 */
	lv_obj_set_style_text_opa(provider_lbl, LV_OPA_COVER, 0);
	lv_obj_set_style_text_opa(session.countdown, LV_OPA_COVER, 0);
	lv_obj_set_style_text_opa(weekly.countdown, LV_OPA_COVER, 0);
	render_gauges();
	/*
	 * And only NOW re-ask the status question. page_step() asks it too,
	 * but at that moment last_s_pct/last_w_pct still describe the page
	 * being left -- they move here, in render_gauges() -- so the "almost
	 * used up" hint it produced belonged to the wrong page and stayed
	 * wrong until the next usage message, up to a poll interval later.
	 */
	usage_view_set_status(last_status);
}

/*
 * Drive the handover from an animation, once the finger has stopped supplying
 * it. See RAIL_SETTLE_MS.
 */
static void rail_settle_exec(void *unused, int32_t pct)
{
	ARG_UNUSED(unused);
	rail_pct = pct;
	refresh_rail();
}

static void rail_settled(lv_anim_t *a)
{
	ARG_UNUSED(a);
	/* The mark being left stops being a thing, which is what makes the
	 * next stroke's preview start from a settled rail rather than from the
	 * tail of this one. */
	rail_a = -1;
	rail_pct = 100;
	refresh_rail();
}

void usage_view_page_preview(int delta, int pct)
{
	int to = delta == 0 ? -1 : cur_page + delta;

	if (!built) {
		return;
	}
	/*
	 * Never while the rail is landing under its own power. The stroke that
	 * caused it has usually not been lifted yet, so its progress is still
	 * being published -- and honouring it would drag the rail back towards
	 * a handover that has already happened.
	 */
	if (lv_anim_get(NULL, rail_settle_exec) != NULL) {
		return;
	}
	if (to < 0 || to >= page_count() || pct <= 0) {
		/* Let go without committing: back to settled, at once. There is
		 * nothing to animate towards -- the page did not change -- and
		 * an eased retreat would read as a page change being undone
		 * rather than as one that never started. */
		to = cur_page;
		pct = 100;
		if (rail_a == -1 && rail_b == to && rail_pct == 100) {
			return;
		}
		rail_a = -1;
	} else {
		rail_a = cur_page;
	}
	/*
	 * Dropped when nothing changed, because this arrives every drain tick
	 * whether or not the finger moved -- ui_swipe publishes a state, not
	 * an event. Without this the rail would be re-laid-out a hundred times
	 * a second for a picture that is already correct.
	 */
	if (to == rail_b && pct == rail_pct) {
		return;
	}
	rail_b = to;
	rail_pct = pct;
	refresh_rail();
}

void usage_view_page_step(int delta)
{
	if (!usage_view_can_page(delta)) {
		/* A stroke that asked for a page that is not there still has to
		 * put the rail back; its preview is on screen. */
		usage_view_page_preview(0, 0);
		return;
	}

	/*
	 * Where the rings are NOW, not where the page being left says they
	 * should be. Paging twice quickly is the case that separates the two:
	 * the second swipe arrives mid-travel, and starting its animation from
	 * the page's stored value would snap the ring backwards before setting
	 * off again.
	 */
	morph.s_from = last_s_pct;
	morph.w_from = last_w_pct;

	cur_page += delta;

	morph.s_to = pg[cur_page].s_pct;
	morph.w_to = pg[cur_page].w_pct;
	morph.jump = morph.s_from < 0 || morph.s_to < 0 ||
		     morph.w_from < 0 || morph.w_to < 0;
	morph.swapped = false;

	/*
	 * The rail leads, and it FINISHES the handover the finger started.
	 *
	 * Carrying on from wherever the preview reached, rather than jumping,
	 * is what makes the swipe visible at all. A stroke gives the panel 2
	 * to 5 reports before it crosses the threshold and can jump 149 px
	 * between two of them, so the preview often never gets a frame -- the
	 * rail would go from idle to settled with nothing drawn in between.
	 * This part is drawn rather than sampled, so it does not care how few
	 * reports there were.
	 *
	 * rail_a is where cur_page was a moment ago; cur_page has already
	 * advanced above.
	 */
	/*
	 * Re-ask the status question for the page now in front.
	 *
	 * "Reading is old" is per page (see stale_here), so changing page can
	 * change the answer -- and nothing else would re-run it until the next
	 * usage message, up to a poll interval later. Re-applying the status
	 * already held recomputes the hint and the dot from the new page
	 * without inventing a reading.
	 *
	 * The age caption is per page for the same reason and needs the same
	 * re-ask: it is drawn from pg[cur_page].age, so without this the page
	 * you just arrived at wears the age of the one you left until the next
	 * one-second tick -- briefly captioning a live reading as hours old, or
	 * worse, an hours-old one as fresh.
	 */
	usage_view_set_status(last_status);
	render_age();

	rail_a = cur_page - delta;
	rail_b = cur_page;

	lv_anim_t ra;

	lv_anim_init(&ra);
	lv_anim_set_var(&ra, NULL);
	lv_anim_set_exec_cb(&ra, rail_settle_exec);
	lv_anim_set_values(&ra, rail_pct, 100);
	/* Time what is LEFT, so a stroke that had already dragged the rail
	 * most of the way finishes quickly instead of crawling the last few
	 * percent over a fifth of a second. */
	/* Floored, not just scaled: a stroke that dragged the rail all the way
	 * to 100 before firing would otherwise get a zero-length animation,
	 * whose completion callback is what puts rail_a back to -1. */
	lv_anim_set_time(&ra, MAX(30, RAIL_SETTLE_MS * (100 - rail_pct) / 100));
	lv_anim_set_path_cb(&ra, lv_anim_path_ease_out);
	lv_anim_set_completed_cb(&ra, rail_settled);
	lv_anim_delete(NULL, rail_settle_exec);
	lv_anim_start(&ra);

	refresh_rail();

	lv_anim_t a;

	lv_anim_init(&a);
	lv_anim_set_var(&a, NULL);
	lv_anim_set_exec_cb(&a, morph_exec);
	lv_anim_set_values(&a, 0, MORPH_STEPS);
	lv_anim_set_time(&a, PAGE_MORPH_MS);
	/*
	 * Eased at both ends. A needle that starts and stops abruptly reads as
	 * a jump with a delay in the middle; this is the one place on the panel
	 * where something is meant to look like it has mass.
	 */
	lv_anim_set_path_cb(&a, lv_anim_path_ease_in_out);
	lv_anim_set_completed_cb(&a, morph_done);
	/* Restarting replaces the running one rather than queueing a second
	 * animation against the same callback, so a fast double swipe travels
	 * once, to the page it ends on. */
	lv_anim_delete(NULL, morph_exec);
	lv_anim_start(&a);
}


/*
 * A window whose reset moment has passed is over, whatever percentage came
 * with it: the usage API keeps reporting the ended window (old utilization,
 * passed resets_at) for minutes afterwards, which left a stale gauge + "now"
 * on screen long past the reset (user-reported 2026-07-17). 0 remaining
 * seconds means "already reset" -- show the new, empty window instead, with
 * an unknown countdown (the next window starts on the next activity).
 */
void usage_view_update(double session_pct, int32_t session_resets_in_s,
		       double weekly_pct, int32_t weekly_resets_in_s)
{
	if (!built) {
		return;
	}

	if (session_resets_in_s == 0) {
		session_pct = 0;
		session_resets_in_s = -1;
	}
	if (weekly_resets_in_s == 0) {
		weekly_pct = 0;
		weekly_resets_in_s = -1;
	}

	pg[0].s_pct = session_pct;
	pg[0].w_pct = weekly_pct;
	pg[0].s_in_s = session_resets_in_s;
	pg[0].w_in_s = weekly_resets_in_s;
	pg[0].have = true;

	have_data = true;
	age_s = 0;
	refresh_rail();		/* page 0's mark, even while page 1 is showing */
	if (cur_page == 0) {
		render_gauges();
	}
	render_age();
	usage_view_set_status(USAGE_STATUS_OK);
}

/*
 * How old a reading has to be before its age is worth the caption.
 *
 * This was 120 s, and it was 120 s against the wrong clock: `age_s` counts
 * from the last MESSAGE, and the daemon sends one every 60 s whether or not
 * the figure changed (POLL_INTERVAL_S in claude_usage_bridge.py), so the
 * counter was zeroed twice as often as 120 could be reached. The caption has
 * therefore never once appeared on any board. What now feeds this is the
 * READING's own age, which the daemon measures and sends (pc/protocol.py,
 * `age_s`), and against that clock 120 s would be the opposite mistake:
 * Claude Desktop refreshes at best every 300 s, so a two-minute rule would
 * leave a permanent caption on a perfectly healthy panel.
 *
 * 600 s sits in the gap between Claude Desktop's two schedules -- 300 s
 * while its owner is at the machine, 900 s once they are not -- so ordinary
 * use stays uncaptioned and a reading that has stopped being refreshed says
 * so. Claude Code's status line rewrites on every render and is far below
 * this either way.
 */
#define AGE_CAPTION_MIN_S 600

static void render_age(void)
{
	char buf[FMT_COUNTDOWN_MAX];
	/*
	 * The daemon's figure when it sent one, our own count when it did not.
	 * An older daemon sends no age at all, and falling back to the message
	 * clock leaves it behaving exactly as it did rather than printing
	 * "never" over a reading we are holding.
	 */
	int32_t age = (pg[cur_page].have && pg[cur_page].age >= 0)
			      ? pg[cur_page].age
			      : age_s;

	/* Fresh data needs no caption: the varying-width "12s" next to the
	 * dot unbalanced the centered title (user feedback 2026-07-17). The
	 * age appears only once it is old enough to be worth knowing. */
	if (age >= 0 && age < AGE_CAPTION_MIN_S) {
		lv_label_set_text(age_lbl, "");
		return;
	}
	fmt_age(age, buf, sizeof(buf));
	lv_label_set_text(age_lbl, buf);
}

/* The countdown just hit zero: this window is over right now, never mind
 * that the API will keep echoing it for a while (see usage_view_update).
 * Flip the gauge to the new, empty window immediately. */
static void expire_session(void)
{
	pg[cur_page].s_in_s = -1;
	pg[cur_page].s_pct = 0;
	session.resets_in_s = -1;
	render_countdown(&session);
	last_s_pct = 0;
	lv_label_set_text(session.pct, "0%");
	lv_arc_set_value(session.arc, 0);
	lv_obj_set_style_arc_color(session.arc, severity(0), LV_PART_INDICATOR);
}

static void expire_weekly(void)
{
	pg[cur_page].w_in_s = -1;
	pg[cur_page].w_pct = 0;
	weekly.resets_in_s = -1;
	render_countdown(&weekly);
	last_w_pct = 0;
#if HAVE_PER_MODEL
	if (model_fable >= 0) {
		model_fable = 0;	/* per-model windows reset with the weekly */
	}
#endif
	render_weekly();
#if HAVE_PER_MODEL
	if (peek && !lv_obj_has_flag(peek, LV_OBJ_FLAG_HIDDEN)) {
		peek_fill();
	}
#endif
}

void usage_view_tick_1s(void)
{
	if (!built) {
		return;
	}

	if (boot_hint && overlay && !lv_obj_has_flag(overlay, LV_OBJ_FLAG_HIDDEN)
	    && boot_active == 0 && boot_n > 0) {
		if (++boot_hint_s == BOOT_HINT_AFTER_S) {
			lv_label_set_text(boot_hint,
					  "Plugged in and the app is running?\n"
					  "Try another USB cable.");
		}
	}

	/*
	 * EVERY page ticks, not just the one on screen. A window does not stop
	 * closing because nobody is looking at it, and a page that caught up
	 * only on arrival would show a stale figure at the moment it matters
	 * most -- the glance you take precisely because the rail went red.
	 */
	for (int i = 0; i < RAIL_PAGES_MAX; i++) {
		if (!pg[i].have) {
			continue;
		}
		/*
		 * The reading keeps ageing between messages. Without this the
		 * caption would freeze at whatever the last message said and
		 * only move once a minute, which on the source this exists for
		 * -- one that can go quiet for hours -- is the same lie in a
		 * smaller size.
		 */
		if (pg[i].age >= 0) {
			pg[i].age++;
		}
		if (pg[i].s_in_s > 0 && --pg[i].s_in_s == 0) {
			pg[i].s_in_s = -1;
			pg[i].s_pct = 0;
			if (i == cur_page) {
				expire_session();
			}
		}
		if (pg[i].w_in_s > 0 && --pg[i].w_in_s == 0) {
			pg[i].w_in_s = -1;
			pg[i].w_pct = 0;
			if (i == cur_page) {
				expire_weekly();
			}
		}
	}
	if (pg[cur_page].have) {
		session.resets_in_s = pg[cur_page].s_in_s;
		session.burn = pg[cur_page].burn;
		weekly.resets_in_s = pg[cur_page].w_in_s;
		render_countdown(&session);
		render_countdown(&weekly);
	}
	refresh_rail();

	if (age_s >= 0) {
		age_s++;
		render_age();
	}

	/*
	 * The popup's five seconds, on the same one-second clock as
	 * everything else here that expires. It stops on its own; nothing
	 * else in this file has to remember to take it down.
	 *
	 * This tick is driven from the mode loop, which is exactly the loop
	 * ui_sleep_run() blocks -- so a card can never tick down while the
	 * board is asleep. That is why one is never raised then.
	 */
	if (toast_ttl > 0 && --toast_ttl == 0) {
		toast_hide();
	}

#if HAVE_PER_MODEL
	if (peek_ttl > 0 && --peek_ttl == 0) {
		peek_hide();
	}
#endif
}
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
